mzuelch/CATs-Eurosynth/Modules/HAGIWO/Arduino VCO/ReadMe.md

<h1>Known Issues</h1>
<table>
	<tr>
		<th>#</th>
		<th>Solved?</th>
		<th>Hardware</th>
		<th>Firmware</th>
		<th>Issue</th>
	</tr>
	<tr>
		<td>001</td>
		<td>Yes</td>
		<td>X</td>
		<td></td>
		<td>Output level restricted to +/-2.5V by design. Amplification to eurorack standard (+/-5V) needed.</td>
	</tr>
	<tr>
		<td>002</td>
		<td>No</td>
		<td></td>
		<td>X</td>
		<td>Chord firmware produces low level output.</td>
	</tr>
</table>
