mzuelch/CATs-Eurosynth/Modules/Slim Line/Sample&Hold SMD/README.md

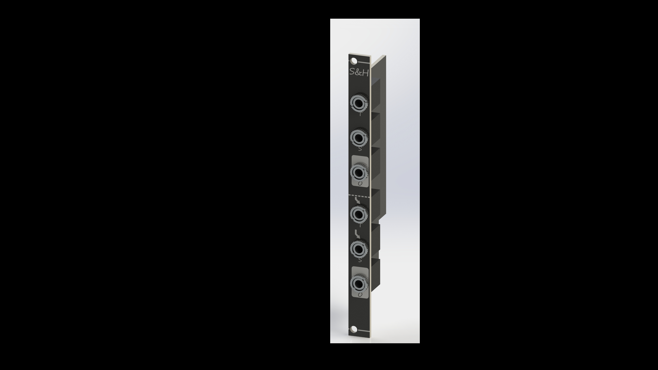
[picture p4: Modules/Slim Line/Sample&Hold/Documentation/Rendering.jpg]
Rendering
