mzuelch/CATs-Eurosynth/Modules/Slim Line/Single Attenuator/README.md

Simple 1CH Attentuator, but with a 60mm travel
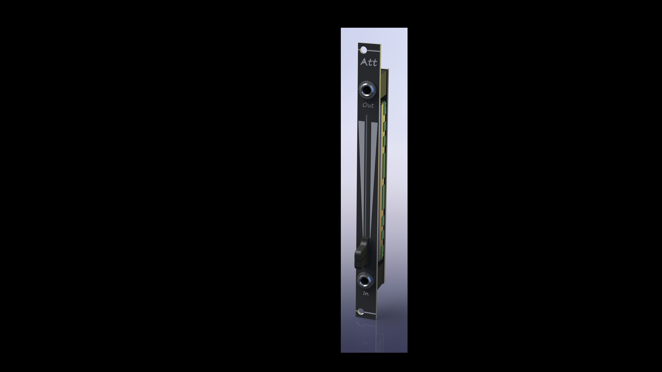
[picture p5: Modules/Slim Line/Single Attenuator/Documentation/Rendering.JPG]
Rendering
