mzuelch/CATs-Eurosynth/Modules/HAGIWO/Multiout/Firmware/Reworked/HAGIWO_Quantizer_Interrupt/ReadMe.md

<h2>Dependecies</h2>
<table>
	<tr>
		<th>Library</th>
		<th>Version</th>		
	</tr>
	<tr>
		<td>Adafruit GFX Library</td>
		<td>1.10.13</td>
	</tr>
	<tr>
		<td>Adafruit SSD1306</td>
		<td>2.5.1</td>
	</tr>
	<tr>
		<td>EncoderButton</td>
		<td>1.0.4</td>
	</tr>
	<tr>
		<td>FlashStorage_SAMD</td>
		<td>1.3.2</td>
	</tr>
</table>
