mzuelch/CATs-Eurosynth/Modules/Slim Line/Buffered Multiple SMD/Documentation/Handbuch.pdf

# Buffered Multiple

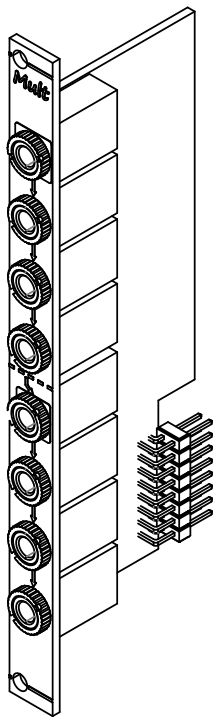
[picture p8: figure]

2 HP Width

39mm w/o Connector

+12V: 15mA

-12V: 15mA

Maximum Depth

Current Draw

## cations fi Technical Speci

## Function

This is a dual buffered 1-in-3 multiple. The signal applied to the input socket appears as a buffered signal at the three output sockets. Each output has it's own buffer, i.e. the three output sockets are not simply connected to each other. The lower output of the upper unit is normalled in the factory to the input of the lower unit. That way the module works as a single 1-in-6 buffered multiple provided that no signal is applied to the input of the lower unit.

## Installation

When installing or removing a module from your case always turn the power to the case and ffo disconnect the power cable. Failure to do so may result in serious injury

or equipment damage.

Ensure the 10-pin connector on the power cable is connected correctly to the module before proceeding.

The red stripe on the cable must line up with the -12V pins on the module’s power connector. The pins are indicated with the label

-12V, a white stripe next to the connector, the words “red”, or

some combination of those

indicators.

# CATs EuroSynth

Dr. Michael Zülch
cats.synth@gmx.de
