mzuelch/CATs-Eurosynth/Modules/Slim Line/Rectifier SMD/Documentation/Handbuch.pdf

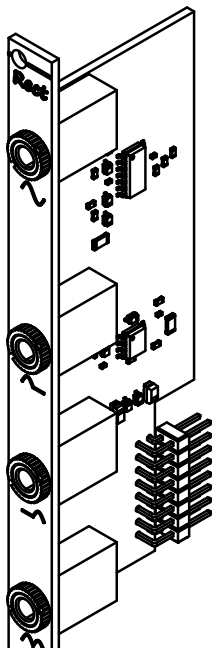
[picture p9: figure]

# CATs EuroSynth

Dr. Michael Zülch
cats.synth@gmx.de

# Precision Rectifier


2 HP Width

39mm w/o Connector

+12V: 15mA

-12V: 15mA

Maximum Depth

Current Draw

# cations fi Technical Speci

# Function

This is a combined halfwave and fullwave er. It can be used as an AC to DC fi precision recti converter, a distortion, a complex waveform generator, a frequency doubler, a clock doubler or even as part of an envelope follower.

Any bipolar signal provided signal (+/-10V) inluding audio signals provided at the input will erent ff be available on the three outputs in di

form.

will provide the signals positive values Output 1 as they are and cut negative values to 0V.

will do the same but with an inverted Output 2 signal, so originally positive values will be cut to

0V and negative values will be made positive.

ed version of the fi provides a fully reci Output 3 input. Positive inputs will be sent as it is, negative portions of the signal will be made positive and also sent to the output.

# Installation

When installing or removing a module from your case always turn the power to the case and ffo disconnect the power cable. Failure to do so may result in serious injury

or equipment damage.

Ensure the 10-pin connector on the power cable is connected correctly to the module before proceeding.

The red stripe on the cable must line up with the -12V pins on the module’s power connector. The pins are indicated with the label

-12V, a white stripe next to the connector, the words “red”, or

some combination of those

indicators.
