mzuelch/CATs-Eurosynth/Modules/Slim Line/Voltage Controlled Switch/Documentation/Handbuch.pdf

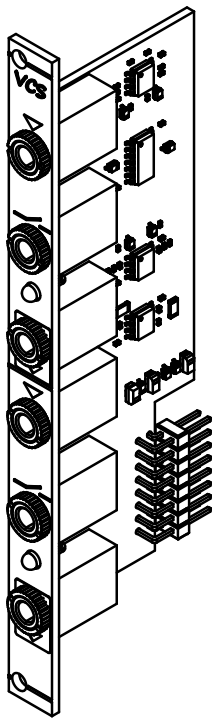
[picture p10: figure]

# CATs EuroSynth

Dr. Michael Zülch
cats.synth@gmx.de

# Voltage Controlled Switch


2 HP Width

39mm w/o Connector

+12V: 40mA

-12V: 10mA

Maximum Depth

Current Draw

# cations fi Technical Speci

# Function

The module provides two completely independent voltage controlled switches.

The switching is activated with a control voltage at a switching threshold of about 120mV and its status is indicated by LED.

The switches are unidirectional and are routing

only from In to Out.

The switches accept signals in a wide range

+/-10V are able to switch audio grade signals but are also suitable for gates, triggers, and

control voltages.

In

## In In

## Gate

## Gate Gate

## Out

## Out Out

⇨

⇨

⇨

⇨

⇦

⇦

# Installation

When installing or removing a module from your case always turn the power to the case and ffo disconnect the power cable. Failure to do so may result in serious injury

or equipment damage.

Ensure the 10-pin connector on the power cable is connected correctly to the module before proceeding.

The red stripe on the cable must line up with the -12V pins on the module’s power connector. The pins are indicated with the label

-12V, a white stripe next to the connector, the words “red”, or

some combination of those

indicators.
