mzuelch/CATs-Eurosynth/Modules/Standard Line/LFO/README.md

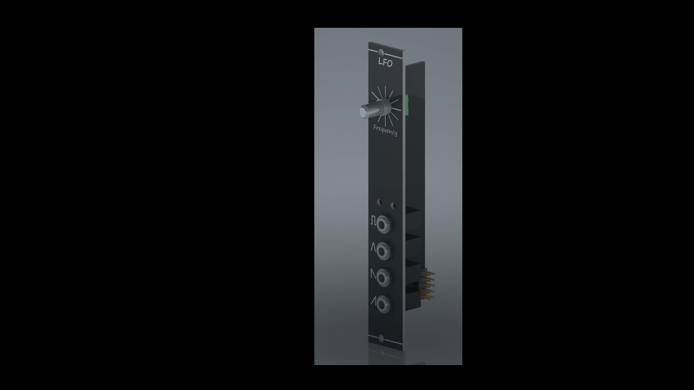
[picture p12: Modules/Haraldswerk/NGF-E LFO/Documentation/Rendering.jpg]
Rendering
