mzuelch/CATs-Eurosynth/Modules/YuSynth/Improved Steiner VCF/README.md

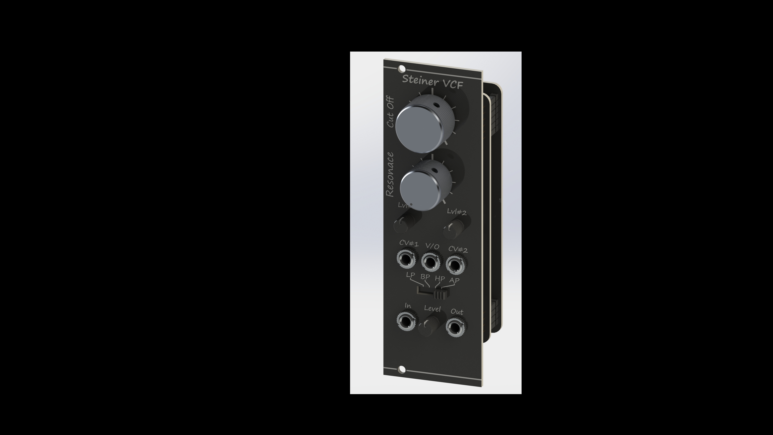
[picture p13: Modules/YuSynth/Improved Steiner VCF/Documentation/Rendering.jpg]
Rendering
