mzuelch/CATs-Eurosynth/Modules/Standard Line/Baby8 Sequencer/README.md

Baby8 Sequencer
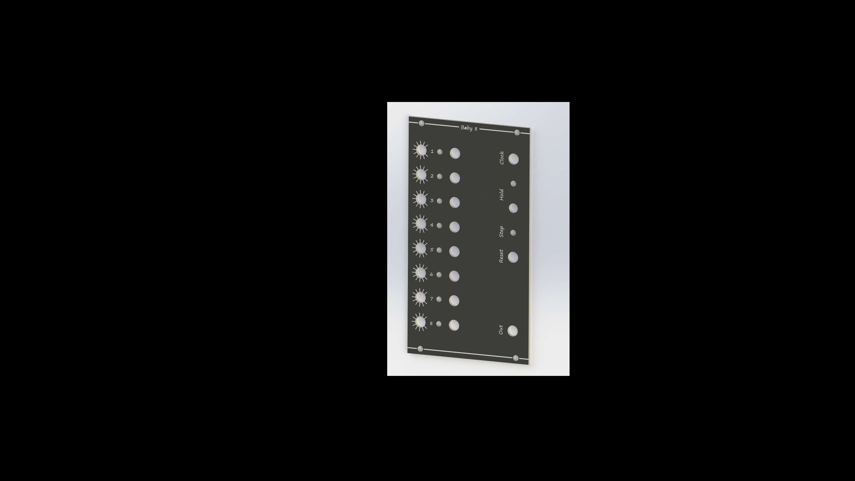
[picture p14: Modules/Standard Line/Baby8 Sequencer/Documentation/Rendering.jpg]
Rendering
