mzuelch/CATs-Eurosynth/Modules/MFOS/Dual VCA #2/README.md

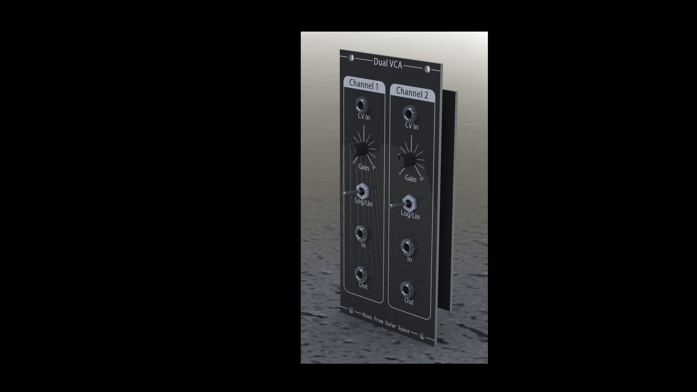
[picture p15: Modules/MFOS/Dual VCA #2/Documentation/Rendering.JPG]
Rendering
