mzuelch/CATs-Eurosynth/Modules/Slim Line/Clock Divider/Documentation/Handbuch.pdf

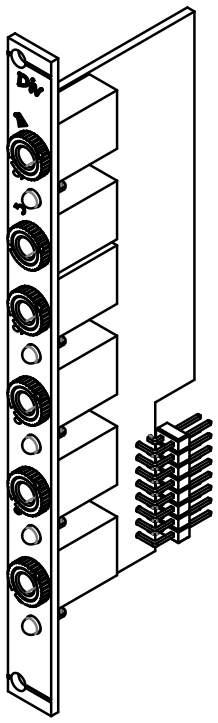
[picture p17: figure]

# CATs EuroSynth

Dr. Michael Zülch
cats.synth@gmx.de

# Clock Divider

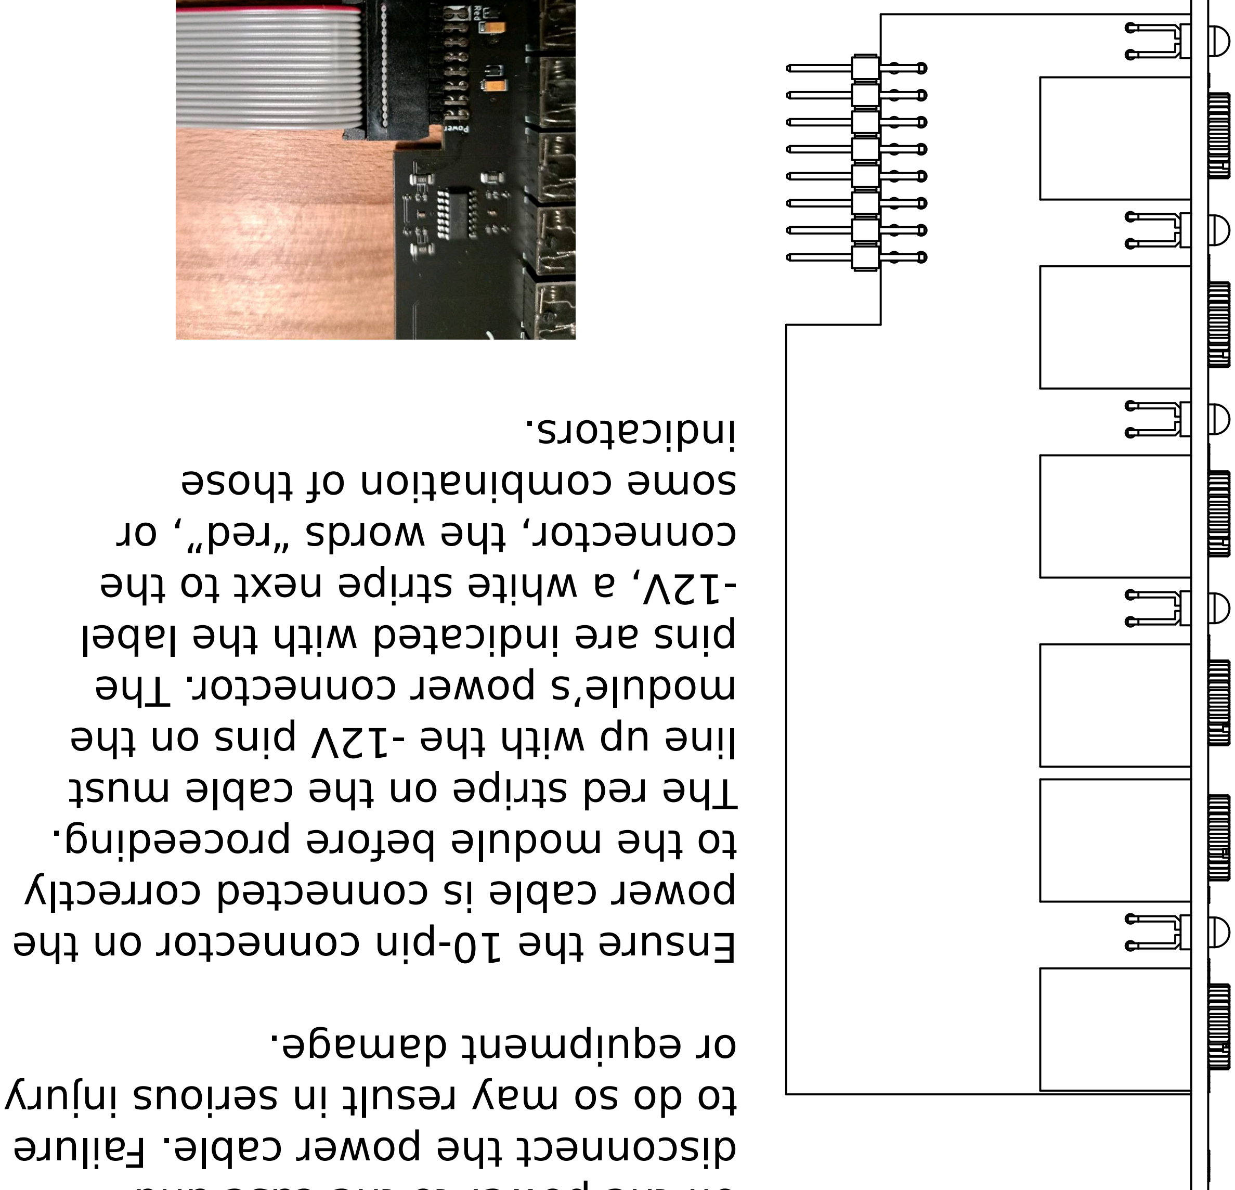
[picture p18: figure]
disconnect the power cable. Failure; to do so may result in serious injury; or equipment damage.; Ensure the 10-pin connector on the; power cable is connected correctly; to the module before proceeding.; The red stripe on the cable must; line up with the -12V pins on the; module’s power connector. The; pins are indicated with the label; -12V, a white stripe next to the; connector, the words “red”, or; some combination of those; indicators.

# Installation

When installing or removing a module from your case always turn the power to the case and ffo

2 HP Width

39mm w/o Connector

+12V: 80mA

-12V: 5mA

Maximum Depth

Current Draw

# cations fi Technical Speci

# Function

The module is a frequency divider for clock, trigger or gate signals, designed to be a source of lower frequencies, particularly for rhythm uses.

The clock input (CLK) will take any signal +/-10V.

erent ff At the outputs, you have access to four di sub-divided clock signals, from half the clock frequency down to 1/16 (Q1-Q4). The low/high levels of the output signals are 0V and about +5V.

The module also has a reset (RST) input.

Whenever a reset signal is sensed, all outputs are

set to 0V.

## CLK

## RST

Q1

Q2

Q3

Q4

CLK RST Q1 Q2Q3 Q4

⇨

⇨

⇦

⇦

⇦

⇦
