mzuelch/CATs-Eurosynth/Modules/CGS/Analog Switch Matrix/Documentation/Rendering.jpg

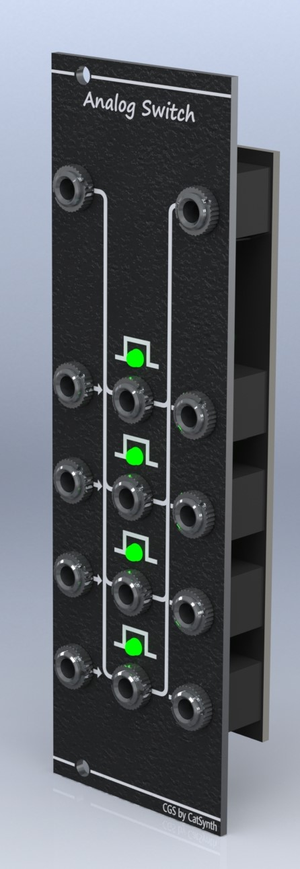
Modules/CGS/Analog Switch Matrix/Documentation/Rendering.jpg
