mzuelch/CATs-Eurosynth/Modules/HAGIWO/4Ch Sample Player/Electronics/Front/HAGIWO Sampler Front.png

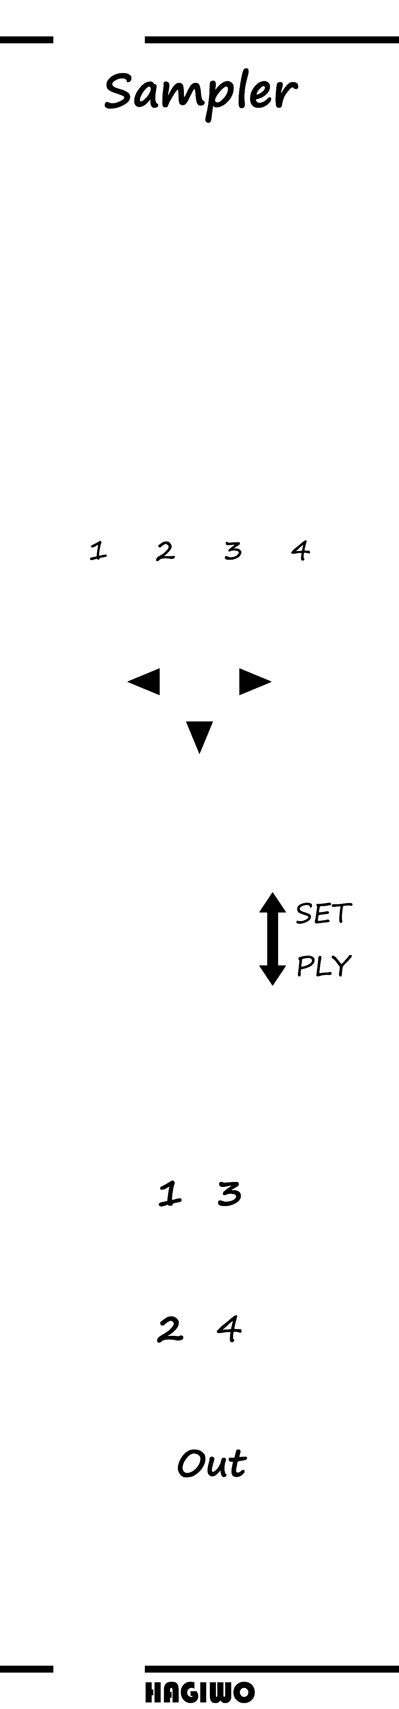
Modules/HAGIWO/4Ch Sample Player/Electronics/Front/HAGIWO Sampler Front.png
