mzuelch/CATs-Eurosynth/Modules/HAGIWO/Arduino VCO/Mechanics/HAGIWO Arduino VCO 2Op FM Front.png

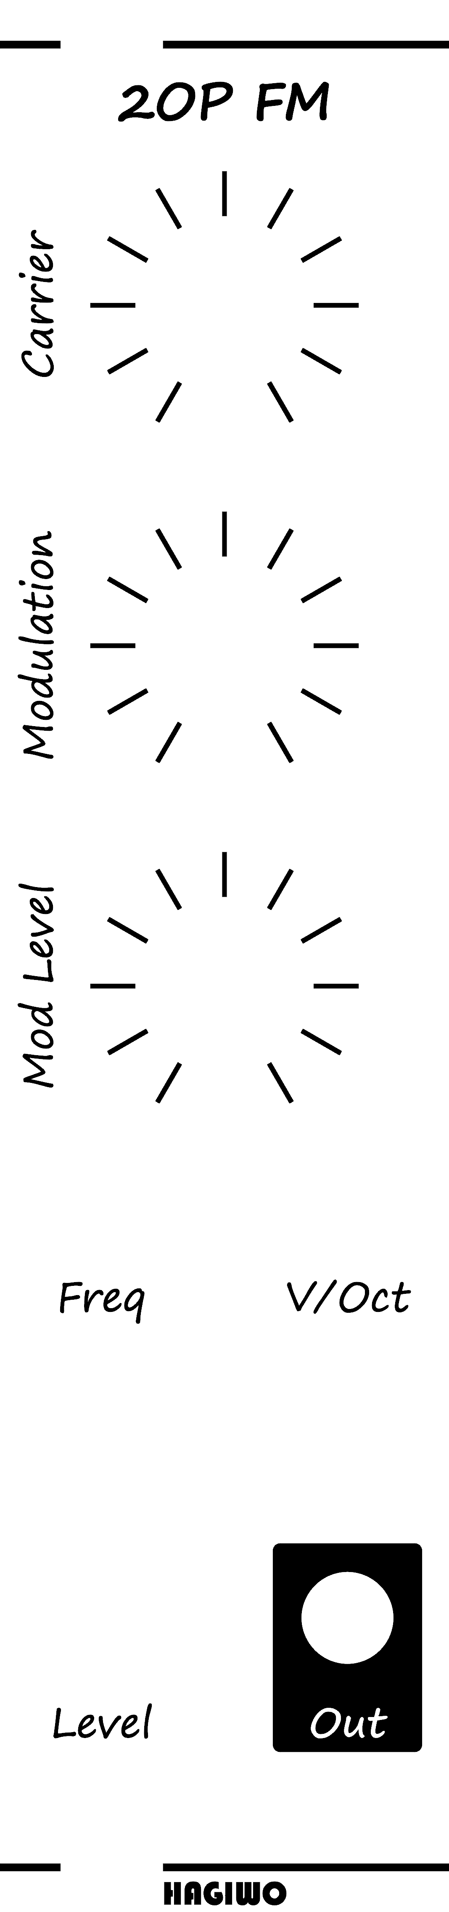
Modules/HAGIWO/Arduino VCO/Mechanics/HAGIWO Arduino VCO 2Op FM Front.png
