mzuelch/CATs-Eurosynth/Modules/HAGIWO/Multiout/Mechanics/HAGIWO Quantizer Frontpanel.png

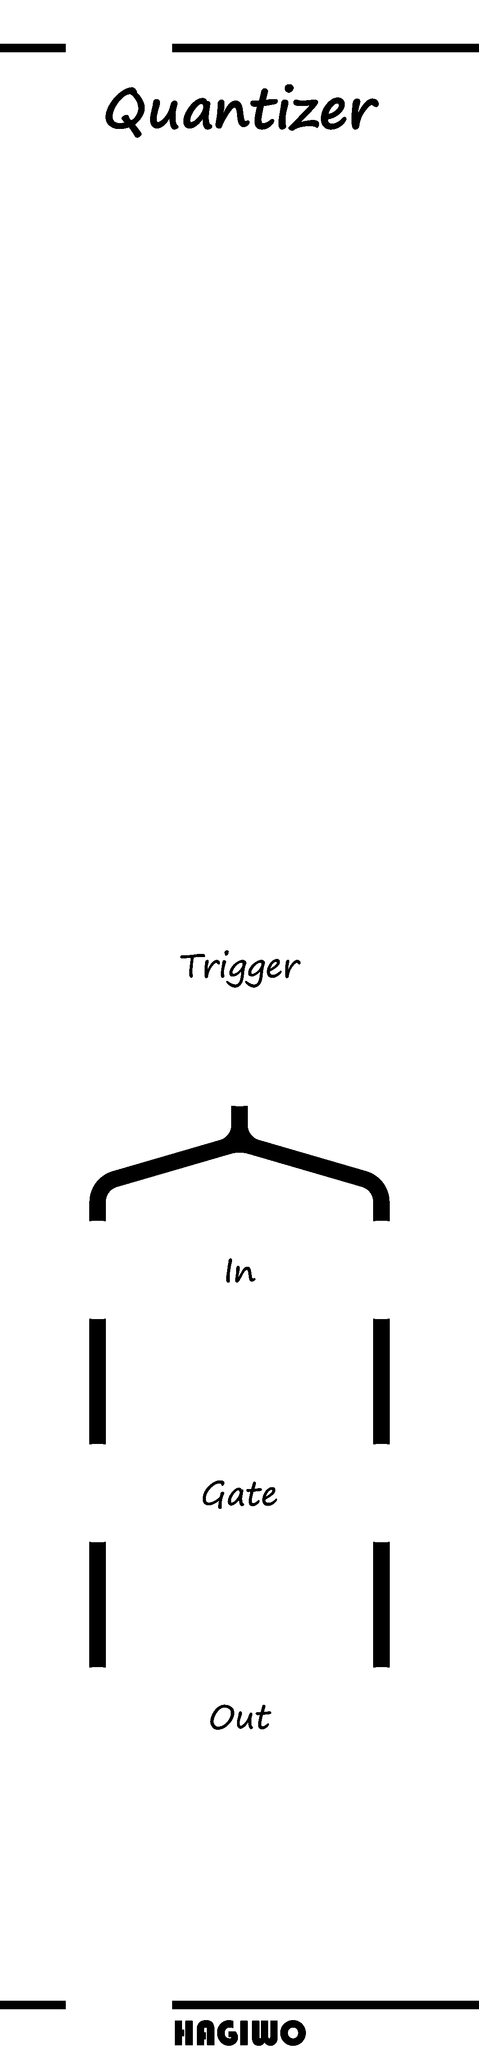
Modules/HAGIWO/Multiout/Mechanics/HAGIWO Quantizer Frontpanel.png
