mzuelch/CATs-Eurosynth/Modules/HAGIWO/Sync LFO/Mechanics/HAGIWO Sync LFO Front.png

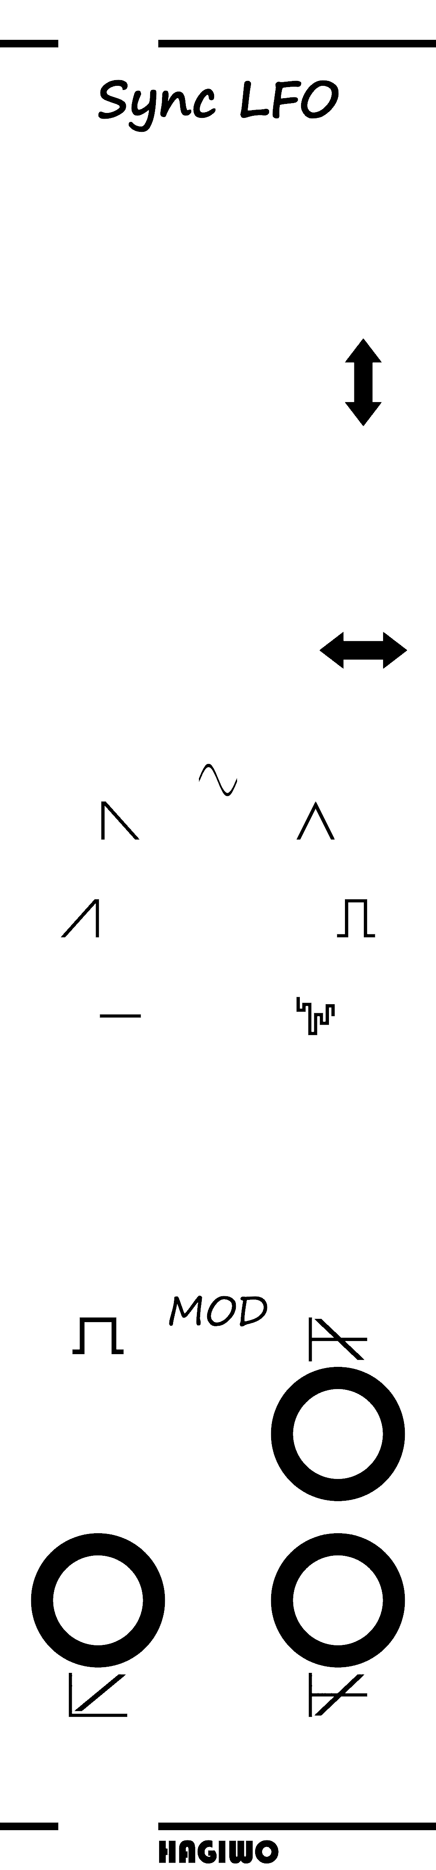
Modules/HAGIWO/Sync LFO/Mechanics/HAGIWO Sync LFO Front.png
