mzuelch/CATs-Eurosynth/Modules/Mechanicals/Cases/Case 1x3HE 84HP.JPG

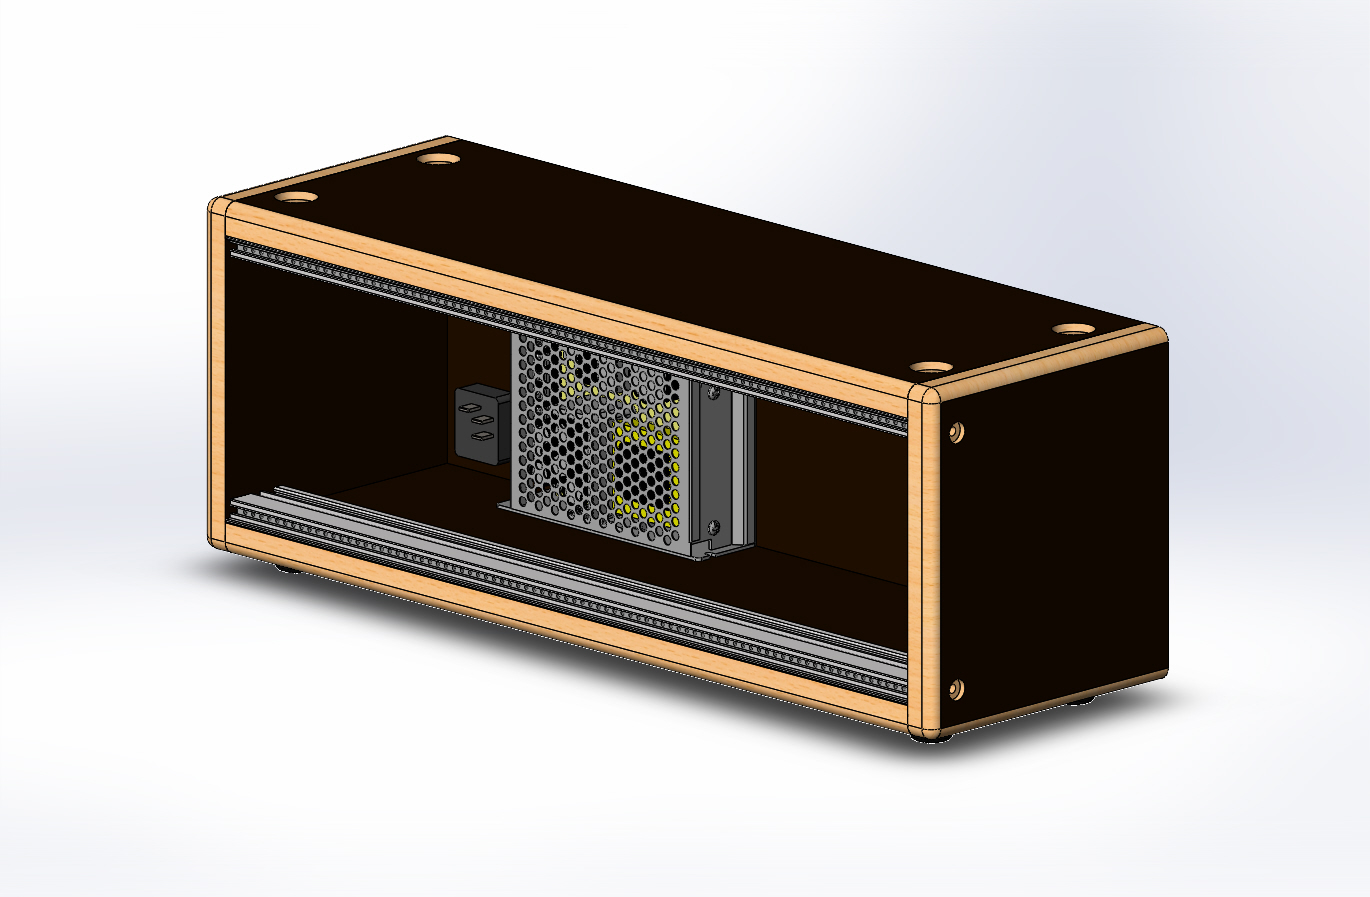
Modules/Mechanicals/Cases/Case 1x3HE 84HP.JPG
