mzuelch/CATs-Eurosynth/Modules/Mechanicals/Cases/Case 2x3HE 84HP.JPG

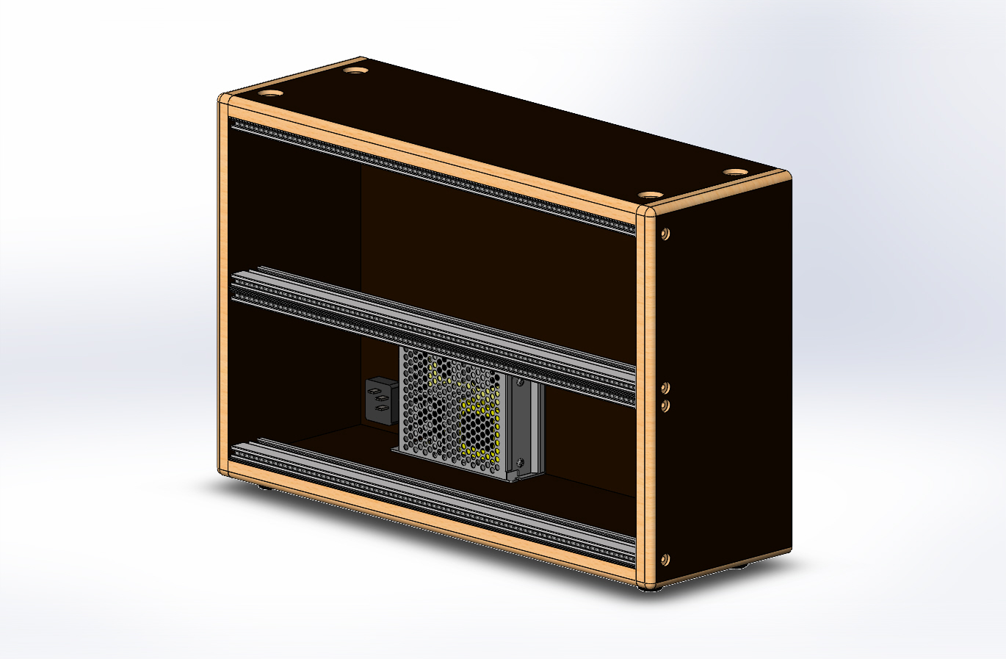
Modules/Mechanicals/Cases/Case 2x3HE 84HP.JPG
