mzuelch/CATs-Eurosynth/Modules/Mechanicals/Cases/Case 3x3HE 84HP.JPG

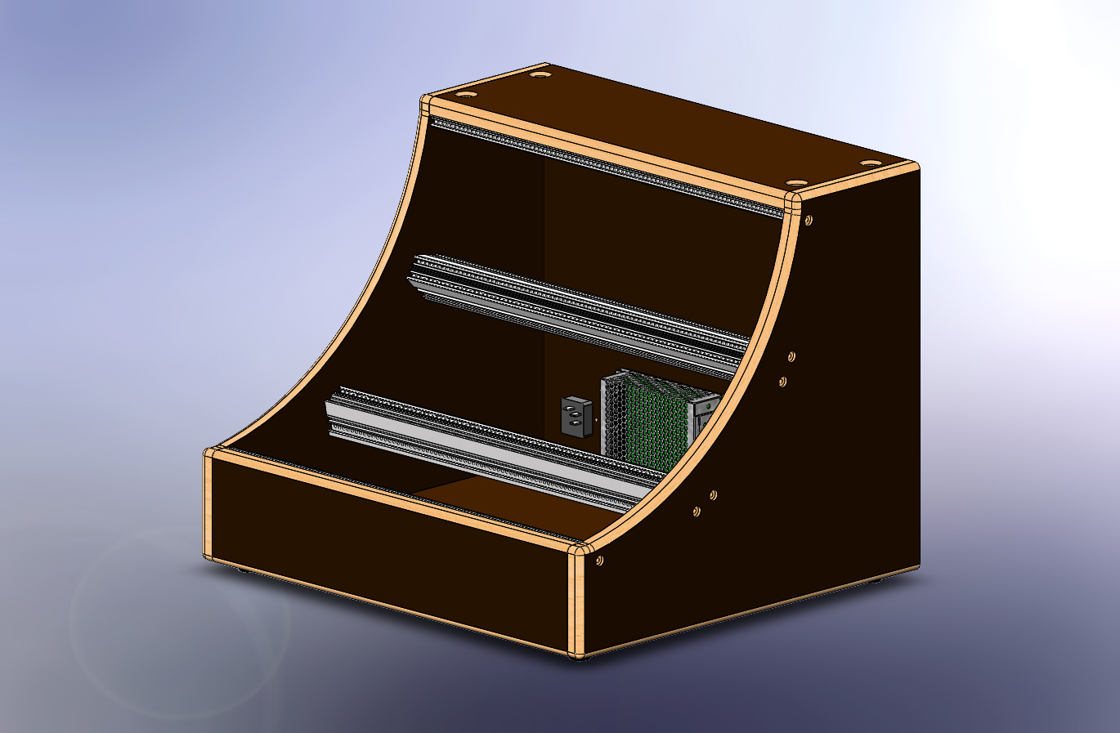
Modules/Mechanicals/Cases/Case 3x3HE 84HP.JPG
