mzuelch/CATs-Eurosynth/Modules/Slim Line/Buffered Multiple SMD/Documentation/20230219_085442.jpg

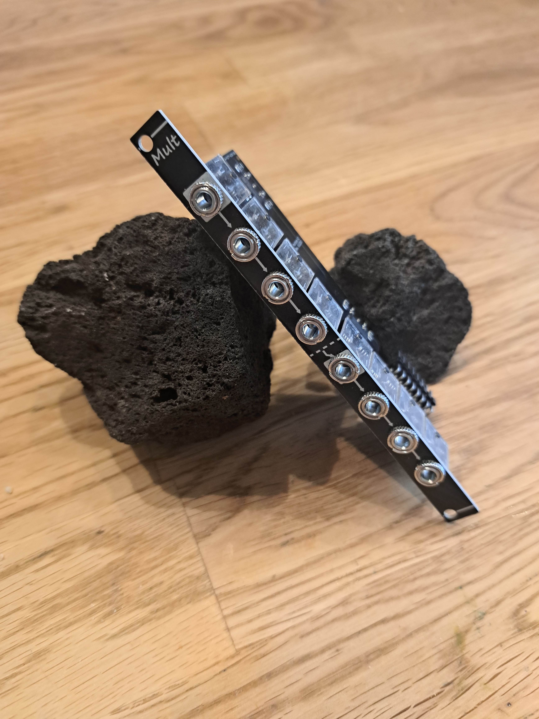
Modules/Slim Line/Buffered Multiple SMD/Documentation/20230219_085442.jpg
