mzuelch/CATs-Eurosynth/Modules/Slim Line/Buffered Multiple SMD/Documentation/Handbuch Seite 2.png

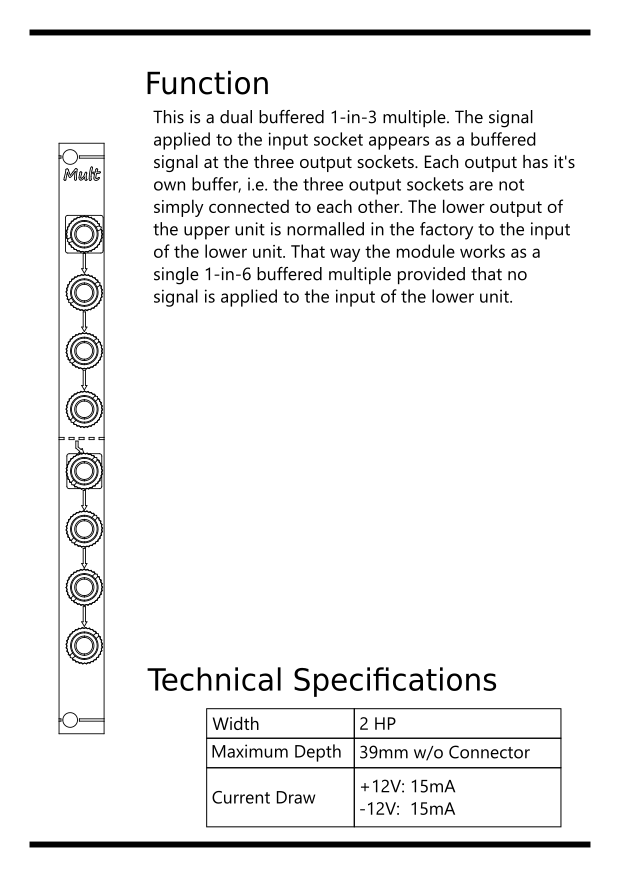
Modules/Slim Line/Buffered Multiple SMD/Documentation/Handbuch Seite 2.png
