mzuelch/CATs-Eurosynth/Modules/Slim Line/Clock Divider/Mechanics/Slimline Clock Divider Module Front.JPG

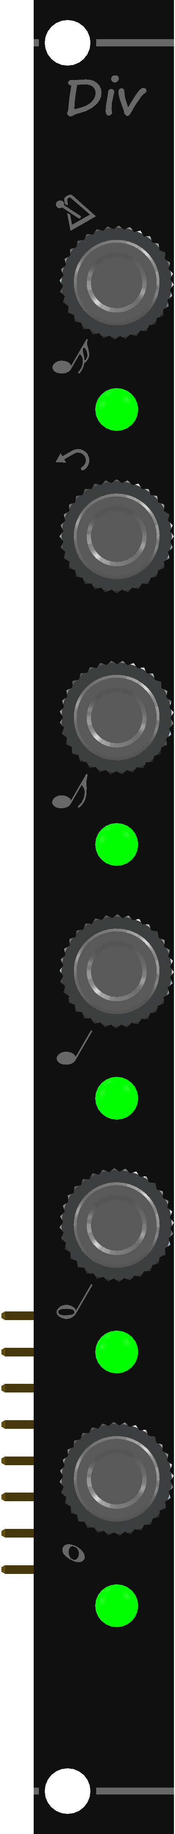
Modules/Slim Line/Clock Divider/Mechanics/Slimline Clock Divider Module Front.JPG
