mzuelch/CATs-Eurosynth/Modules/Slim Line/Clock Divider/Mechanics/Slimline Clock Divider V2 Front.png

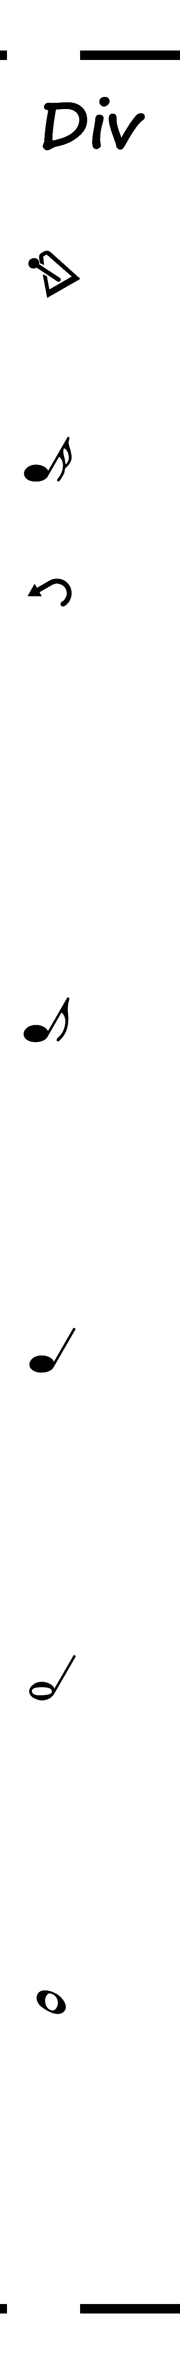
Modules/Slim Line/Clock Divider/Mechanics/Slimline Clock Divider V2 Front.png
