mzuelch/CATs-Eurosynth/Modules/Slim Line/Precision Adder/Mechanics/Slimline Precision Adder Front.png

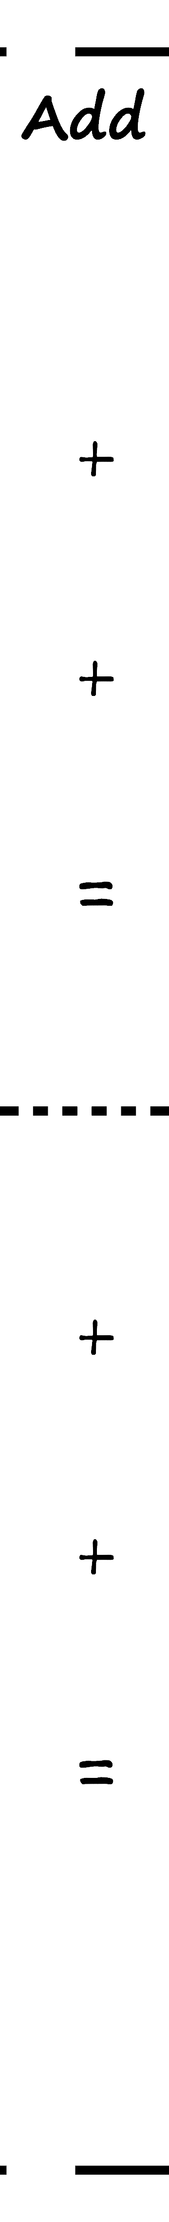
Modules/Slim Line/Precision Adder/Mechanics/Slimline Precision Adder Front.png
