mzuelch/CATs-Eurosynth/Modules/Slim Line/Rectifier SMD/Documentation/ec778fda-3ce0-42d2-8429-7ae5b2f354bd.jpeg

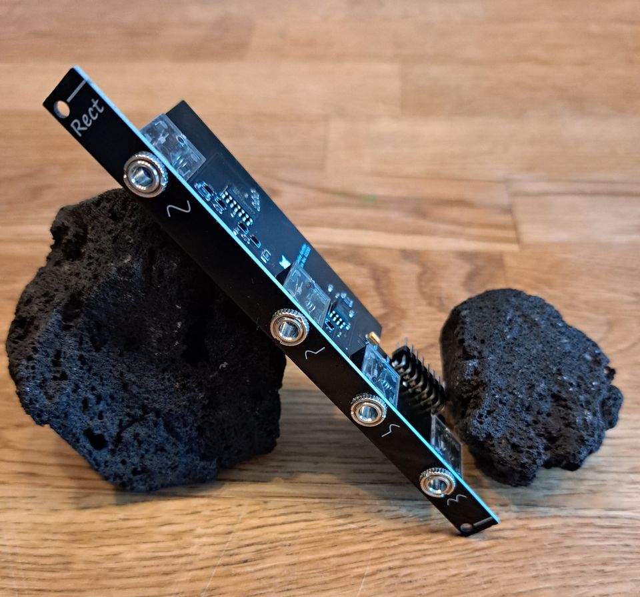
Modules/Slim Line/Rectifier SMD/Documentation/ec778fda-3ce0-42d2-8429-7ae5b2f354bd.jpeg
