mzuelch/CATs-Eurosynth/Modules/Slim Line/Rectifier SMD/Documentation/Handbuch Seite 1.png

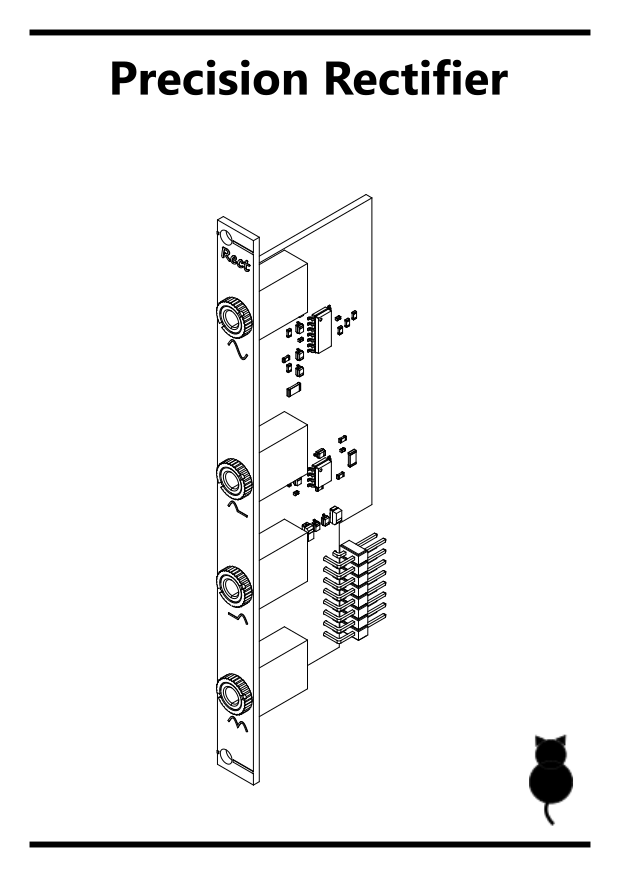
Modules/Slim Line/Rectifier SMD/Documentation/Handbuch Seite 1.png
