mzuelch/CATs-Eurosynth/Modules/Slim Line/Rectifier SMD/Documentation/Handbuch Seite 2.png

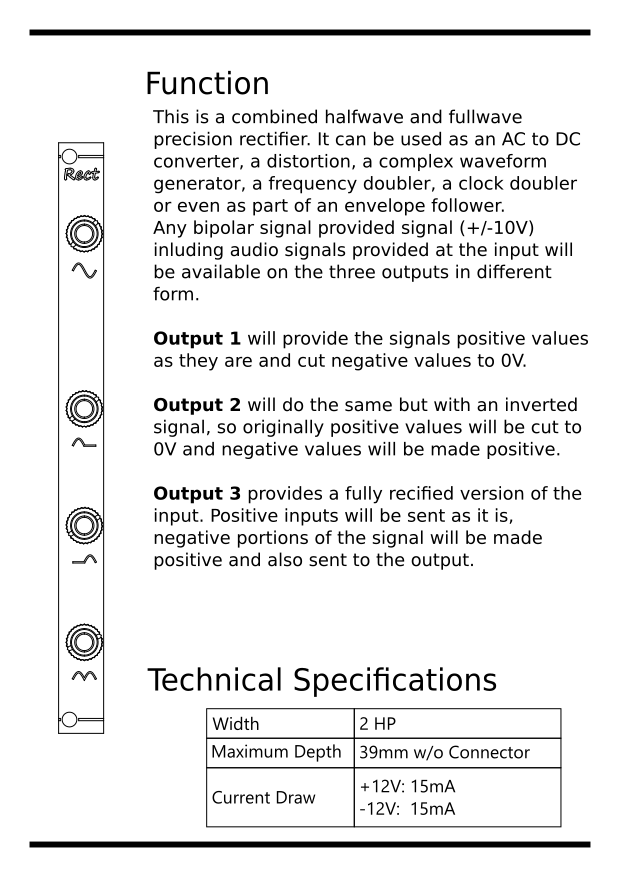
Modules/Slim Line/Rectifier SMD/Documentation/Handbuch Seite 2.png
