mzuelch/CATs-Eurosynth/Modules/Slim Line/Rectifier SMD/Documentation/Handbuch Seite 3.png

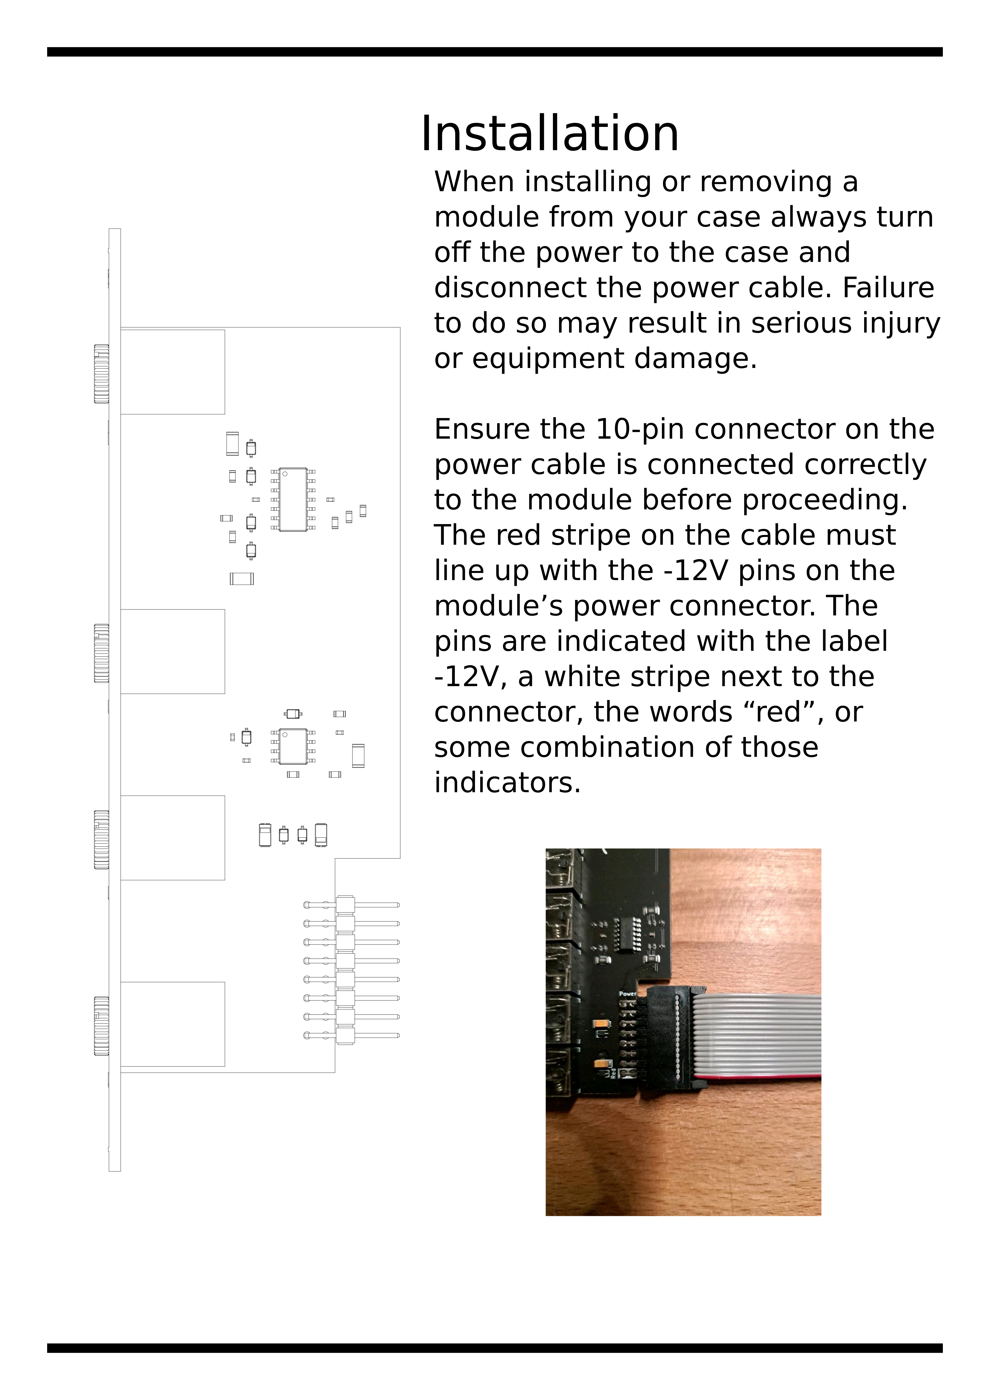
Modules/Slim Line/Rectifier SMD/Documentation/Handbuch Seite 3.png
