mzuelch/CATs-Eurosynth/Modules/Slim Line/Rectifier SMD/Documentation/Rendering.png

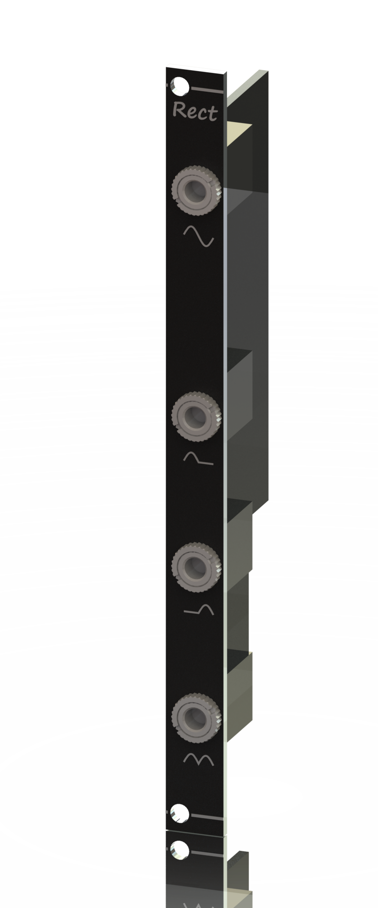
Modules/Slim Line/Rectifier SMD/Documentation/Rendering.png
