mzuelch/CATs-Eurosynth/Modules/Slim Line/Rectifier SMD/Mechanics/Slimline Rectifier Front.png

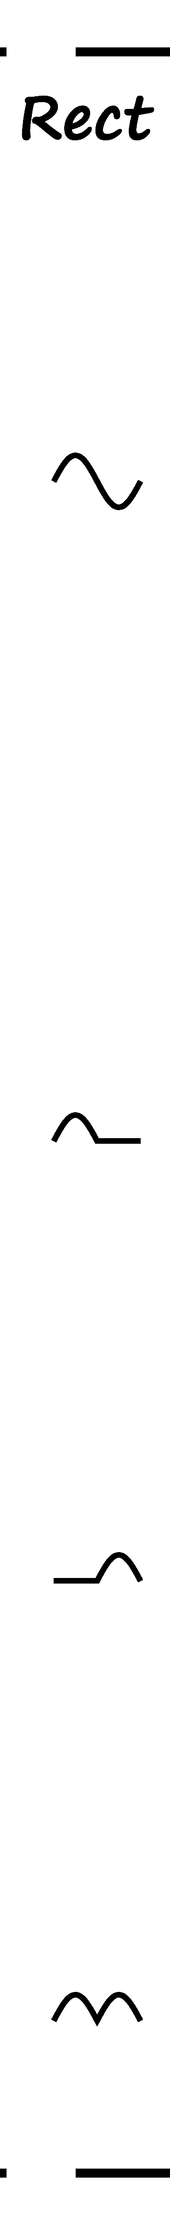
Modules/Slim Line/Rectifier SMD/Mechanics/Slimline Rectifier Front.png
