mzuelch/CATs-Eurosynth/Modules/Slim Line/Sample&Hold SMD/Documentation/Handbuch Seite 2.png

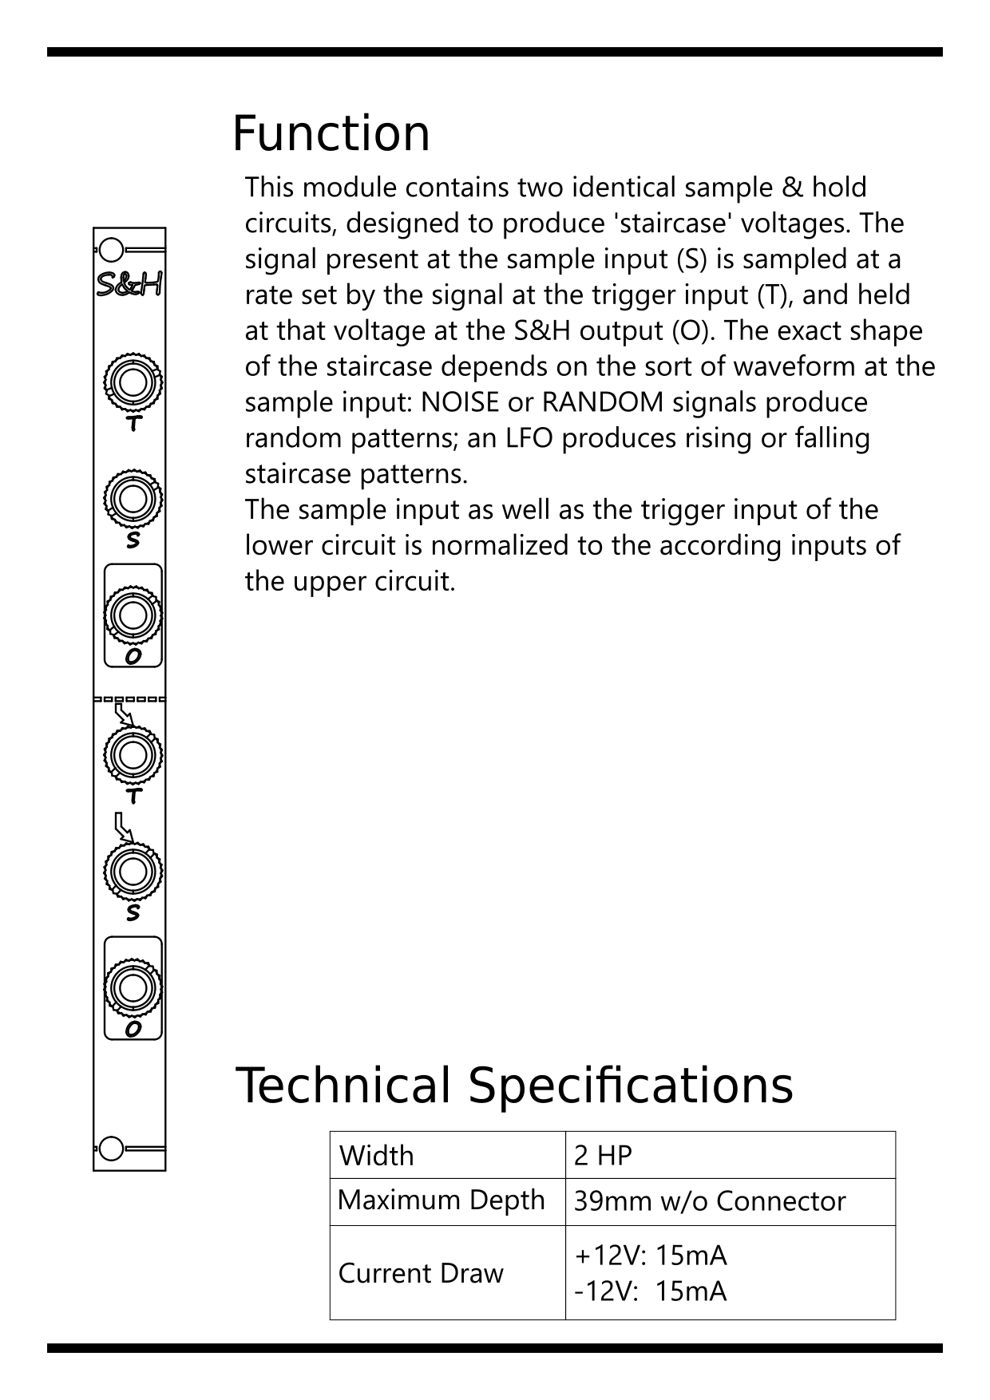
Modules/Slim Line/Sample&Hold SMD/Documentation/Handbuch Seite 2.png
