mzuelch/CATs-Eurosynth/Modules/Slim Line/Sample&Hold SMD/Documentation/Handbuch Seite 3.png

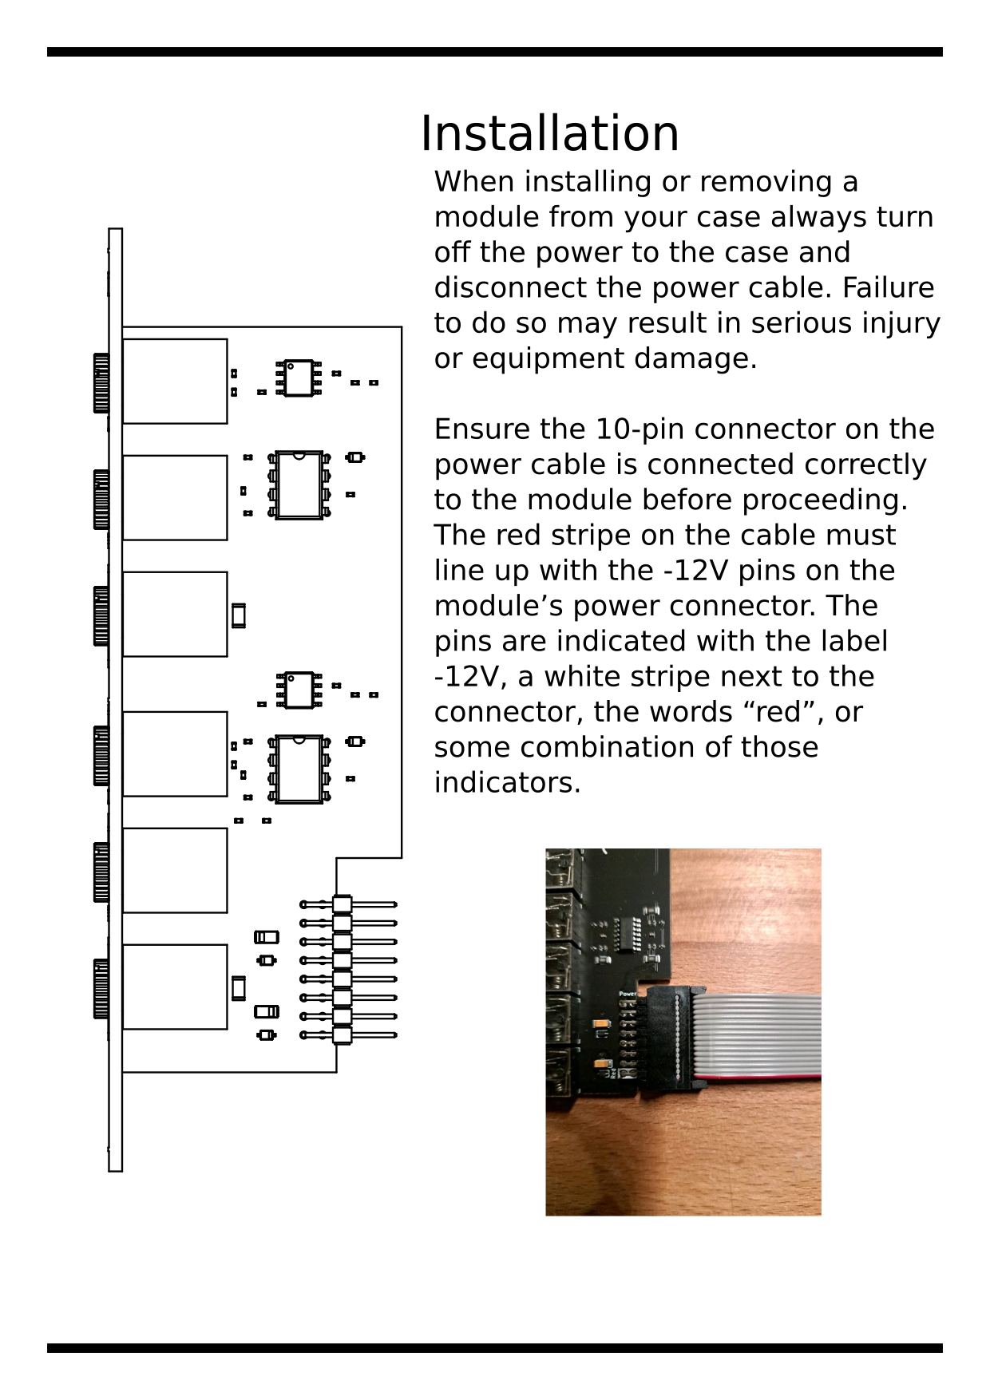
Modules/Slim Line/Sample&Hold SMD/Documentation/Handbuch Seite 3.png
