mzuelch/CATs-Eurosynth/Modules/Slim Line/Voltage Controlled Switch/Documentation/ea97082e-4144-41ba-bf36-c3e3d4d441ec.jpeg

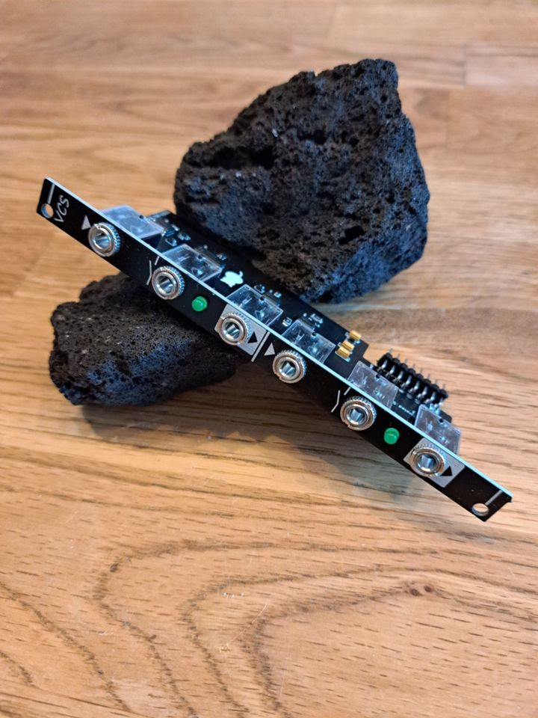
Modules/Slim Line/Voltage Controlled Switch/Documentation/ea97082e-4144-41ba-bf36-c3e3d4d441ec.jpeg
