mzuelch/CATs-Eurosynth/Modules/Slim Line/Voltage Controlled Switch/Documentation/Handbuch Seite 1.png

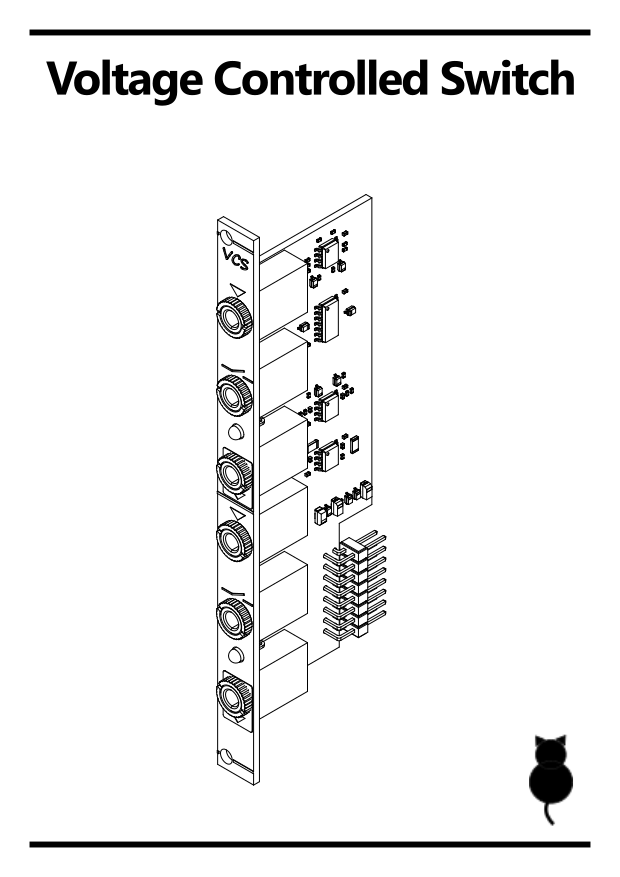
Modules/Slim Line/Voltage Controlled Switch/Documentation/Handbuch Seite 1.png
