mzuelch/CATs-Eurosynth/Modules/Slim Line/Voltage Controlled Switch/Mechanics/Slimline Voltage Controlled Switch Front.png

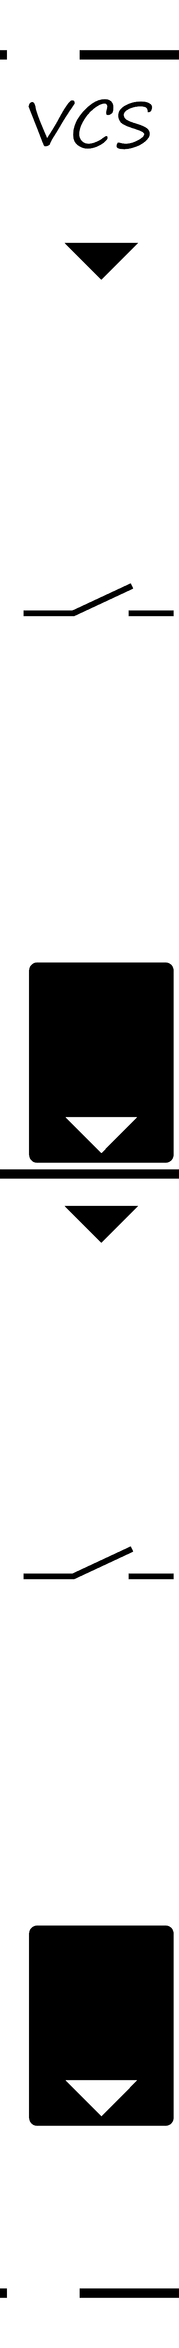
Modules/Slim Line/Voltage Controlled Switch/Mechanics/Slimline Voltage Controlled Switch Front.png
