mzuelch/CATs-Eurosynth/Modules/Slim Line/Voltage Controlled Switch/Mechanics/Slimline Voltage Controlled Switch Module Front.JPG

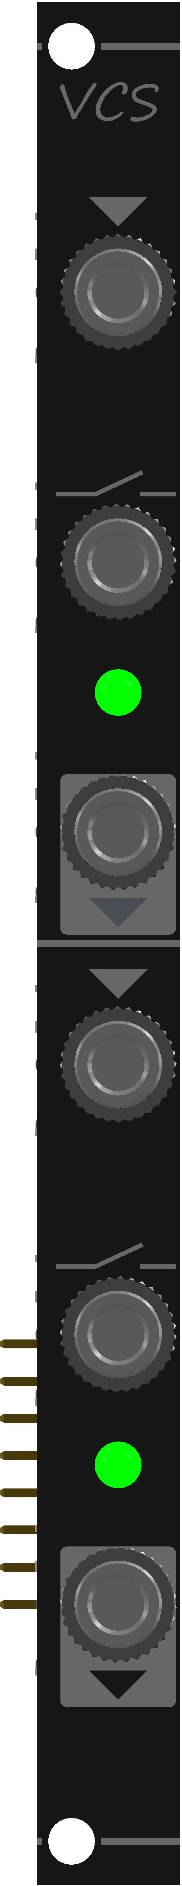
Modules/Slim Line/Voltage Controlled Switch/Mechanics/Slimline Voltage Controlled Switch Module Front.JPG
