mzuelch/CATs-Eurosynth/Modules/Standard Line/4Ch Mixer/Electronics/Front/4CH Mixer Frontpanel Druck.png

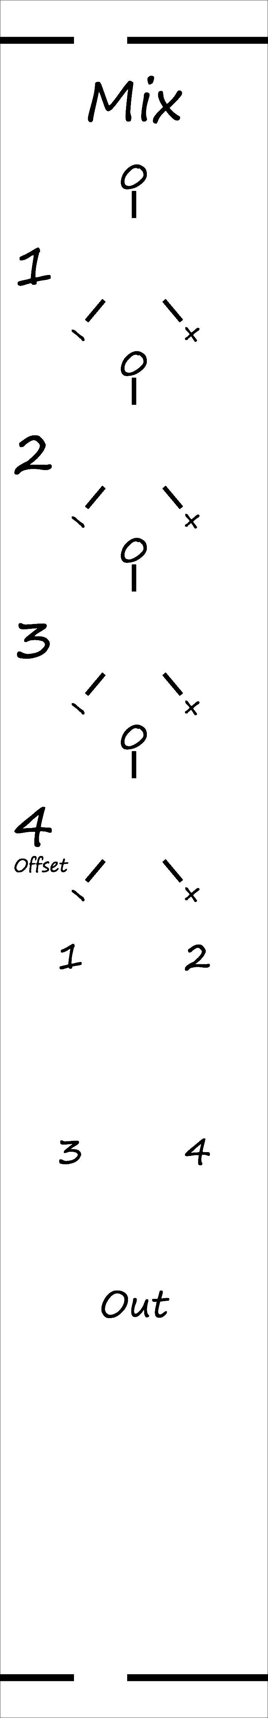
Modules/Standard Line/4Ch Mixer/Electronics/Front/4CH Mixer Frontpanel Druck.png
