mzuelch/CATs-Eurosynth/Modules/Standard Line/Atari Punk Console/Documentation/Rendering.jpg

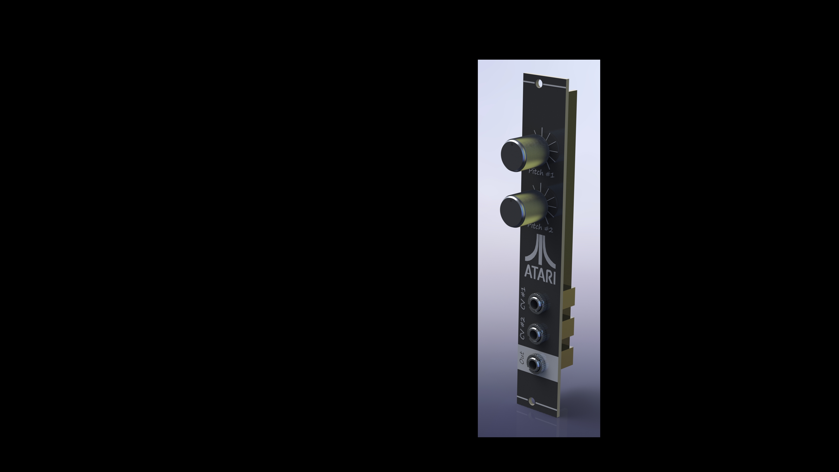
Modules/Standard Line/Atari Punk Console/Documentation/Rendering.jpg
