mzuelch/CATs-Eurosynth/Modules/YuSynth/Improved Steiner VCF/Electronics/Front/Improved Steiner VCF Frontplatte.png

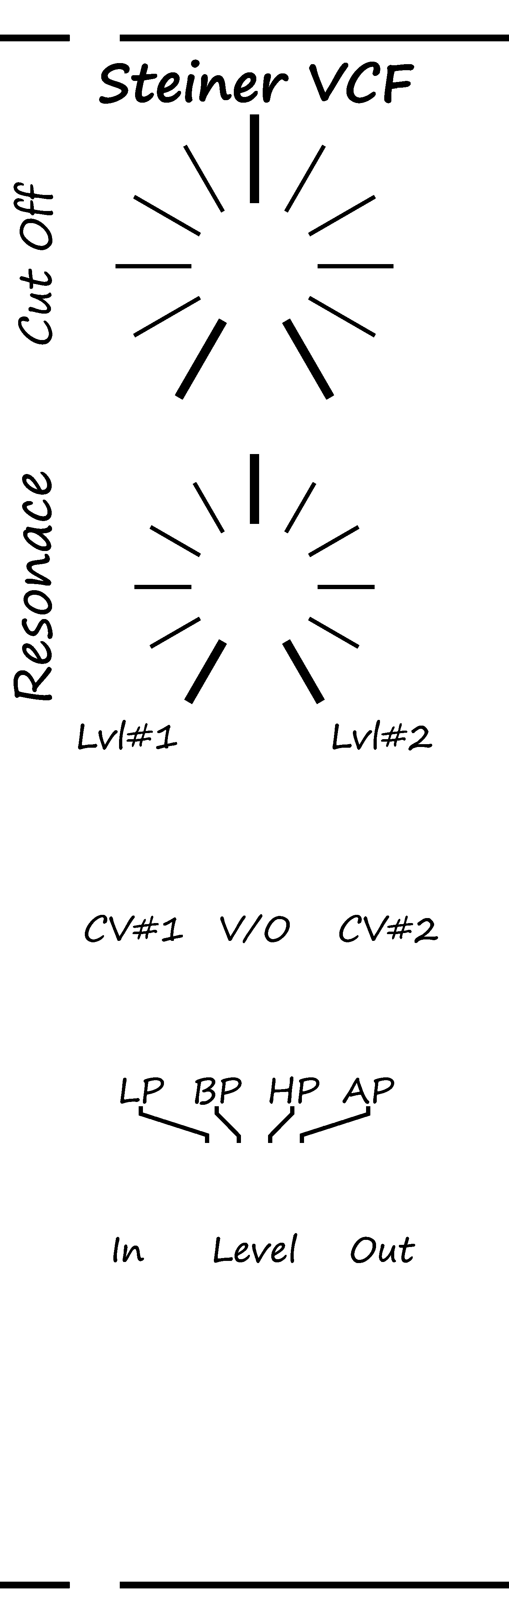
Modules/YuSynth/Improved Steiner VCF/Electronics/Front/Improved Steiner VCF Frontplatte.png
