mzuelch/CATs-Eurosynth/Modules/Slim Line/Precision Adder/Gerber/Rev. 012202/Slim Precision Adder Main - BOM.xls

Comment | Designator | Footprint | LCSC
10u | C1 C6 | Capacitor_Tantalum_SMD:CP_EIA-3216-18_Kemet-A | C7171
100n | C2 C3 C4 C5 C7 C8 C9 C10 | Capacitor_SMD:C_0603_1608Metric | C14663
B5819W SL | D1 D2 | Diode_SMD:D_SOD-123 | C8598
In 1-1 | J1 | Connector_Audio_QingPu:Jack_3.5mm_QingPu_WQP-PJ324M
Out 1 | J2 | Connector_Audio_QingPu:Jack_3.5mm_QingPu_WQP-PJ324M
In 1-2 | J3 | Connector_Audio_QingPu:Jack_3.5mm_QingPu_WQP-PJ324M
In 1-3 | J4 | Connector_Audio_QingPu:Jack_3.5mm_QingPu_WQP-PJ324M
In 2-1 | J5 | Connector_Audio_QingPu:Jack_3.5mm_QingPu_WQP-PJ324M
Out 2 | J6 | Connector_Audio_QingPu:Jack_3.5mm_QingPu_WQP-PJ324M
In 2-2 | J7 | Connector_Audio_QingPu:Jack_3.5mm_QingPu_WQP-PJ324M
In 2-3 | J8 | Connector_Audio_QingPu:Jack_3.5mm_QingPu_WQP-PJ324M
Power | J9 | CATs_Eurosynth_Specials:Power_2x8_Horizontal
100k Â±0.05% | R1 R2 R3 R5 R6 R7 R8 R9 R10 R12 R13 R14 | Resistor_SMD:R_0805_2012Metric | C706399
240 | R4 R11 | Resistor_SMD:R_0805_2012Metric | C17572
20k | RV1 RV2 RV3 RV4 | Potentiometer_THT:Potentiometer_Bourns_3299P_Horizontal
Inv1 | TP1 | TestPoint:TestPoint_THTPad_2.0x2.0mm_Drill1.0mm
Sum1 | TP2 | TestPoint:TestPoint_THTPad_2.0x2.0mm_Drill1.0mm
GND | TP3 | TestPoint:TestPoint_THTPad_2.0x2.0mm_Drill1.0mm
Inv2 | TP4 | TestPoint:TestPoint_THTPad_2.0x2.0mm_Drill1.0mm
Sum2 | TP5 | TestPoint:TestPoint_THTPad_2.0x2.0mm_Drill1.0mm
OP07CDR | U1 U2 U3 U4 | Package_SO:SO-8_3.9x4.9mm_P1.27mm | C7433
