mzuelch/CATs-Eurosynth/Modules/HAGIWO/Sync LFO/Gerber/Rev. 012202/HAGIWO Sync LFO Main - BOM.xls

Comment | Designator | Footprint | LCSC
Arduino_Nano_v3.x | A1 | Module:Arduino_Nano
220p | C1 C2 C3 C4 | Capacitor_SMD:C_0402_1005Metric | C1530
6.8n | C5 | Capacitor_SMD:C_0402_1005Metric | C1542
10n | C6 | Capacitor_SMD:C_0402_1005Metric | C15195
100n | C7 C9 C10 C12 C13 | Capacitor_SMD:C_0402_1005Metric | C1525
10u | C8 C11 | Capacitor_Tantalum_SMD:CP_EIA-3216-18_Kemet-A | C7171
BAV99;215 | D1 | Package_TO_SOT_SMD:SOT-23 | C2500
LED | D2 | LED_THT:LED_D3.0mm
1N5819 | D3 D4 | Diode_SMD:D_SOD-323 | C191023
UP_Out | J1 | Connector_Audio_QingPu:Jack_3.5mm_QingPu_WQP-PJ301M-12
CLK In | J2 | Connector_Audio_QingPu:Jack_3.5mm_QingPu_WQP-PJ301M-12
BP_Inv_Out | J3 | Connector_Audio_QingPu:Jack_3.5mm_QingPu_WQP-PJ301M-12
BP_Out | J4 | Connector_Audio_QingPu:Jack_3.5mm_QingPu_WQP-PJ301M-12
Power | J5 | CATs_Eurosynth_Specials:Power_2x5_Vertical
B100K | P1 P3 P4 | Potentiometer_THT_Additional:Potentiometer_AlpsAlpine_RK09L1140_wo_Fix
B100K | P2 | Potentiometer_THT_Additional:Potentiometer_AlpsAlpine_RK09L1140
470R | R1 R2 R3 R4 | Resistor_SMD:R_0402_1005Metric | C25117
1k | R7 R10 R16 R21 | Resistor_SMD:R_0402_1005Metric | C11702
100k | R12 | Resistor_SMD:R_0402_1005Metric | C25741
20k | R14 | Resistor_SMD:R_0402_1005Metric | C25765
13k | R5 | Resistor_SMD:R_0603_1608Metric | C22797
27k | R6 | Resistor_SMD:R_0402_1005Metric | C25771
300R | R8 | Resistor_SMD:R_0402_1005Metric | C25102
10k | R9 R11 R13 R15 R17 R18 R19 R20 | Resistor_SMD:R_0402_1005Metric | C25744
TL072 | U1 U2 | Package_SO:SOIC-8_3.9x4.9mm_P1.27mm | C6961
