mzuelch/CATs-Eurosynth/Modules/HAGIWO/4Ch Sample Player/Gerber/Rev. 012201/HAGIWO 4Ch Sampler Main - BOM.xls

Comment | Designator | Footprint | LCSC
100uF/6.3V | C1 | Capacitor_Tantalum_SMD:CP_EIA-3528-21_Kemet-B | C16133
1u | C2 | Capacitor_SMD:C_0603_1608Metric | C15849
100n | C6 C8 | Capacitor_SMD:C_0603_1608Metric | C14663
10uF/16V | C3 C4 C5 C7 | Capacitor_Tantalum_SMD:CP_EIA-3216-18_Kemet-A | C7171
BAV99 | D1 D2 D5 D6 | Package_TO_SOT_SMD:SOT-23 | C2500
Ch 1 | D3 | LED_THT:LED_D3.0mm
Ch 3 | D4 | LED_THT:LED_D3.0mm
Ch 2 | D7 | LED_THT:LED_D3.0mm
Ch 4 | D8 | LED_THT:LED_D3.0mm
B5819W SL | D9 D10 | Diode_SMD:D_SOD-123 | C8598
MC096xx | DISP1 | OLED:0.96inch_OLED_MC096GX
Ch. 1 In | J1 | Connector_Audio_QingPu:Jack_3.5mm_QingPu_WQP-PJ301M-12
Ch. 3 In | J2 | Connector_Audio_QingPu:Jack_3.5mm_QingPu_WQP-PJ301M-12
Ch. 2 In | J3 | Connector_Audio_QingPu:Jack_3.5mm_QingPu_WQP-PJ301M-12
Ch. 4 In | J4 | Connector_Audio_QingPu:Jack_3.5mm_QingPu_WQP-PJ301M-12
Out | J5 | Connector_Audio_QingPu:Jack_3.5mm_QingPu_WQP-PJ301M-12
Power | J6 | Eurorack_Synth:Power_2x5_Vertical
3k3 | R1 R2 | Resistor_SMD:R_0603_1608Metric | C22978
27k | R11 | Resistor_SMD:R_0603_1608Metric | C22967
1k5 | R12 | Resistor_SMD:R_0603_1608Metric | C22843
1k | R14 | Resistor_SMD:R_0603_1608Metric | C21190
33k | R3 R4 R7 R8 | Resistor_SMD:R_0603_1608Metric | C4216
7k5 | R5 | Resistor_SMD:R_0603_1608Metric | C23234
10k | R6 R9 R10 R13 | Resistor_SMD:R_0603_1608Metric | C25804
Left | SW1 | Button_Switch_THT:SW_PUSH_6mm
Right | SW2 | Button_Switch_THT:SW_PUSH_6mm
Down | SW3 | Button_Switch_THT:SW_PUSH_6mm
Mode | SW4 | Switches_SMTS:SMTS-1xx-Solder
5k | T1 | Potentiometer_THT:Potentiometer_Bourns_3296W_Vertical
TL072CDT | U1 | Package_SO:SOIC-8_3.9x4.9mm_P1.27mm | C6961
SeeeduinoXIAOPin | U2 | Seeduino_Xiao:Seeeduino XIAO Pin
AMS1117-5.0 | U3 | Package_TO_SOT_SMD:SOT-223-3_TabPin2
