mzuelch/CATs-Eurosynth/Modules/HAGIWO/Multiout/Gerber/Rev. 012112/HAGIWO MultiOut Main - BOM.xls

Comment | Designator | Footprint | LCSC
10µ | C1 C2 C3 C4 | Capacitor_Tantalum_SMD:CP_EIA-3216-18_Kemet-A | C7171
100n | C11 C12 C13 | Capacitor_SMD:C_0402_1005Metric | C307331
10n | C5 C6 C7 C8 | Capacitor_SMD:C_0402_1005Metric | C15195
1µ | C9 C10 | Capacitor_SMD:C_0402_1005Metric | C52923
1N5819WS | D1 D2 | Diode_SMD:D_SOD-323 | C191023
BAT43W | D4 D5 D6 D7 D8 D9 D10 D11 D12 D13 | Diode_SMD:D_SOD-123 | C19167
Power | J1 | Eurorack_Synth:Power_2x5_Vertical
Ch. 1 | J10 | Connector_PinHeader_2.54mm:PinHeader_1x05_P2.54mm_Vertical
I2C | J11 | Connector_PinHeader_2.54mm:PinHeader_1x05_P2.54mm_Vertical
Ch. 2 | J12 | Connector_PinHeader_2.54mm:PinHeader_1x05_P2.54mm_Vertical
EncTrig | J9 | Connector_PinHeader_2.54mm:PinHeader_1x05_P2.54mm_Vertical
MMBT3904 | Q1 Q2 | Package_TO_SOT_SMD:SOT-23 | C20526
3k3 | R1 R2 | Resistor_SMD:R_0402_1005Metric | C25890
1k | R10 R11 | Resistor_SMD:R_0402_1005Metric | C11702
330R | R12 R13 R14 R15 | Resistor_SMD:R_0402_1005Metric | C25104
470R | R18 R19 | Resistor_SMD:R_0402_1005Metric | C25117
10k | R3 R16 R20 | Resistor_SMD:R_0402_1005Metric | C25744
6k8 | R4 R17 | Resistor_SMD:R_0402_1005Metric | C25917
220k | R5 R6 | Resistor_SMD:R_0402_1005Metric | C25767
33k | R9 | Resistor_SMD:R_0402_1005Metric | C25779
330k | R7 R8 | Resistor_SMD:R_0402_1005Metric | C25778
5k | RV1 RV2 | Potentiometer_THT:Potentiometer_Bourns_3266Y_Vertical
AMS1117-5.0 | U1 | Package_TO_SOT_SMD:SOT-223-3_TabPin2 | C6187
SeeeduinoXIAOPin | U2 | Seeduino_Xiao:Seeeduino XIAO Pin
MCP4725xxx-xCH | U3 U5 | Package_TO_SOT_SMD:SOT-23-6 | C144198
MCP6002-xSN | U4 | Package_SO:SOIC-8_3.9x4.9mm_P1.27mm | C7377
