mzuelch/CATs-Eurosynth/Modules/HAGIWO/Arduino VCO/Gerber/Rev. 012201/Arduino VCO Main BOM Rev. 012201.xls

Comment | Designator | Footprint | LCSC
Arduino_Nano_v3.x | A1 | Module:Arduino_Nano
10µ | C1 | Capacitor_Tantalum_SMD:CP_EIA-3216-18_Kemet-A | C7171
4.7µ | C10 | Capacitor_SMD:C_0603_1608Metric | C19666
10n | C2 C3 C4 C6 C8 | Capacitor_SMD:C_0402_1005Metric | C15195
68n | C5 C7 C9 | Capacitor_SMD:C_0603_1608Metric | C31658
B5819W SL | D1 | Diode_SMD:D_SOD-123 | C8598
BAT43 | D2 D3 D4 D5 D6 D7 D8 D9 | Diode_SMD:D_SOD-123 | C19167
Power | J1 | Eurorack_Synth:Power_2x5_Vertical
V/Oct | J2 | Connector_Audio_QingPu:Jack_3.5mm_QingPu_WQP-PJ301M-12
Inv | J3 | Connector_Audio_QingPu:Jack_3.5mm_QingPu_WQP-PJ301M-12
Out | J4 | Connector_Audio_QingPu:Jack_3.5mm_QingPu_WQP-PJ301M-12
Chord | J5 | Connector_Audio_QingPu:Jack_3.5mm_QingPu_WQP-PJ301M-12
B100K | P1 | Potentiometer_THT_Additional:Potentiometer_AlpsAlpine_RK09L1140
B100K | P2 P3 | Potentiometer_THT_Additional:Potentiometer_AlpsAlpine_RK09L1140_oS
1k | R1 R2 R3 R9 R12 | Resistor_SMD:R_0402_1005Metric | C11702
220 | R10 | Resistor_SMD:R_0402_1005Metric | C25091
100k | R4 R8 R11 | Resistor_SMD:R_0402_1005Metric | C25741
499k | R5 | Resistor_SMD:R_0603_1608Metric | C103678
3k9 | R6 R7 | Resistor_SMD:R_0402_1005Metric | C51721
MCP6001-OT | U1 | Package_TO_SOT_SMD:SOT-23-5 | C29429
