mzuelch/CATs-Eurosynth/Modules/HAGIWO/6Ch Trigger Sequencer/Gerber/Rev. 012110/HAGIWO 6Ch Gate Sequencer Main BOM Rev. 012110.xlsx

Comment | Designator | Footprint | LCSC
10µF/16V | C1 | Capacitor_Tantalum_SMD:CP_EIA-3216-18_Kemet-A | C7171
10n | C7 C8 | Capacitor_SMD:C_0603_1608Metric | C21122
B5817W | D1 | Diode_SMD:D_SOD-123 | C8598
BAV99W | D2 D3 D4 D5 D6 D7 D8 | Package_TO_SOT_SMD:SOT-323_SC-70 | C212725
470R | R1 R4 R5 R6 R8 R9 R10 | Resistor_SMD:R_0603_1608Metric | C23179
100k | R2 | Resistor_SMD:R_0603_1608Metric | C25803
3k3 | R3 R7 | Resistor_SMD:R_0603_1608Metric | C22978
