mzuelch/CATs-Eurosynth/Modules/YuSynth/Improved Steiner VCF/Electronics/Main/YuSynth Improved Steiner VCF Main BOM.xls

Comment | Designator | Footprint | LCSC
10uF | C1, C11, C12, C13, | Capacitor_SMD:C_0805_2012Metric | C15850
2.2uF | C2, C3, | Capacitor_SMD:C_0805_2012Metric | C49217
1.5n | C4, C6, C8, | Capacitor_SMD:C_0603_1608Metric | C1595
47µF | C5, C7, C10, | Capacitor_THT:CP_Radial_D5.0mm_P2.50mm
680n | C9, | Capacitor_THT:C_Disc_D4.7mm_W2.5mm_P5.00mm
100n | C14, C15, C16, C17, | Capacitor_SMD:C_0805_2012Metric | C49678
1N4148WS | D1, D2, D3, D4, D5, D6, D7, D8, D9, D10, | Diode_SMD:D_SOD-323 | C2128
B5819W | D11, D12, | Diode_SMD:D_SOD-123 | C8598
MountingHole_Pad | H1, | MountingHole:MountingHole_2.7mm_M2.5_DIN965_Pad
Power | J1, | Connector_PinHeader_2.54mm:PinHeader_2x05_P2.54mm_Vertical
Audio | J8, | Connector_PinHeader_2.54mm:PinHeader_1x04_P2.54mm_Vertical
SW | J9, | Connector_PinHeader_2.54mm:PinHeader_1x04_P2.54mm_Vertical
CO_CV | J10, | Connector_PinHeader_2.54mm:PinHeader_1x06_P2.54mm_Vertical
Res | J11, | Connector_PinHeader_2.54mm:PinHeader_1x06_P2.54mm_Vertical
BC847BDW1 | Q1, | Package_TO_SOT_SMD:SOT-363_SC-70-6 | C82368
10k | R1, R2, R24, | Resistor_SMD:R_0805_2012Metric | C17414
47k | R3, R6, R21, | Resistor_SMD:R_0805_2012Metric | C17713
220k | R4, R5, R8, R25, R27, | Resistor_SMD:R_0805_2012Metric | C17556
150k | R7, | Resistor_SMD:R_0805_2012Metric | C17470
180k | R9, R10, | Resistor_SMD:R_0805_2012Metric | C17501
1.8k | R11, R18, | Resistor_SMD:R_0805_2012Metric | C17398
220R | R12, | Resistor_SMD:R_0805_2012Metric | C17557
390 | R13, | Resistor_SMD:R_0805_2012Metric | C17655
1k | R14, R15, R23, R28, | Resistor_SMD:R_0805_2012Metric | C17513
3.9k | R16, R22, | Resistor_SMD:R_0805_2012Metric | C17614
82R | R17, | Resistor_SMD:R_0805_2012Metric | C17841
2.2M | R19, | Resistor_SMD:R_0805_2012Metric | C26113
22k | R20, | Resistor_SMD:R_0805_2012Metric | C17560
1M | R26, | Resistor_SMD:R_0805_2012Metric | C17514
2k | RV1, | Potentiometer_THT:Potentiometer_Bourns_3006P_Horizontal
1k | RV2, | Potentiometer_THT:Potentiometer_Bourns_3006P_Horizontal
TL072 | U1, U2, | Package_SO:SO-8_3.9x4.9mm_P1.27mm | C6961
