mzuelch/CATs-Eurosynth/Modules/MFOS/Eight Stage Phase Shifter/Gerber/Rev. 022212/MFOS Eight Stage Phase Shifter - Main/MFOS Eight Stage Phase Shifter - Main - BOM.xls

Comment | Designator | Footprint | LCSC
100n | C1,C2,C3,C4,C5,C6,C8,C9,C10,C11,C12,C13,C14,C15 | Capacitor_SMD:C_0402_1005Metric | C1525
220n | C17 | Capacitor_SMD:C_0402_1005Metric | C16772
1ÂµF/25V | C18 | Capacitor_SMD:CP_Elec_4x5.4 | C90265
100p | C19 | Capacitor_SMD:C_0402_1005Metric | C1546
10ÂµF/25V | C20 | Capacitor_SMD:CP_Elec_5x5.4 | C116402
4.7nF | C21,C22,C23,C24,C25,C26,C27,C28 | Capacitor_SMD:C_0402_1005Metric | C1538
1ÂµF/25V | C29 | Capacitor_SMD:C_0402_1005Metric | C52923
22pF | C30,C31 | Capacitor_SMD:C_0402_1005Metric | C1555
10ÂµF/16V | C7,C16 | Capacitor_Tantalum_SMD:CP_EIA-3216-18_Kemet-A | C7171
1N4148WS | D1 | Diode_SMD:D_SOD-323 | C2128
1N5817 | D2,D3 | Diode_SMD:D_SOD-323 | C122854
LFO | J1 | Connector_PinHeader_2.54mm:PinHeader_1x06_P2.54mm_Vertical
CV_OUT | J2 | Connector_PinHeader_2.54mm:PinHeader_1x06_P2.54mm_Vertical
In | J3 | Connector_PinHeader_2.54mm:PinHeader_1x06_P2.54mm_Vertical
Power | J6 | CATs_Eurosynth_Specials:Power_2x5_Vertical
MMBT3904 | Q1,Q3 | Package_TO_SOT_SMD:SOT-23 | C20526
MMBT3906 | Q2 | Package_TO_SOT_SMD:SOT-23 | C111114
430k | R11 | Resistor_SMD:R_0402_1005Metric | C25786
1M | R13 | Resistor_SMD:R_0402_1005Metric | C26083
100k | R12,R17,R20 | Resistor_SMD:R_0402_1005Metric | C25741
2k | R22 | Resistor_SMD:R_0402_1005Metric | C4109
30k | R23,R25,R27,R29,R32,R35,R38,R42,R43,R45,R47,R49,R56,R57,R59,R62 | Resistor_SMD:R_0402_1005Metric | C25776
20k | R24,R26,R28,R30,R44,R46,R48,R50,R64 | Resistor_SMD:R_0402_1005Metric | C25765
43k | R3 | Resistor_SMD:R_0402_1005Metric | C25561
1k | R8,R31,R34,R37,R40,R51,R52,R53,R54 | Resistor_SMD:R_0402_1005Metric | C11702
10k | R2,R5,R9,R14,R19,R33,R36,R39,R41,R55,R58,R60,R61 | Resistor_SMD:R_0402_1005Metric | C25744
33k | R65 | Resistor_SMD:R_0402_1005Metric | C25779
270k | R7 | Resistor_SMD:R_0402_1005Metric | C25770
TL072 | U1,U2,U3 | Package_SO:SOIC-8_3.9x4.9mm_P1.27mm | C6961
LM13700 | U4,U5,U6,U7 | Package_SO:SOIC-16_3.9x9.9mm_P1.27mm | C174050
