mzuelch/CATs-Eurosynth/Modules/Slim Line/Sample&Hold SMD/Mechanics/Sample&Hold Module Front.DXF

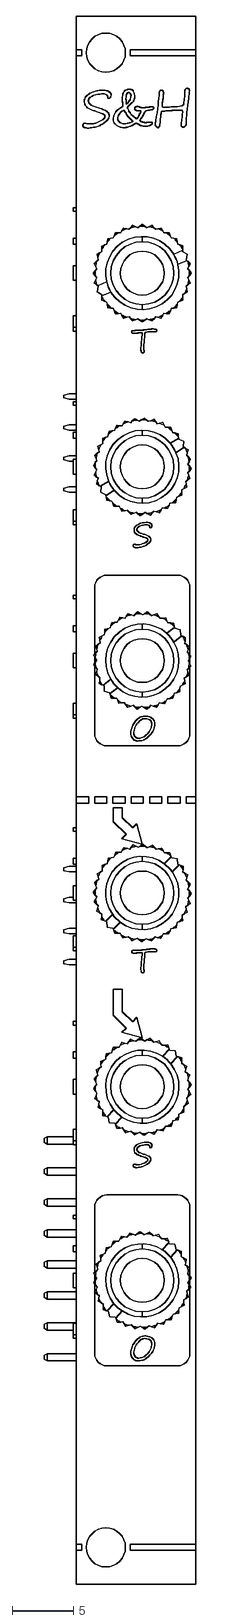
[picture p72: CAD file, 2024-11-01]
Modules/Slim Line/Sample&Hold SMD/Mechanics/Sample&Hold Module Front.DXF
12.5 x 128.5
