mzuelch/CATs-Eurosynth/Modules/Slim Line/Single Attenuator/Mechanics/Single Attenuator Isometric.DXF

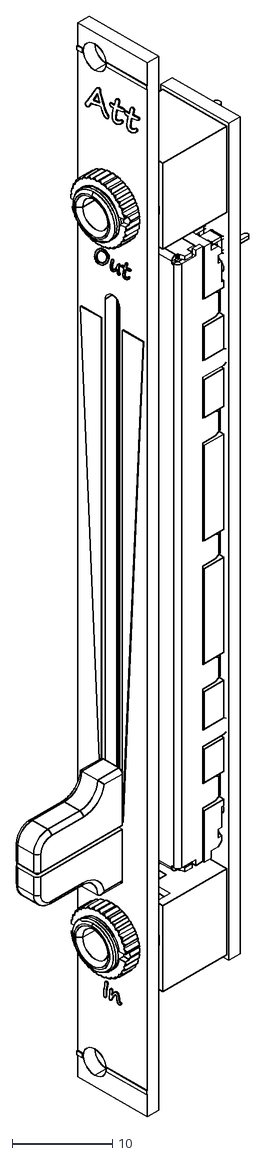
[picture p73: CAD file, 2024-11-01]
Modules/Slim Line/Single Attenuator/Mechanics/Single Attenuator Isometric.DXF
23.1 x 109.6
