mzuelch/CATs-Eurosynth/Modules/Slim Line/Voltage Controlled Switch/Mechanics/Slimline Voltage Controlled Switch Module Front.DXF

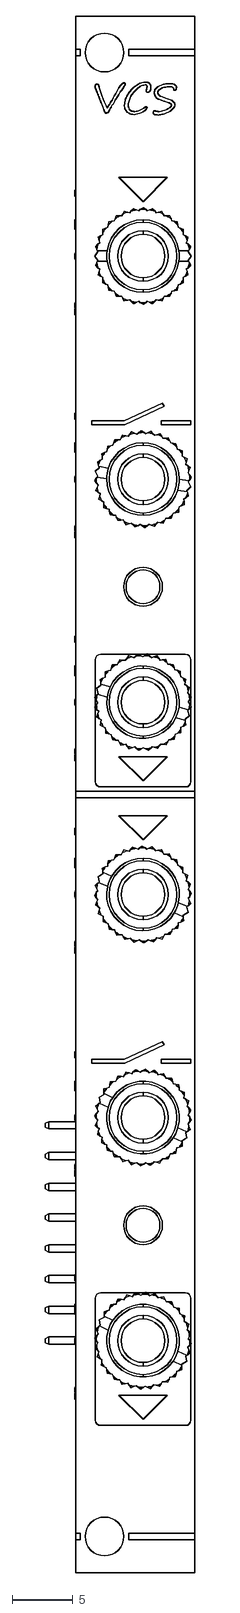
[picture p74: CAD file, 2024-11-01]
Modules/Slim Line/Voltage Controlled Switch/Mechanics/Slimline Voltage Controlled Switch Module Front.DXF
12.3 x 128.5
