mzuelch/CATs-Eurosynth/Modules/Standard Line/Classic ADSR/Mechanics/Classic ADSR Front.DXF

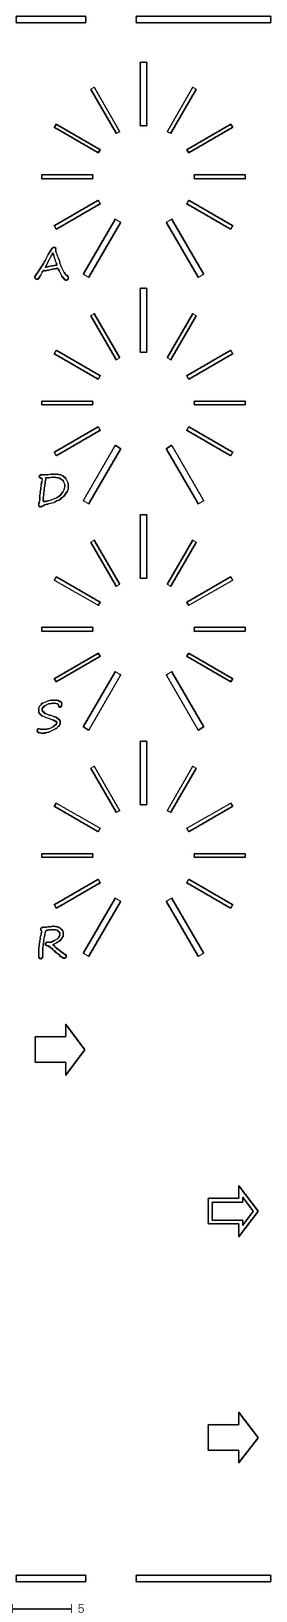
[picture p75: CAD file, 2022-06-12]
Modules/Standard Line/Classic ADSR/Mechanics/Classic ADSR Front.DXF
21.3 x 131.2
