mzuelch/CATs-Eurosynth/Modules/Standard Line/Envelope Follower/Mechanics/Envelope Follower Front.STEP

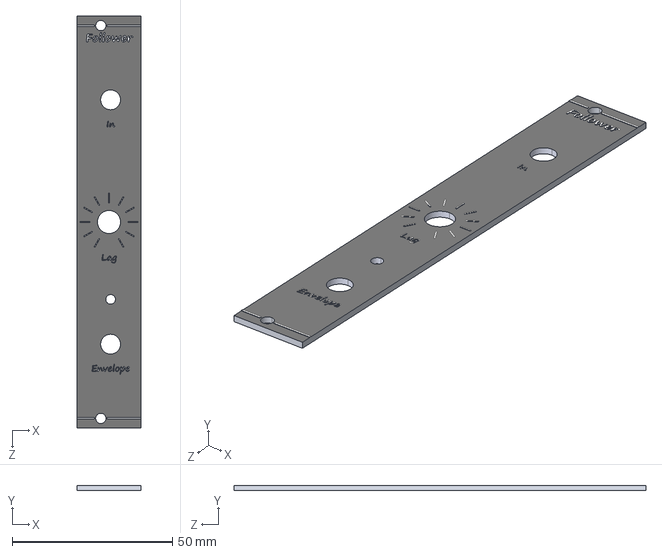
[picture p76: CAD file, 2022-02-18]
Modules/Standard Line/Envelope Follower/Mechanics/Envelope Follower Front.STEP
20.0 x 1.70 x 128.5 mm
