mzuelch/CATs-Eurosynth/Modules/Standard Line/Manual Gate/Mechanics/Manual Gate Front.STEP

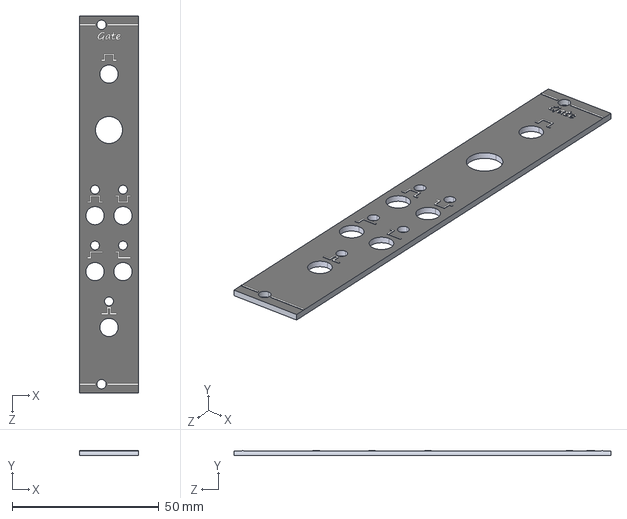
[picture p77: CAD file, 2022-02-02]
Modules/Standard Line/Manual Gate/Mechanics/Manual Gate Front.STEP
20.0 x 1.70 x 128.5 mm
