mzuelch/CATs-Eurosynth/Modules/Standard Line/Power Module/Mechanics/Power Module Front.step

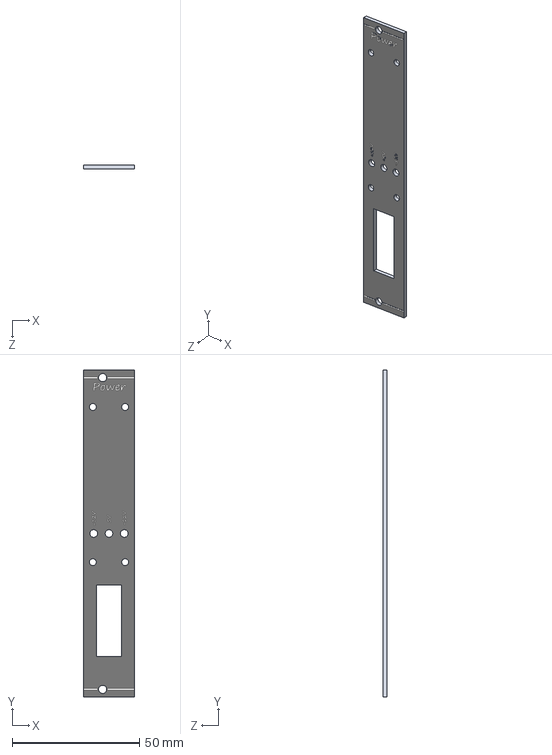
[picture p78: CAD file, 2022-06-16]
Modules/Standard Line/Power Module/Mechanics/Power Module Front.step
20.0 x 128.5 x 1.70 mm
