mzuelch/CATs-Eurosynth/Modules/Standard Line/Vactrol VCF/Mechanics/Vactrol VCF Front.DXF

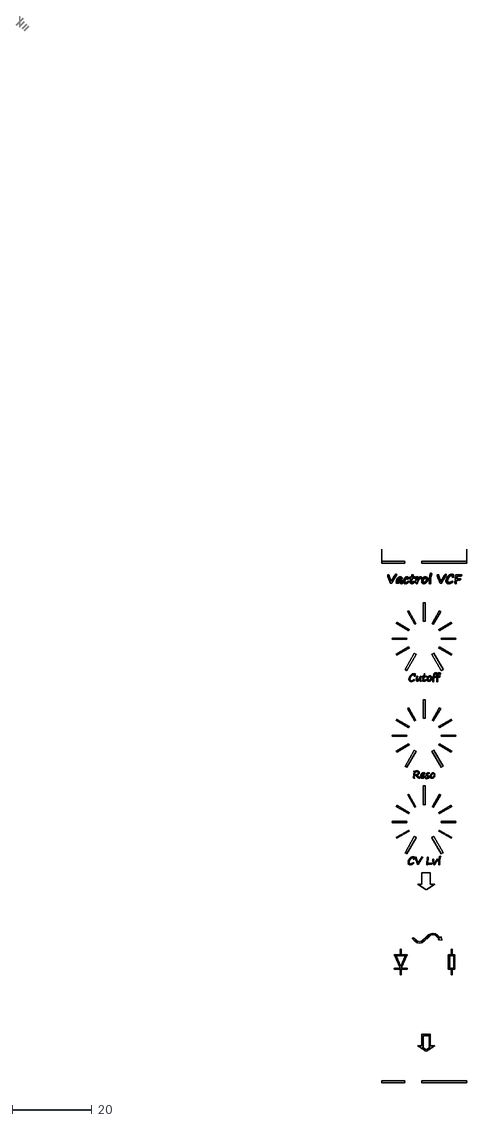
[picture p79: CAD file, 2022-05-24]
Modules/Standard Line/Vactrol VCF/Mechanics/Vactrol VCF Front.DXF
113.2 x 268.2
