mzuelch/CATs-Eurosynth/Modules/HAGIWO/Arduino VCO/Mechanics/HAGIWO Arduino VCO Additive Front.DXF

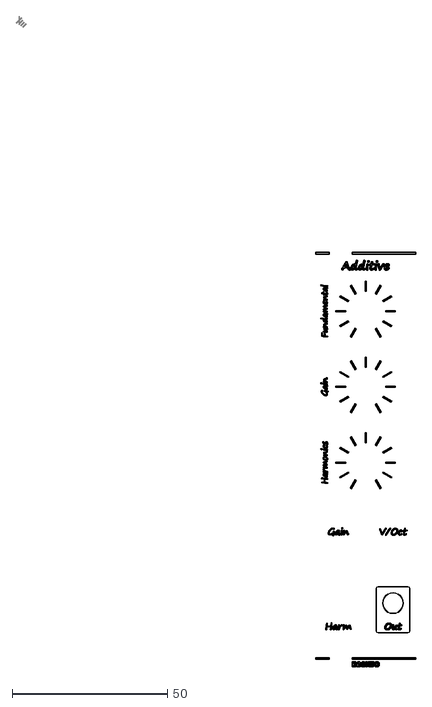
[picture p80: CAD file, 2022-02-19]
Modules/HAGIWO/Arduino VCO/Mechanics/HAGIWO Arduino VCO Additive Front.DXF
128.6 x 209.7
