mzuelch/CATs-Eurosynth/Modules/MFOS/Eight Stage Phase Shifter/Mechanics/Davies 1900H (violet).stp

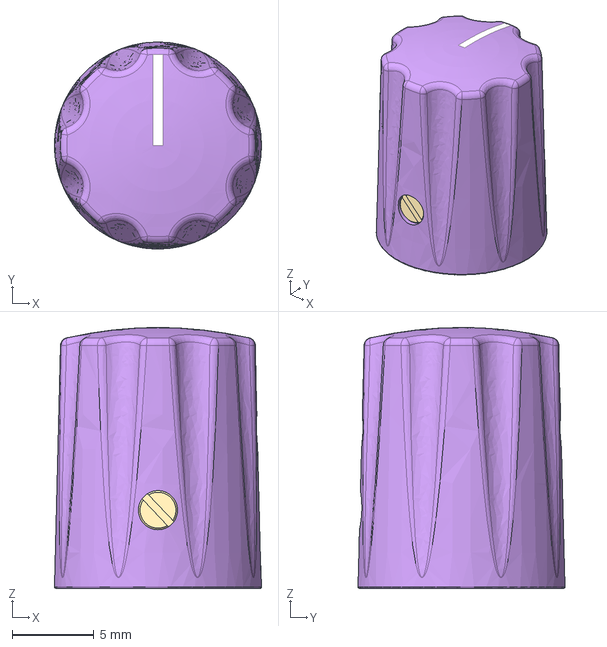
[picture p81: CAD file, 2022-09-18]
Modules/MFOS/Eight Stage Phase Shifter/Mechanics/Davies 1900H (violet).stp
12.7 x 12.7 x 16.0 mm
