mzuelch/CATs-Eurosynth/Modules/Slim Line/Buffered Multiple SMD/Mechanics/Buffered Multiple Front.DXF

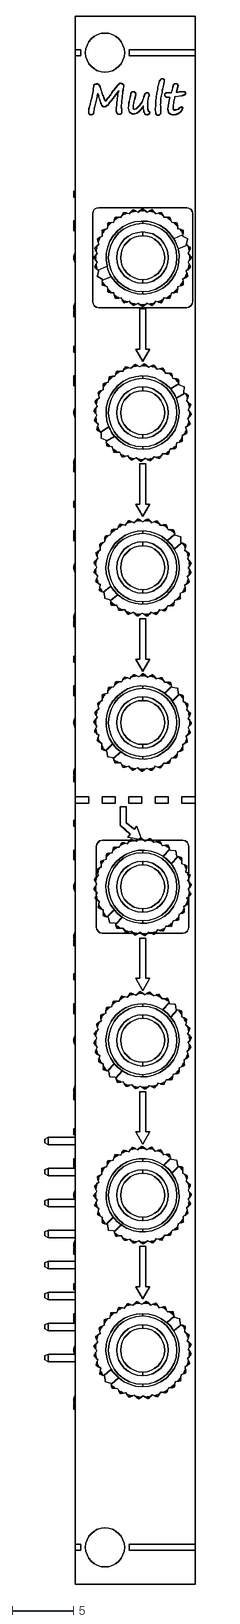
[picture p82: CAD file, 2022-11-05]
Modules/Slim Line/Buffered Multiple SMD/Mechanics/Buffered Multiple Front.DXF
12.3 x 128.5
