mzuelch/CATs-Eurosynth/Modules/Slim Line/Precision Adder/Mechanics/Slimline Precision Adder Module.STEP

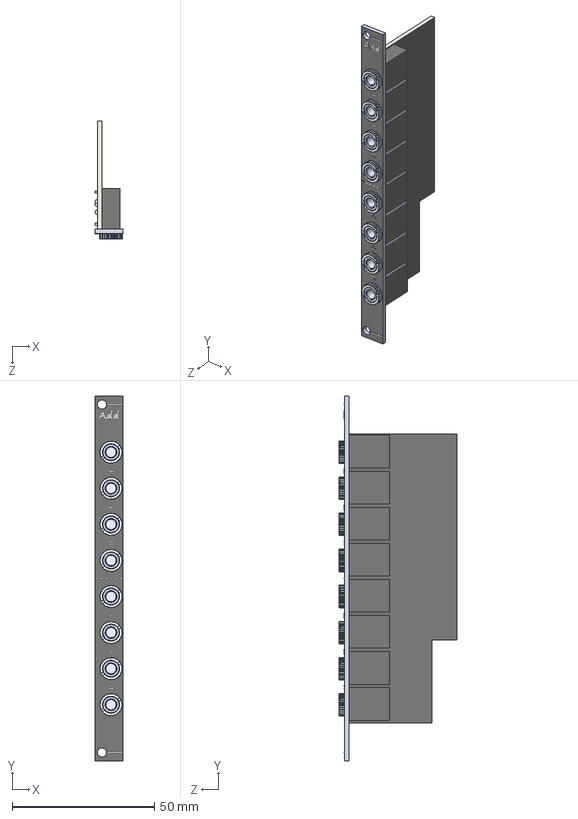
[picture p83: CAD file, 2022-02-10]
Modules/Slim Line/Precision Adder/Mechanics/Slimline Precision Adder Module.STEP
9.85 x 128.5 x 41.7 mm
Slimline Precision Adder Front
Platine^Slimline Precision Adder Module
PJ-324M.step x 8
Nut.step x 8
