mzuelch/CATs-Eurosynth/Modules/Slim Line/Rectifier SMD/Mechanics/Slimline Rectifier Module.STEP

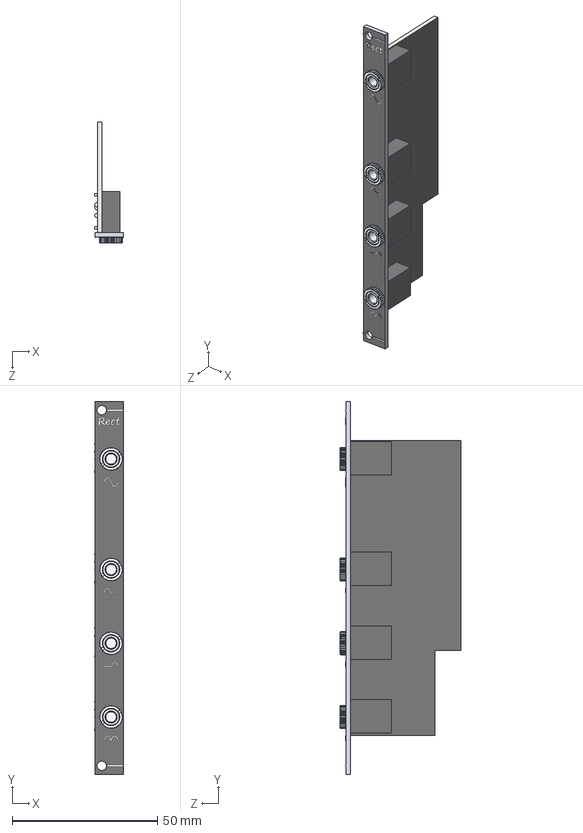
[picture p84: CAD file, 2022-02-19]
Modules/Slim Line/Rectifier SMD/Mechanics/Slimline Rectifier Module.STEP
9.85 x 128.5 x 41.7 mm
Slimline Rectifier Front
Platine^Slimline Rectifier Module
PJ-324M.step x 4
Nut.step x 4
