mzuelch/CATs-Eurosynth/Modules/Slim Line/Sample&Hold SMD/Mechanics/Sample&Hold Module.DXF

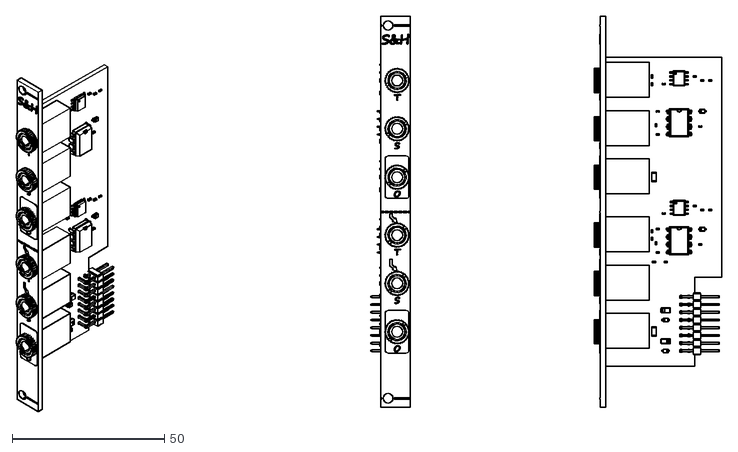
[picture p85: CAD file, 2023-07-17]
Modules/Slim Line/Sample&Hold SMD/Mechanics/Sample&Hold Module.DXF
231.7 x 129.9
