mzuelch/CATs-Eurosynth/Modules/Slim Line/Single Attenuator/Mechanics/Single Attenuator.DXF

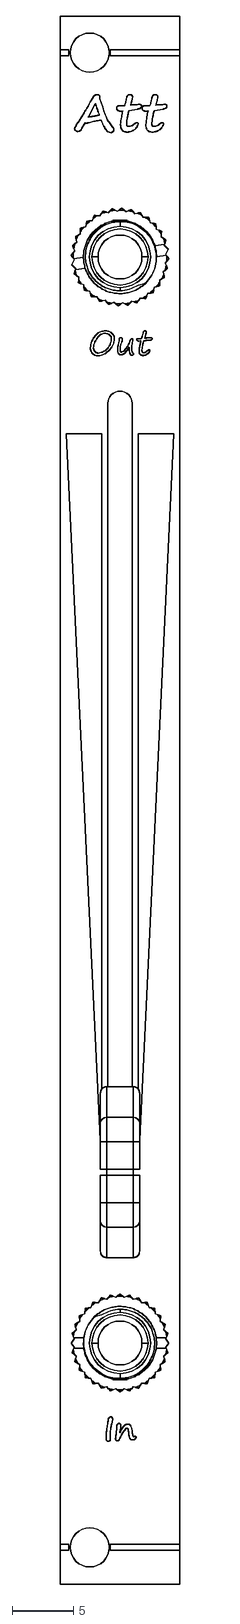
[picture p86: CAD file, 2024-11-01]
Modules/Slim Line/Single Attenuator/Mechanics/Single Attenuator.DXF
9.80 x 128.5
