mzuelch/CATs-Eurosynth/Modules/Slim Line/VCA/Mechanics/Slimline VCA Modul.STEP

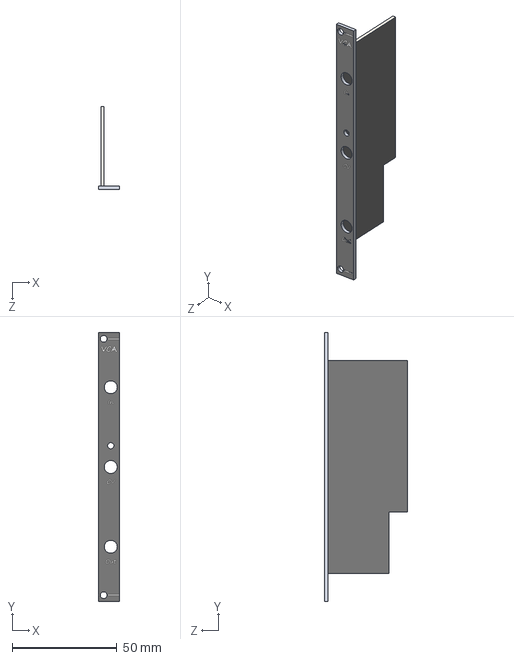
[picture p87: CAD file, 2022-05-15]
Modules/Slim Line/VCA/Mechanics/Slimline VCA Modul.STEP
9.80 x 128.5 x 39.8 mm
Slimline VCA Front
Teil2^Slimline VCA Modul
