mzuelch/CATs-Eurosynth/Modules/Slim Line/Voltage Controlled Switch/Mechanics/Timing Diagram.DXF

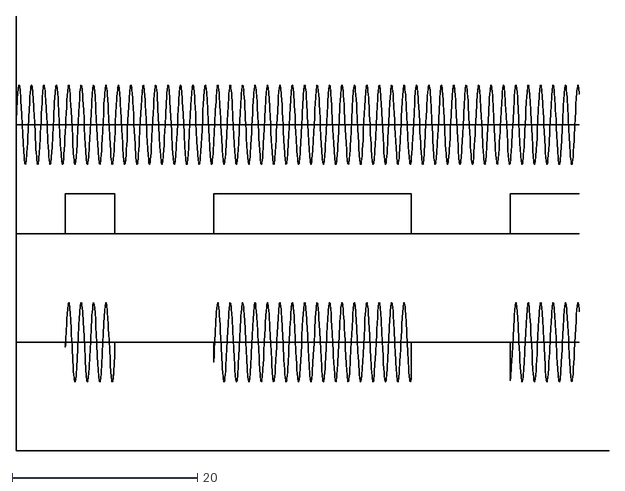
[picture p88: CAD file, 2023-03-15]
Modules/Slim Line/Voltage Controlled Switch/Mechanics/Timing Diagram.DXF
64.0 x 46.9
