mzuelch/CATs-Eurosynth/Modules/Standard Line/Power Module/Mechanics/Power Modul Module.STEP

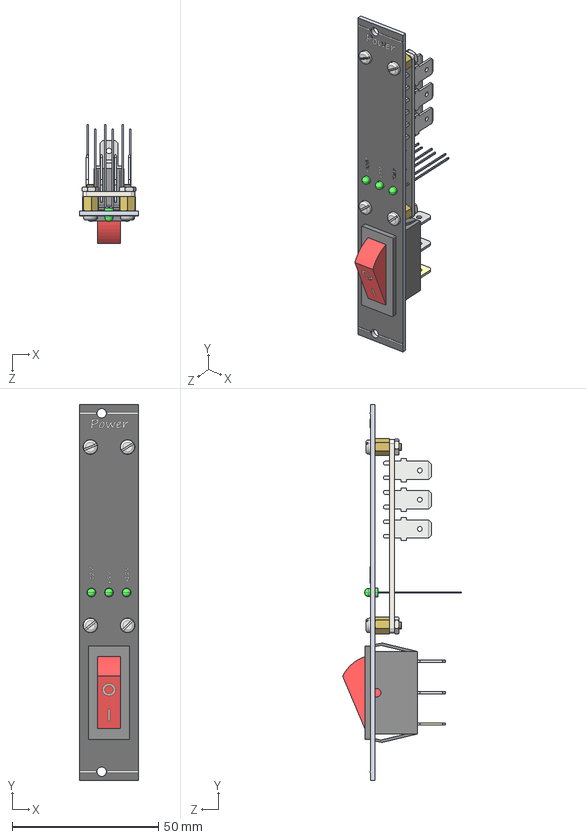
[picture p89: CAD file, 2022-06-16]
Modules/Standard Line/Power Module/Mechanics/Power Modul Module.STEP
20.0 x 128.5 x 40.6 mm
Power Module Front
slotted pan head screw_din_DIN EN ISO 1580 - M2.5 x 6 - 6C x 4
M2.5_5_male_female x 4
Power Module Main
hex thin nut chamfered gradeab_din_Hexagon Thin Nut ISO 4035 - M2.5 - C x 4
LED 3mm_Gr］ x 3
c-725964-2-d-3d x 12
Single Pole Rocker Switch
