mzuelch/CATs-Eurosynth/Modules/HAGIWO/Arduino VCO/Mechanics/HAGIWO Arduino VCO 2Op FM Front.DXF

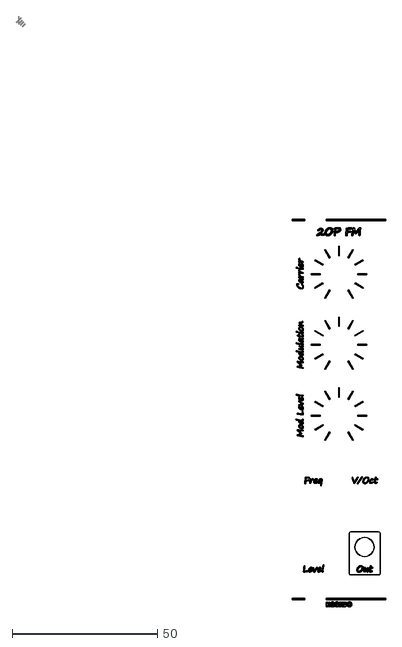
[picture p90: CAD file, 2022-02-19]
Modules/HAGIWO/Arduino VCO/Mechanics/HAGIWO Arduino VCO 2Op FM Front.DXF
127.2 x 203.4
