mzuelch/CATs-Eurosynth/Modules/MFOS/Eight Stage Phase Shifter/Mechanics/MFOS Phaser Front.DXF

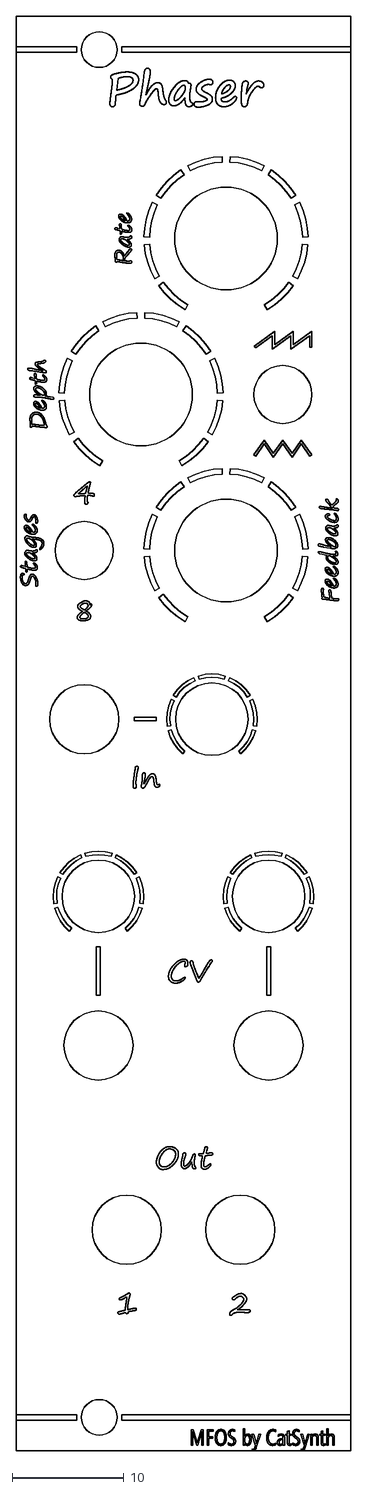
[picture p91: CAD file, 2022-09-18]
Modules/MFOS/Eight Stage Phase Shifter/Mechanics/MFOS Phaser Front.DXF
30.0 x 128.5
