mzuelch/CATs-Eurosynth/Modules/Slim Line/Buffered Multiple SMD/Mechanics/Buffered Multiple.STEP

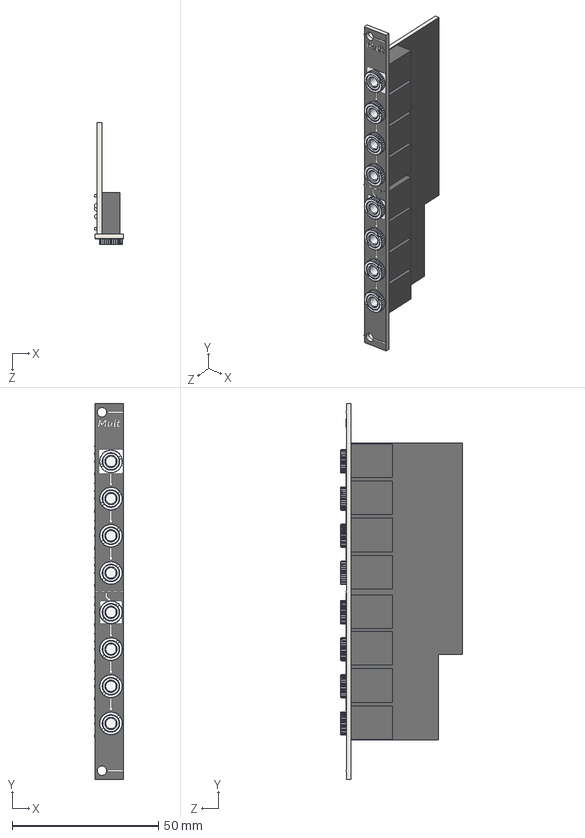
[picture p92: CAD file, 2021-09-05]
Modules/Slim Line/Buffered Multiple SMD/Mechanics/Buffered Multiple.STEP
9.95 x 128.5 x 41.8 mm
Buffered Multiple Frontplatte
Buffered Multiple Platine
PJ-324M x 8
Nut x 8
