mzuelch/CATs-Eurosynth/Modules/Slim Line/Clock Divider/Mechanics/Slimline Clock Divider V2 Module.STEP

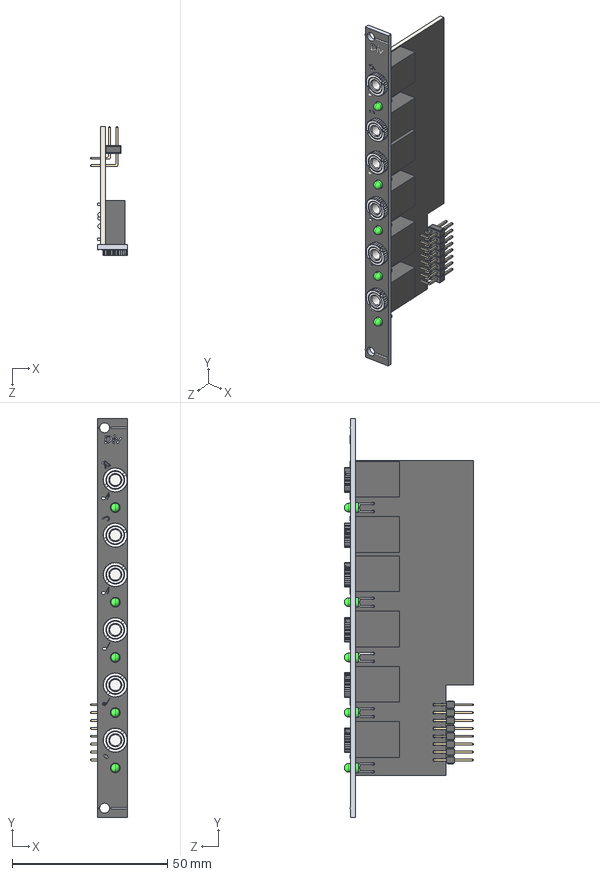
[picture p93: CAD file, 2023-03-05]
Modules/Slim Line/Clock Divider/Mechanics/Slimline Clock Divider V2 Module.STEP
12.1 x 128.5 x 41.7 mm
Slimline Clock Divider V2 Front
Nut x 6
LED 3mm gebogen 2HP Standard x 5
SOLID^PJ-324M_Slimline Clock Divider SMD Main_Slimline Clock Divider V2 Module x 6
Slimline Clock Divider SMD Main PCB^Slimline Clock Divider SMD Main_Slimline Clock Divider V2 Module
Header 2P - Right Angle - Jameco x 8
