mzuelch/CATs-Eurosynth/Modules/Slim Line/Sample&Hold SMD/Mechanics/Sample&Hold.STEP

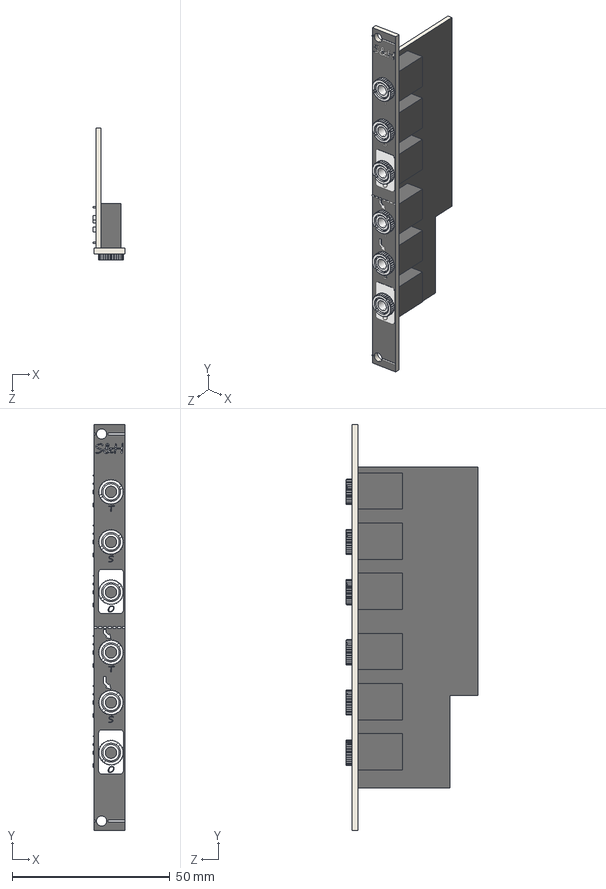
[picture p94: CAD file, 2021-06-18]
Modules/Slim Line/Sample&Hold SMD/Mechanics/Sample&Hold.STEP
10.1 x 128.5 x 41.9 mm
Sample&Hold Frontplatte
Teil2^Sample&Hold
PJ324M x 6
ID_1_2 x 6
