mzuelch/CATs-Eurosynth/Modules/Slim Line/Single Attenuator/Mechanics/Knob Fader.STL

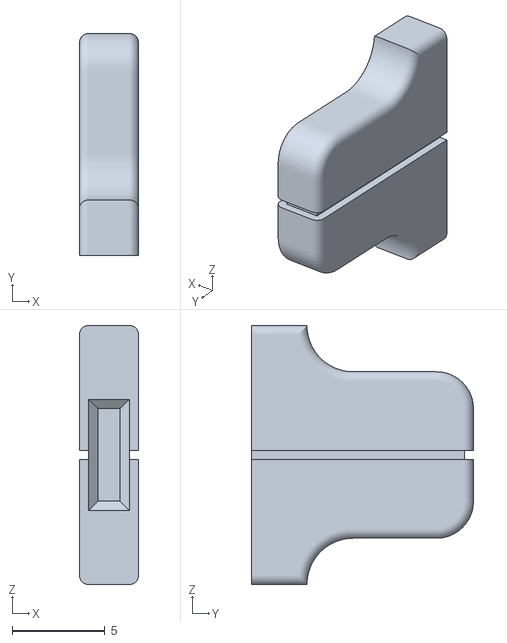
[picture p95: CAD file, 2021-03-16]
Modules/Slim Line/Single Attenuator/Mechanics/Knob Fader.STL
3.20 x 12.0 x 14.0
