mzuelch/CATs-Eurosynth/Modules/Slim Line/Voltage Controlled Switch/Mechanics/Slimline Voltage Controlled Switch Module.DXF

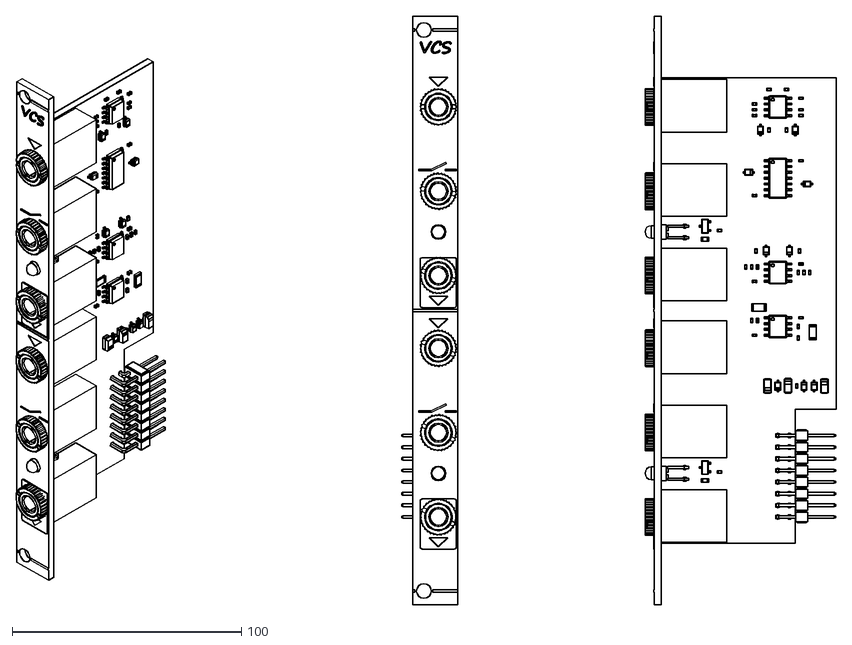
[picture p96: CAD file, 2023-03-15]
Modules/Slim Line/Voltage Controlled Switch/Mechanics/Slimline Voltage Controlled Switch Module.DXF
358.1 x 257.0
