mzuelch/CATs-Eurosynth/Modules/Slim Line/Voltage Controlled Switch/Mechanics/Slimline Voltage Controlled Switch Front.DXF

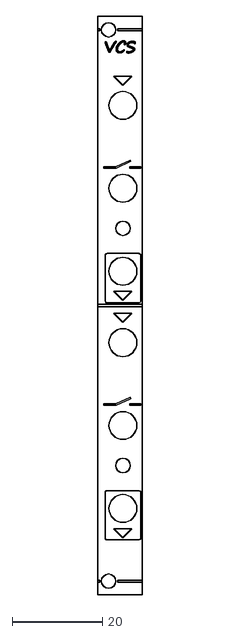
[picture p97: CAD file, 2023-03-15]
Modules/Slim Line/Voltage Controlled Switch/Mechanics/Slimline Voltage Controlled Switch Front.DXF
9.80 x 128.5
