mzuelch/CATs-Eurosynth/Modules/Slim Line/Voltage Controlled Switch/Documentation/Etketten Bogen.pdf

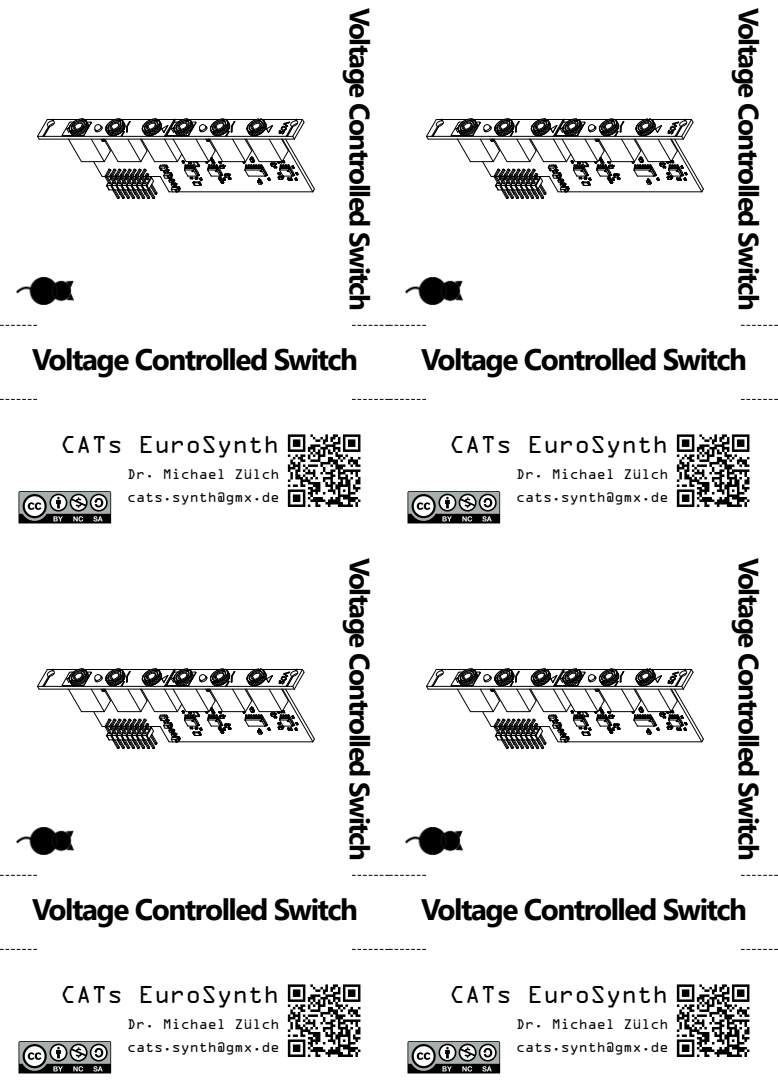
[picture p100: page 1]
CATs EuroSynth

Voltage Controlled Switch

Dr. Michael Zülch
cats.synth@gmx.de
