mzuelch/CATs-Eurosynth/Modules/Slim Line/Clock Divider/Documentation/Etketten Bogen.pdf

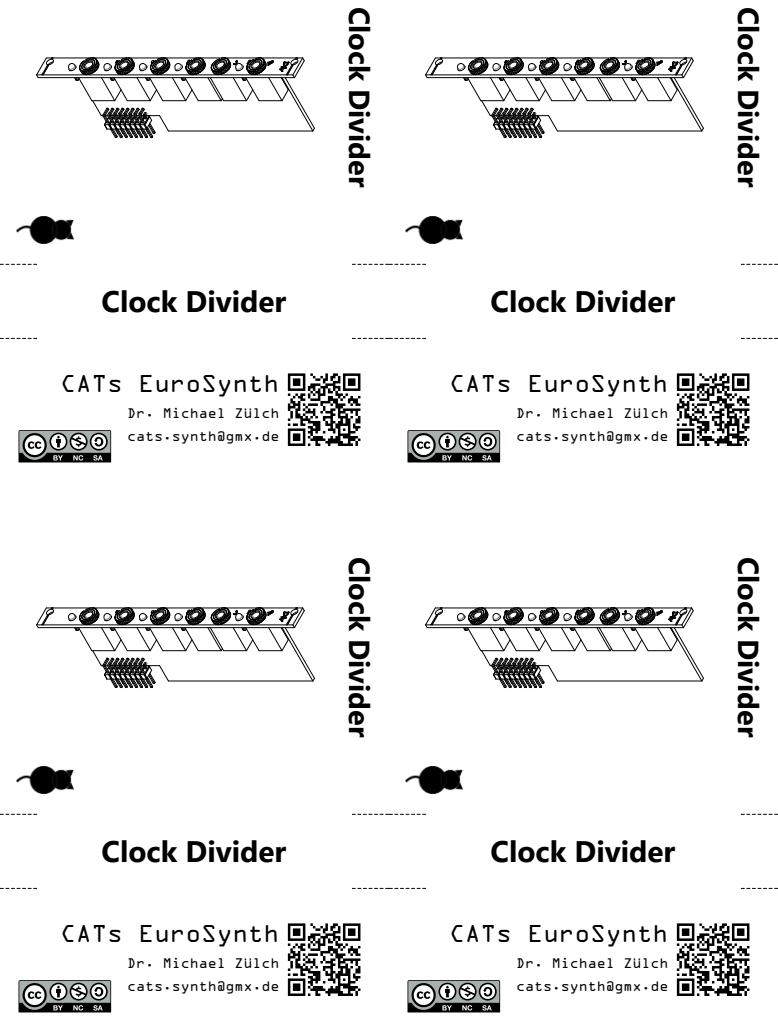
[picture p109: page 1]
Clock Divider; CATs EuroSynth

Dr. Michael Zülch
cats.synth@gmx.de
