mzuelch/CATs-Eurosynth/Modules/Standard Line/Envelope Follower/Simulation/Envelope Follower.asc

C1: cap; 100n
C2: cap; 100n
D1: diode; 1N4148
D2: diode; 1N4148
D3: diode; 1N4148
D4: diode; 1N4148
D5: LED; NSCW100
P1: res; 1Meg
R1: res; 100k
R2: res; 100k
R3: res; 100k
R4: res; 100k
R5: res; 100k
R6: res; 560
R7: res; 100k
R13: res; 2k
R14: res; 39k
R15: res; 10k
R16: res; 18k
R17: res; 10k
R18: res; 1k
U1: OP07
U2: OP07
U3: OP07
U4: OP07
V1: voltage; 12
V2: voltage; 12
V3: voltage; SINE(0 5 1000 100m 5)
Named nets: Vee, Vcc, 0, Audio, Out
.tran 2
