mzuelch/CATs-Eurosynth/Modules/HAGIWO/VCF Diode Ladder Filter/Simulation/VCF Diode Ladder Filter.asc

C1: cap; 10µ
C2: cap; 47n
C3: cap; 47n
C4: cap; 47n
C5: cap; 47n
C6: cap; 4.7µ
C7: cap; 4.7µ
C8: cap; 10µ
C9: cap; 10µ
D1: diode; 1N4148
D2: diode; 1N4148
D3: diode; 1N4148
D4: diode; 1N4148
D5: diode; 1N4148
D6: diode; 1N4148
D7: diode; 1N4148
D8: diode; 1N4148
D9: diode; 1N4148
D10: diode; 1N4148
D11: diode; 1N4148
D12: diode; 1N4148
Q1: npn; BC847C
Q2: npn; BC847C
Q3: npn; BC847C
Q4: npn; BC847C
R1: res; 10k
R2: res; 33k
R3: res; 1k
R4: res; 6.8k
R5: res; 6.8k
R6: res; 100k
R7: res; 100k
R8: res; 1k
R9: res; 33k
R10: res; 2.2k
R11: res; 2.2k
R12: res; 10k
R13: res; 10k
R14: res; 4.7k
R15: res; 4.7k
R16: res; 2.2k
R17: res; 33k
R18: res; 10k
R19: res; 10k
R20: res; 33k
R21: res; 33k
R22: res; 2.2k
R23: res; 10k
U1: 
U2: 
V1: voltage; 12
V2: voltage; 12
V3: voltage; PULSE(-5 5 1p 9m 1p 1p 9m)
V4: voltage; PULSE(0 5 1p 2 2 1p 4)
X1: pot; R=100K Val=100
X2: pot; R=50K Val=50
X3: pot; R=100K Val=0
Named nets: 0, +V, -V, Signal, CV, Out
.tran 5
.wave "Filter.wav" 16 44.1k V(Out)
