mzuelch/CATs-Eurosynth/Modules/HAGIWO/Arduino VCO/Simulation/Arduino VCO Output Stage.asc

A1: diffschmtbuf; ref=0 vlow=0 vhigh={vout} td=10p trise=1p tfall=1p
C1: cap; 22n
C2: cap; 3.3n
R1: res; 3.9k
R2: res; 2.7k
R3: res; 7.5k
R4: res; 1k
R5: res; 100k
R6: res; 100k
R7: res; 100k
U1: 
U2: 
V1: voltage; 12
V2: voltage; 12
V3: voltage; SINE(0.5 0.5 1k)
V4: voltage; PULSE(0 1 0 {0.5/freq} {0.5/freq} 1p {1/freq})
V5: voltage; 5
Named nets: -V, +V, 0, Filter_In, Out, Filter_Out
.param freq=32k vout=5
.tran 100m
