mzuelch/CATs-Eurosynth/Modules/Slim Line/Rectifier SMD/Simulation/Rectifier.asc

D1: diode; 1N4148
D2: diode; 1N4148
D3: diode; 1N4148
D4: diode; 1N4148
R1: res; 100k
R2: res; 100k
R3: res; 100k
R4: res; 100k
R5: res; 1k
R6: res; 100k
R7: res; 1k
R8: res; 100k
R9: res; 100k
R10: res; 100k
R11: res; 100k
R12: res; 100k
R13: res; 100k
R14: res; 1k
U1: OP07
U2: OP07
U3: OP07
U4: OP07
U5: OP07
V1: voltage; 12
V2: voltage; 12
V3: voltage; SINE(0 5 1000 10m)
Named nets: Vee, Vcc, 0, Audio, PHW, NHW, FW
.tran 100m
