mzuelch/CATs-Eurosynth/Modules/Standard Line/Abakus/Simulation/Min_Max.asc

D1: diode; 1N4148
D2: diode; 1N4148
D3: diode; 1N4148
D4: diode; 1N4148
D5: diode; 1N4148
D6: diode; 1N4148
R1: res; 10k
R2: res; 10k
R3: res; 300k
R4: res; 300k
R5: res; 300k
R6: res; 100k
R7: res; 100k
R8: res; 100k
R9: res; 100k
R10: res; 90k
R11: res; 10k
R12: res; 100k
R13: res; 100k
R14: res; 100k
R15: res; 1k
R16: res; 1k
U1: 
U2: 
U3: 
U4: 
U5: 
U6: 
U7: 
U8: 
U9: 
U10: 
V1: voltage; 12
V2: voltage; 12
V3: voltage; PULSE(-3 3 1n 100m 100m 1n 200m)
V4: voltage; PULSE(-4 4 1n 200m 200m 1n 400m)
V5: voltage; PULSE(-5 5 1n 400m 400m 1n 800m)
Named nets: +V, 0, -V, Sig1, Sig2, Sig3, Out_Max, Out_Min, Out_Inv, Out_Sum, Att1
.tran 2
