mzuelch/CATs-Eurosynth/Modules/MFOS/Dual VCA #2/Electronics/Main/Dual VCA #2 Main.kicad_pcb

## KiCad design Modules/MFOS/Dual VCA #2/Electronics/Main/Dual VCA #2 Main.kicad_pcb (2022-09-25)

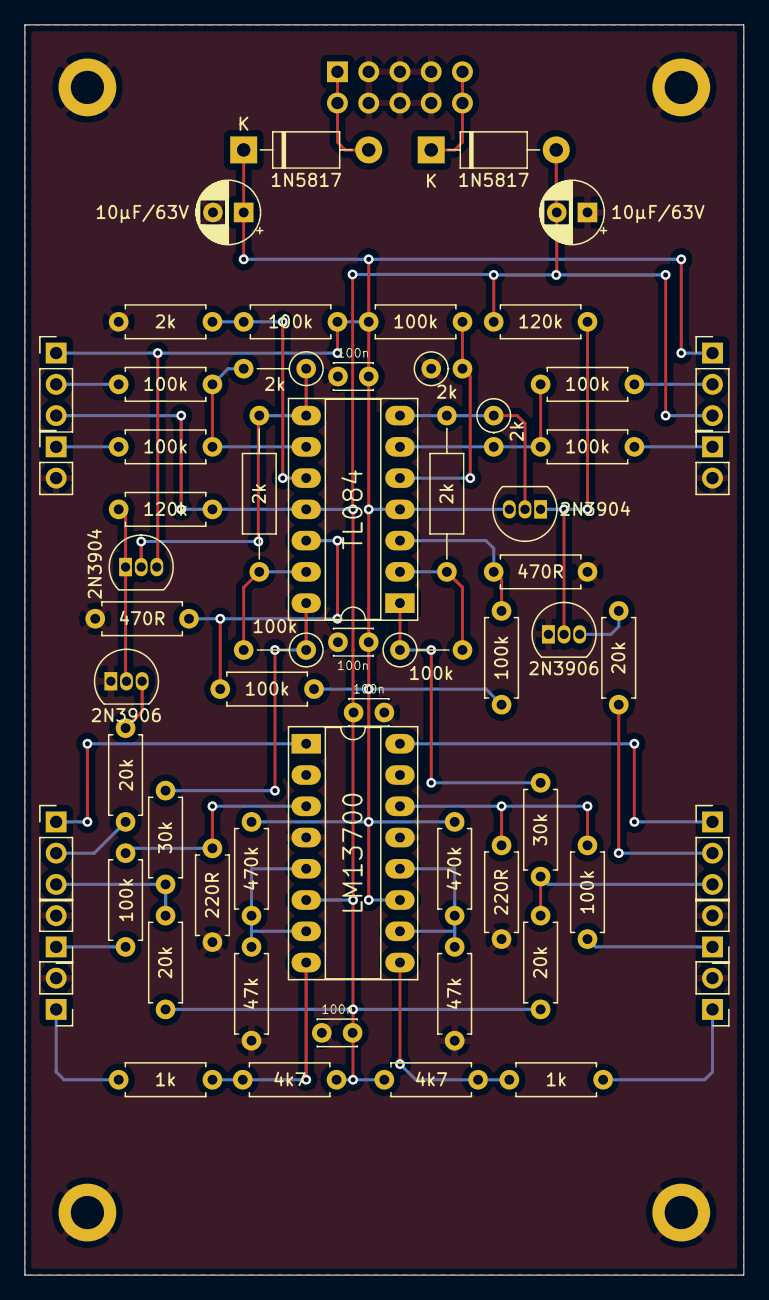
[picture p125: board Dual VCA #2 Main.kicad_pcb from above]

Board: 2 copper layers, 58.4 x 101.6 mm, 67 parts (1 on the bottom side), 41 nets.

Parts:
C1, C2: 10µF/63V; CP_Radial_D5.0mm_P2.50mm
C3, C4, C5, C6: 100n; C_Disc_D3.0mm_W2.0mm_P2.50mm
D1, D2: 1N5817; D_DO-41_SOD81_P10.16mm_Horizontal
H1, H2, H3, H4: MH; MountingHole_2.7mm_M2.5_DIN965_Pad
IC1: TL084; DIP-14_W7.62mm_Socket_LongPads
IC2: LM13700; DIP-16_W7.62mm_Socket_LongPads
J1: Pot #1; PinHeader_1x03_P2.54mm_Vertical
J2: CV In #1; PinHeader_1x02_P2.54mm_Vertical
J3: Sig In #1; PinHeader_1x02_P2.54mm_Vertical
J4: SW #1; PinHeader_1x03_P2.54mm_Vertical
J5: Sig Out #1; PinHeader_1x02_P2.54mm_Vertical
J6: Pot #2; PinHeader_1x03_P2.54mm_Vertical
J7: Power; Power_2x5_Vertical
J8: CV In #2; PinHeader_1x02_P2.54mm_Vertical
J9: Sig In #2; PinHeader_1x02_P2.54mm_Vertical
J10: SW #2; PinHeader_1x03_P2.54mm_Vertical
J11: Sig Out #2; PinHeader_1x02_P2.54mm_Vertical
Q1, Q3: 2N3904; TO-92_Inline
Q2, Q4: 2N3906; TO-92_Inline
R2, R6, R7, R10, R17, R22, R26, R27, R30, R37: 100k; R_Axial_DIN0207_L6.3mm_D2.5mm_P7.62mm_Horizontal
R3: 2k; R_Axial_DIN0207_L6.3mm_D2.5mm_P5.08mm_Vertical
R4, R24: 2k; R_Axial_DIN0207_L6.3mm_D2.5mm_P12.70mm_Horizontal
R5, R25: 100k; R_Axial_DIN0207_L6.3mm_D2.5mm_P5.08mm_Vertical
R8: 2k; R_Axial_DIN0207_L6.3mm_D2.5mm_P7.62mm_Horizontal
R9, R29: 120k; R_Axial_DIN0207_L6.3mm_D2.5mm_P7.62mm_Horizontal
R11, R31: 470R; R_Axial_DIN0207_L6.3mm_D2.5mm_P7.62mm_Horizontal
R12, R13, R32, R33: 20k; R_Axial_DIN0207_L6.3mm_D2.5mm_P7.62mm_Horizontal
R14, R34: 30k; R_Axial_DIN0207_L6.3mm_D2.5mm_P7.62mm_Horizontal
R15, R35: 470k; R_Axial_DIN0207_L6.3mm_D2.5mm_P7.62mm_Horizontal
R16, R36: 47k; R_Axial_DIN0207_L6.3mm_D2.5mm_P7.62mm_Horizontal
R18, R38: 220R; R_Axial_DIN0207_L6.3mm_D2.5mm_P7.62mm_Horizontal
R19, R39: 4k7; R_Axial_DIN0207_L6.3mm_D2.5mm_P7.62mm_Horizontal
R20, R40: 1k; R_Axial_DIN0207_L6.3mm_D2.5mm_P7.62mm_Horizontal
R23, R28: 2k; R_Axial_DIN0207_L6.3mm_D2.5mm_P2.54mm_Vertical

Connections:
+12V: C1.1, C3.1, C4.1, D1.1, IC1.4, IC2.11, J1.1, J6.1, Q1.3, Q3.3, R7.2, R10.2, R15.2, R27.2, R30.2, R35.2
+12VA: D1.2, J7.+12V
-12V: C2.2, C5.2, C6.2, D2.2, IC1.11, IC2.6, J1.3, J6.3, R9.1, R13.1, R19.1, R29.1, R33.1, R39.1
-12VA: D2.1, J7.-12V
GND: C1.2, C2.1, C3.2, C4.2, C5.1, C6.1, H1.1, H2.1, H3.1, H4.1, IC2.4, IC2.13, J2.2, J3.2, J5.2, J7.GND, J8.2, J9.2, J11.2, Q2.1, Q4.1, R8.1, R11.1, R16.2, R18.1, R28.1, R31.1, R36.2, R38.1
unnamed: IC1.1, R25.1, R34.2
unnamed: IC1.2, R24.1, R25.2
unnamed: IC1.3, R30.1, R31.2
unnamed: IC1.5, R27.1, R28.2
unnamed: IC1.6, R22.1, R23.2, R26.1
unnamed: IC1.7, Q3.2, R23.1, R24.2
unnamed: IC1.8, Q1.2, R3.1, R4.2
unnamed: IC1.9, R2.1, R3.2, R6.1
unnamed: IC1.10, R7.1, R8.2
unnamed: IC1.12, R10.1, R11.2
unnamed: IC1.13, R4.1, R5.2
unnamed: IC1.14, R5.1, R14.2
unnamed: IC2.1, J4.1
unnamed: IC2.3, R17.1, R18.2
unnamed: IC2.5, IC2.7, R15.1, R16.1
unnamed: IC2.8, R19.2, R20.2
unnamed: IC2.9, R39.2, R40.2
unnamed: IC2.10, IC2.12, R35.1, R36.1
unnamed: IC2.14, R37.1, R38.2
unnamed: IC2.16, J10.1
unnamed: J1.2, R2.2
unnamed: J2.1, R6.2
unnamed: J3.1, R17.2
unnamed: J4.2, R12.1
unnamed: J4.3, R13.2, R14.1
unnamed: J5.1, R20.1
unnamed: J6.2, R22.2
unnamed: J8.1, R26.2
unnamed: J9.1, R37.2
unnamed: J10.2, R32.1
unnamed: J10.3, R33.2, R34.1
unnamed: J11.1, R40.1
unnamed: Q1.1, Q2.2, R9.2
unnamed: Q2.3, R12.2
unnamed: Q3.1, Q4.2, R29.2
unnamed: Q4.3, R32.2
