mzuelch/CATs-Eurosynth/Modules/MFOS/Noise Cornucopia/Electronics/Main 1/MFOS Noise Cornucopia Main 1.kicad_pcb

## KiCad design Modules/MFOS/Noise Cornucopia/Electronics/Main 1/MFOS Noise Cornucopia Main 1.kicad_pcb (2022-09-25)

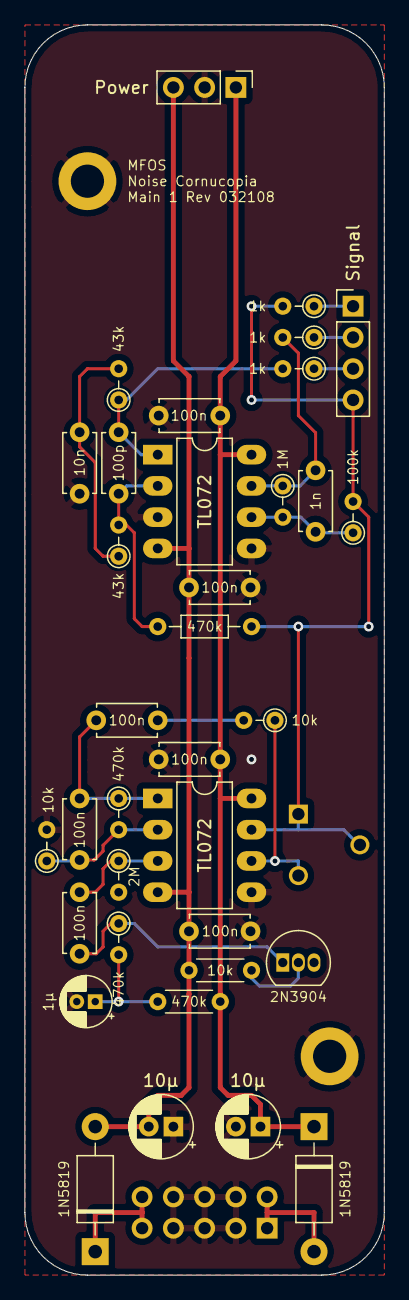
[picture p126: board MFOS Noise Cornucopia Main 1.kicad_pcb from above]

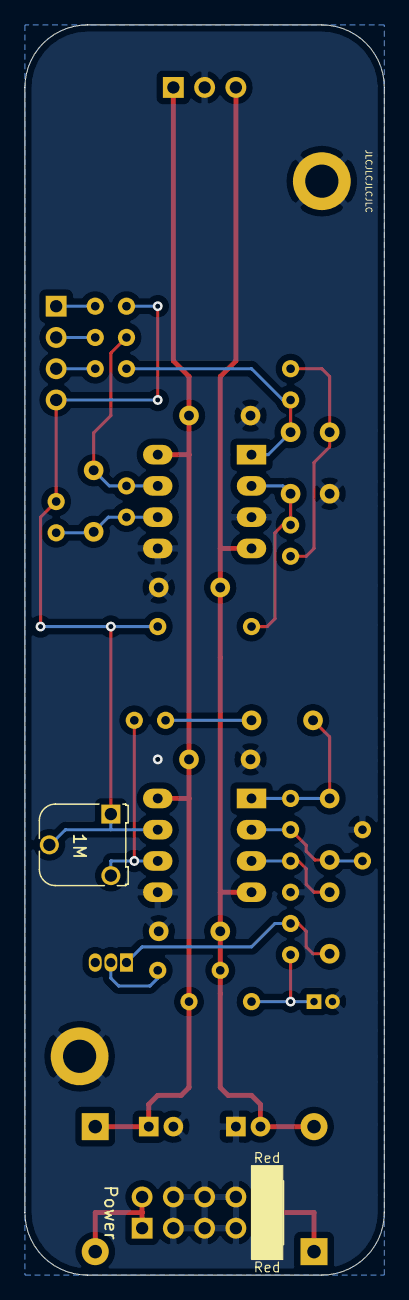
[picture p127: board MFOS Noise Cornucopia Main 1.kicad_pcb from below]

Board: 2 copper layers, 29.2 x 101.6 mm, 39 parts (2 on the bottom side), 22 nets.

Parts:
C1, C2, C4, C5, C7, C10, C12: 100n; C_Disc_D4.7mm_W2.5mm_P5.00mm
C3: 1n; C_Disc_D4.7mm_W2.5mm_P5.00mm
C6, C11: 10µ; CP_Radial_D5.0mm_P2.00mm
C9: 100p; C_Disc_D4.7mm_W2.5mm_P5.00mm
C14: 10n; C_Disc_D4.7mm_W2.5mm_P5.00mm
C18: 1µ; CP_Radial_D4.0mm_P1.50mm
D4, D5: 1N5819; D_DO-41_SOD81_P10.16mm_Horizontal
H1, H2: MountingHole_Pad; MountingHole_2.7mm_M2.5_DIN965_Pad
J1: Signal; PinHeader_1x04_P2.54mm_Vertical
J2: Power; PinHeader_1x03_P2.54mm_Vertical
J4: Power; Power_2x5_Vertical
Q1: 2N3904; TO-92_Inline
R1, R3, R11: 1k; R_Axial_DIN0204_L3.6mm_D1.6mm_P2.54mm_Vertical
R2, R10: 470k; R_Axial_DIN0204_L3.6mm_D1.6mm_P2.54mm_Vertical
R4: 2M; R_Axial_DIN0204_L3.6mm_D1.6mm_P2.54mm_Vertical
R5, R9: 10k; R_Axial_DIN0204_L3.6mm_D1.6mm_P2.54mm_Vertical
R6: 100k; R_Axial_DIN0204_L3.6mm_D1.6mm_P2.54mm_Vertical
R7: 1M; R_Axial_DIN0204_L3.6mm_D1.6mm_P2.54mm_Vertical
R8: 1M; Potentiometer_Runtron_RM-065_Vertical
R12: 470k; R_Axial_DIN0204_L3.6mm_D1.6mm_P7.62mm_Horizontal
R16, R17: 43k; R_Axial_DIN0204_L3.6mm_D1.6mm_P2.54mm_Vertical
R33: 470k; R_Axial_DIN0204_L3.6mm_D1.6mm_P5.08mm_Horizontal
R34: 10k; R_Axial_DIN0204_L3.6mm_D1.6mm_P5.08mm_Horizontal
U1, U2: TL072; DIP-8_W7.62mm_LongPads

Connections:
+12V: C5.2, C6.1, C7.2, D4.1, J2.1, R33.1, U1.8, U2.8
+12VA: D4.2, J4.+12V
-12V: C10.1, C11.2, C12.1, D5.2, J2.3, R34.2, U1.4, U2.4
-12VA: D5.1, J4.-12V
GND: C5.1, C6.2, C7.1, C10.2, C11.1, C12.2, C14.1, C18.2, H1.1, H2.1, J2.2, J4.GND, R4.2, R9.2, U1.5, U2.3, U2.5
HPNS: J1.3, R11.1
LPNS: J1.2, R3.1
NOISE_INT: J1.4, R1.2, R6.2, R8.1, R8.2, R12.2, U1.7
unnamed: C1.1, R4.1, U1.3
unnamed: C1.2, Q1.1, R2.1
unnamed: C2.1, R5.2
unnamed: C2.2, C4.1, R10.1, U1.1
unnamed: C3.1, R3.2, R7.1, U2.7
unnamed: C3.2, R6.1, R7.2, U2.6
unnamed: C4.2, R9.1, R10.2, U1.2
unnamed: C9.1, R12.1, R16.2, U2.2
unnamed: C9.2, R11.2, R17.1, U2.1
unnamed: C14.2, R16.1, R17.2
unnamed: C18.1, R2.2, R33.2
unnamed: Q1.2, R34.1
unnamed: R5.1, R8.3, U1.6
WNS: J1.1, R1.1
