mzuelch/CATs-Eurosynth/Modules/Slim Line/Single Attenuator/Electronics/Main/Single Attenuator.kicad_pcb

## KiCad design Modules/Slim Line/Single Attenuator/Electronics/Main/Single Attenuator.kicad_pcb (2022-09-25)

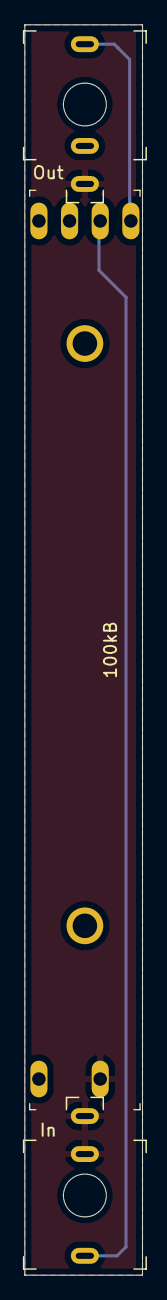
[picture p128: board Single Attenuator.kicad_pcb from above]

Board: 2 copper layers, 9.6 x 102.0 mm, 3 parts (0 on the bottom side), 3 nets.

Parts:
J1: In; PJ-301-M-12
J2: Out; PJ-301-M-12
RV1: 100kB; Potentiometer_Fader_Alps_RS__01_Dual

Connections:
GND: J1.S, J1.TN, J2.S, RV1.3
unnamed: J1.T, RV1.1
unnamed: J2.T, RV1.2
