mzuelch/CATs-Eurosynth/Modules/HAGIWO/Multiout/Electronics/Control/HAGIWO MultiOut Control.kicad_pcb

## KiCad design Modules/HAGIWO/Multiout/Electronics/Control/HAGIWO MultiOut Control.kicad_pcb (2022-09-25)

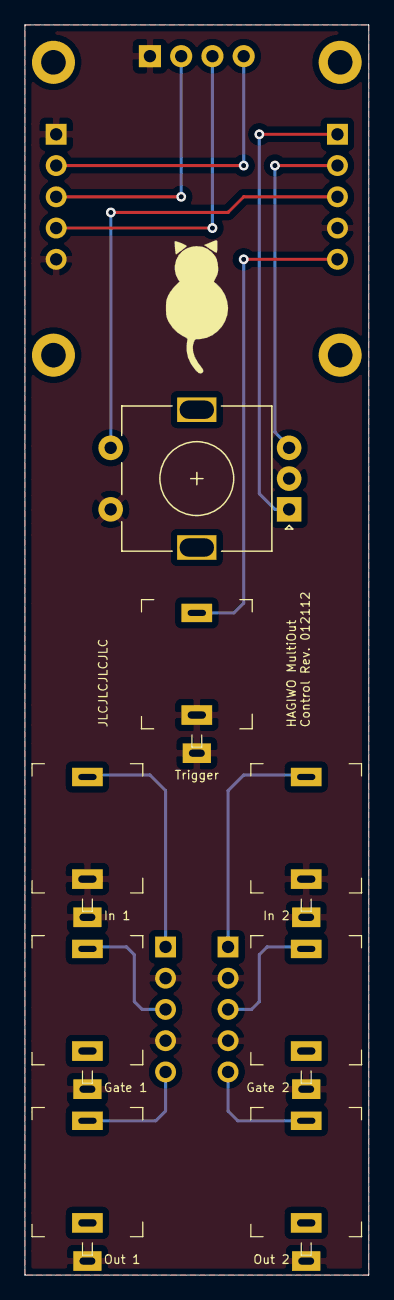
[picture p129: board HAGIWO MultiOut Control.kicad_pcb from above]

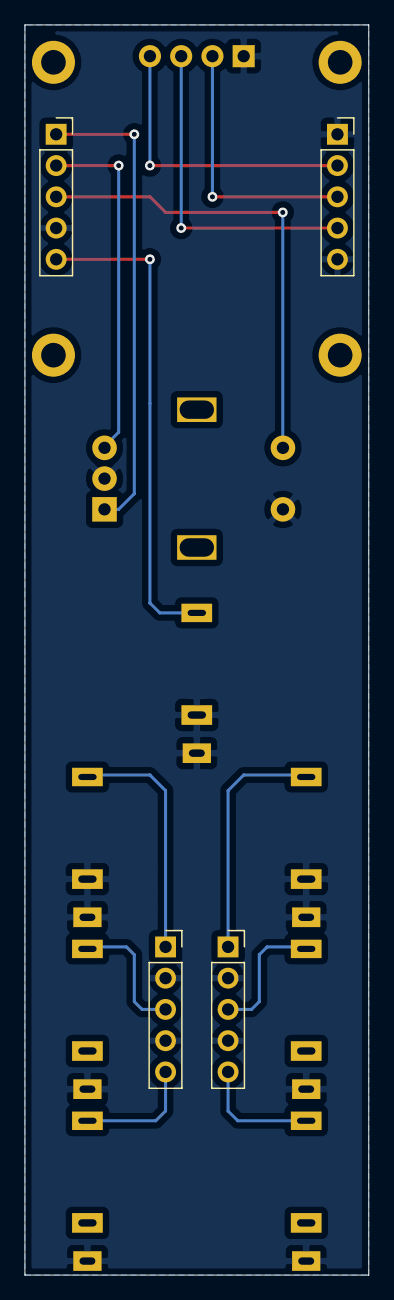
[picture p130: board HAGIWO MultiOut Control.kicad_pcb from below]

Board: 2 copper layers, 27.9 x 101.6 mm, 13 parts (4 on the bottom side), 14 nets.

Parts:
D1: SSD1306_4Pin; 0.96inch_OLED_MC096GX
J1: Trigger; Jack_3.5mm_QingPu_WQP-PJ301M-12
J2: In 1; Jack_3.5mm_QingPu_WQP-PJ301M-12
J3: Gate 1; Jack_3.5mm_QingPu_WQP-PJ301M-12
J4: Out 1; Jack_3.5mm_QingPu_WQP-PJ301M-12
J5: In 2; Jack_3.5mm_QingPu_WQP-PJ301M-12
J6: Gate 2; Jack_3.5mm_QingPu_WQP-PJ301M-12
J7: Out 2; Jack_3.5mm_QingPu_WQP-PJ301M-12
J8: EncTrig; PinSocket_1x05_P2.54mm_Vertical
J9: Ch. 1; PinSocket_1x05_P2.54mm_Vertical
J10: Ch. 2; PinSocket_1x05_P2.54mm_Vertical
J11: I2C; PinSocket_1x05_P2.54mm_Vertical
SW1: Enc; RotaryEncoder_Alps_EC11E-Switch_Vertical_H20mm

Connections:
+3V3: D1.VCC, J11.3
Enc_A: J8.1, SW1.A
Enc_B: J8.2, SW1.B
Enc_SW: J8.3, SW1.S1
GND: D1.GND, J1.S, J1.TN, J2.S, J2.TN, J3.S, J4.S, J5.S, J5.TN, J6.S, J7.S, J8.4, J9.2, J9.4, J10.2, J10.4, J11.1, J11.5, SW1.C, SW1.S2
Gate1: J3.T, J9.3
Gate2: J6.T, J10.3
In1: J2.T, J9.1
In2: J5.T, J10.1
Out1: J4.T, J9.5
Out2: J7.T, J10.5
SCL: D1.SCL, J11.4
SDA: D1.SDA, J11.2
Trigger: J1.T, J8.5
