mzuelch/CATs-Eurosynth/Modules/HAGIWO/Multiout/Electronics/Main/HAGIWO MultiOut Main.kicad_pcb

## KiCad design Modules/HAGIWO/Multiout/Electronics/Main/HAGIWO MultiOut Main.kicad_pcb (2022-09-25)

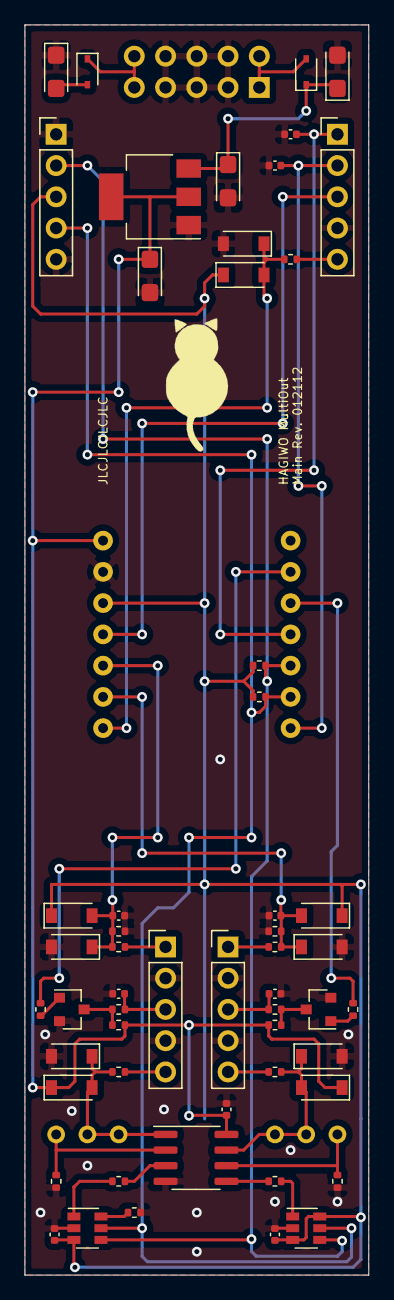
[picture p131: board HAGIWO MultiOut Main.kicad_pcb from above]

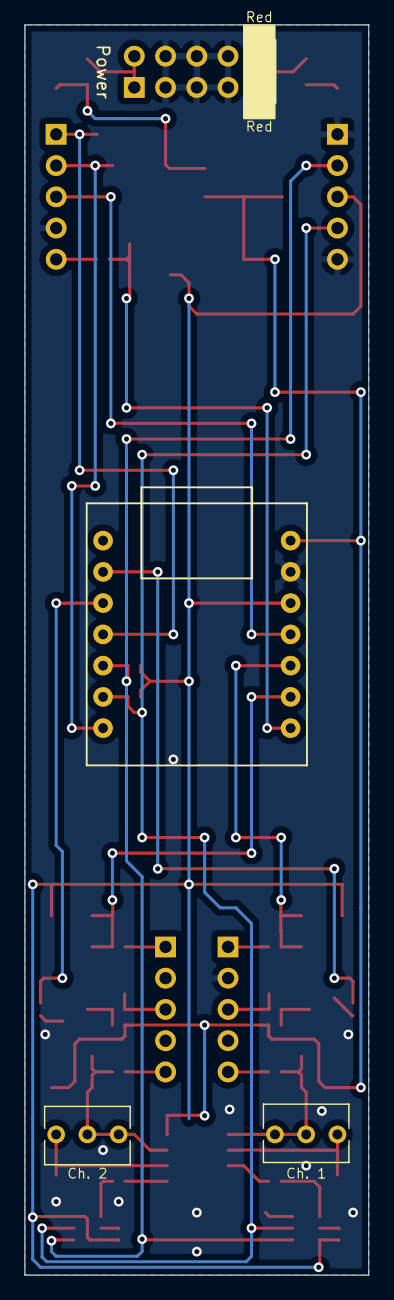
[picture p132: board HAGIWO MultiOut Main.kicad_pcb from below]

Board: 2 copper layers, 27.9 x 101.6 mm, 59 parts (4 on the bottom side), 37 nets.

Parts:
C1, C2, C3, C4: 10µ; CP_EIA-3216-18_Kemet-A
C5, C6, C7, C8: 10n; C_0402_1005Metric
C9, C10: 1µ; C_0402_1005Metric
C11, C12, C13: 100n; C_0402_1005Metric
D1, D2: 1N5819WS; D_SOD-323
D4, D5, D6, D7, D8, D9, D10, D11, D12, D13: BAT43W; D_SOD-123
J1: Power; Power_2x5_Vertical
J9: EncTrig; PinHeader_1x05_P2.54mm_Vertical
J10: Ch. 1; PinHeader_1x05_P2.54mm_Vertical
J11: I2C; PinHeader_1x05_P2.54mm_Vertical
J12: Ch. 2; PinHeader_1x05_P2.54mm_Vertical
Q1, Q2: MMBT3904; SOT-23
R1, R2: 3k3; R_0402_1005Metric
R3, R16, R20: 10k; R_0402_1005Metric
R4, R17: 6k8; R_0402_1005Metric
R5, R6: 220k; R_0402_1005Metric
R7, R8: 330k; R_0402_1005Metric
R9: 33k; R_0402_1005Metric
R10, R11: 1k; R_0402_1005Metric
R12, R13, R14, R15: 330R; R_0402_1005Metric
R18, R19: 470R; R_0402_1005Metric
RV1, RV2: 5k; Potentiometer_Bourns_3266Y_Vertical
U1: AMS1117-5.0; SOT-223-3_TabPin2
U2: SeeeduinoXIAOPin; Seeeduino XIAO Pin
U3, U5: MCP4725xxx-xCH; SOT-23-6
U4: MCP6002-xSN; SOIC-8_3.9x4.9mm_P1.27mm

Connections:
+3V3: C11.1, C12.1, D4.1, D6.1, D8.1, J11.3, R1.1, R2.1, U2.12, U3.3, U5.3, U5.6
+5V: C4.1, C13.1, D10.1, D12.1, R12.1, R13.1, U1.2, U2.14, U4.8
+12V: C1.1, C3.1, D1.1, U1.3
-12V: C2.2, D2.2
A7: D8.2, D9.1, R9.1, U2.8
A8: C6.1, D6.2, D7.1, R6.1, R8.2, U2.9
A9: C5.1, D4.2, D5.1, R5.1, R7.2, U2.10
D1: R10.2, U2.2
D2: R11.2, U2.3
D3: C7.1, J9.1, U2.4
D6: C8.1, J9.2, U2.7
D10: J9.3, U2.11
GND: C1.2, C2.1, C3.2, C4.2, C5.2, C6.2, C7.2, C8.2, C9.2, C10.2, C11.2, C12.2, C13.2, D5.2, D7.2, D9.2, D11.2, D13.2, J1.GND, J9.4, J10.2, J10.4, J11.1, J11.5, J12.2, J12.4, Q1.2, Q2.2, R4.1, R7.1, R8.1, R17.1, R20.1, U1.1, U2.13, U3.2, U4.4, U5.2
Gate1: C9.1, J10.3, R14.1
Gate2: C10.1, J12.3, R15.1
In1: J10.1, R5.2
In2: J12.1, R6.2
unnamed: D1.2, J1.+12V
unnamed: D2.1, J1.-12V
unnamed: D10.2, D11.1, R18.2, RV1.1, RV1.2, U4.1
unnamed: D12.2, D13.1, R19.2, RV2.1, RV2.2, U4.7
unnamed: Q1.1, R10.1
unnamed: Q1.3, R12.2, R14.2
unnamed: Q2.1, R11.1
unnamed: Q2.3, R13.2, R15.2
unnamed: R3.1, U4.3
unnamed: R3.2, U3.1
unnamed: R4.2, RV1.3, U4.2
unnamed: R16.1, U4.5
unnamed: R16.2, U5.1
unnamed: R17.2, RV2.3, U4.6
unnamed: R20.2, U3.6
Out1: J10.5, R18.1
Out2: J12.5, R19.1
SCL: J11.4, R2.2, U2.6, U3.5, U5.5
SDA: J11.2, R1.2, U2.5, U3.4, U5.4
Trigger: J9.5, R9.2
