mzuelch/CATs-Eurosynth/Modules/Standard Line/Abakus/Electronics/Main/Abakus Main.kicad_pcb

## KiCad design Modules/Standard Line/Abakus/Electronics/Main/Abakus Main.kicad_pcb (2022-09-25)

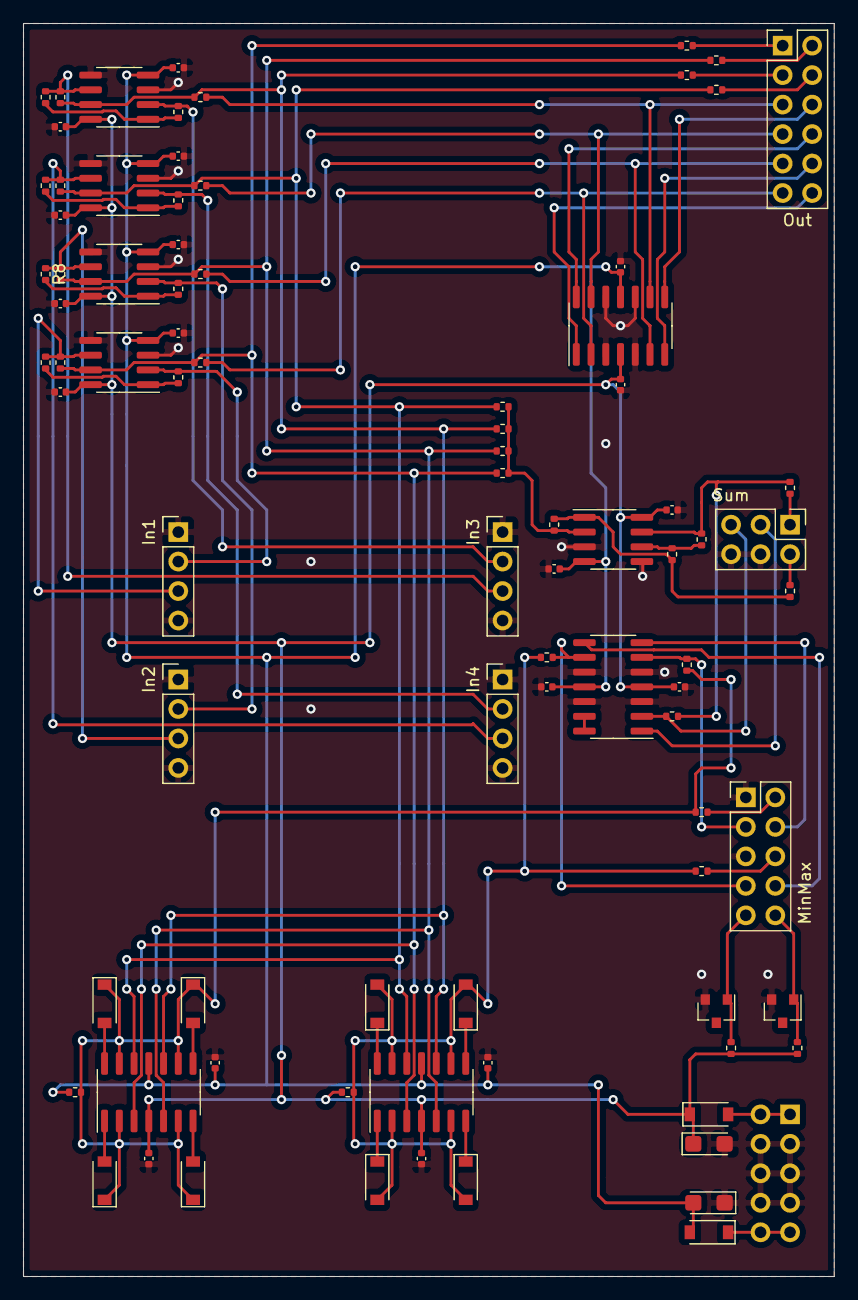
[picture p133: board Abakus Main.kicad_pcb from above]

Board: 2 copper layers, 69.8 x 108.0 mm, 87 parts (1 on the bottom side), 60 nets.

Parts:
C1, C2: 10µ; CP_EIA-3216-18_Kemet-A
C3, C4, C5, C6, C7, C8, C9, C10, C11, C12, C13, C14, C15, C16, C17, C18, C19, C20: 100n; C_0402_1005Metric
D1, D2: B5817W; D_SOD-123
D3, D4, D5, D6, D7, D8, D9, D10: 1N4148W; D_SOD-123
J1: Power; Power_2x5_Vertical
J2: Out; PinHeader_2x06_P2.54mm_Vertical
J3: In1; PinHeader_1x04_P2.54mm_Vertical
J4: In2; PinHeader_1x04_P2.54mm_Vertical
J5: In3; PinHeader_1x04_P2.54mm_Vertical
J6: In4; PinHeader_1x04_P2.54mm_Vertical
J7: Sum; PinHeader_2x03_P2.54mm_Vertical
J8: MinMax; PinHeader_2x05_P2.54mm_Vertical
R1, R2, R3, R4, R7, R8, R9, R10, R11, R12, R13, R14, R21, R22, R23, R24, R27, R29, R30: 100k; R_0402_1005Metric
R5, R6, R15, R16, R17, R18, R19, R20, R25, R26, R28, R31, R32, R34, R36, R37, R38: 1k; R_0402_1005Metric
R33, R35: 10k; R_0402_1005Metric
U1, U2, U3, U4, U5: TL072CDT; SOIC-8_3.9x4.9mm_P1.27mm
U6, U7, U8, U9: TL074CDR; SOIC-14_3.9x8.7mm_P1.27mm
U10: LM4040AIM3-5.0/NOPB; SOT-23
U11: LM4040C10IDBZR; SOT-23

Connections:
+5V: J8.9, R37.1, U10.1
+10V: J8.10, R38.1, U11.1
+12V: C1.1, C3.1, C5.1, C7.1, C9.1, C11.1, C13.1, C15.1, C17.1, C19.1, D1.1, R35.2, R37.2, R38.2, U1.8, U2.8, U3.8, U4.8, U5.8, U6.4, U7.4, U8.4, U9.4
+In1: J3.2, R1.2, U1.2
+In2: J4.2, R2.2, U2.2
+In3: J5.2, R3.2, U3.2
+In4: J6.2, R4.2, U4.2
-12V: C2.2, C4.2, C6.2, C8.2, C10.2, C12.2, C14.2, C16.2, C18.2, C20.2, D2.2, R33.1, U1.4, U2.4, U3.4, U4.4, U5.4, U6.11, U7.11, U8.11, U9.11
-In1: J3.3, R7.1, R11.2, U1.6
-In2: J4.3, R8.1, R12.2, U2.6
-In3: J5.3, R9.1, R13.2, U3.6
-In4: J6.3, R10.1, R14.2, U4.6
GND: C1.2, C2.1, C3.2, C4.1, C5.2, C6.1, C7.2, C8.1, C9.2, C10.1, C11.2, C12.1, C13.2, C14.1, C15.2, C16.1, C17.2, C18.1, C19.2, C20.1, J1.GND, J3.1, J3.4, J4.1, J4.4, J5.1, J5.4, J6.1, J6.4, J7.4, J7.6, J8.1, J8.5, U1.3, U1.5, U2.3, U2.5, U3.3, U3.5, U4.3, U4.5, U5.3, U5.5, U8.3, U8.5, U8.10, U8.12, U9.3, U9.5, U9.10, U9.12, U10.2, U11.2
Int_Inv_Sum: R27.1, R28.2, R29.2, U5.1
Int_Max: D3.1, D4.1, D5.1, D6.1, R31.2, R33.2, R34.2, U6.2, U6.6, U6.9, U6.13
Int_Min: D7.2, D8.2, D9.2, D10.2, R26.2, R35.1, R36.2, U7.2, U7.6, U7.9, U7.13
Int_Out1: R5.2, R11.1, R17.2, R21.2, U1.7, U6.3, U7.3
Int_Out2: R12.1, R15.2, R18.2, R22.2, U2.7, U6.5, U7.5
Int_Out3: R6.2, R13.1, R19.2, R23.2, U3.7, U6.10, U7.10
Int_Out4: R14.1, R16.2, R20.2, R24.2, U4.7, U6.12, U7.12
Int_Sum: R25.2, R30.1, R32.2, U5.7
Inv_Sum: J7.2, R28.1
LED_Max_1: J8.3, R31.1, U9.6
LED_Max_2: J8.4, U9.7
LED_Min_1: J8.7, R26.1, U9.9
LED_Min_2: J8.8, U9.8
LED_Out_1_1: J2.11, R5.1, U8.2
LED_Out_1_2: J2.12, U8.1
LED_Out_2_1: J2.9, R15.1, U8.6
LED_Out_2_2: J2.10, U8.7
LED_Out_3_1: J2.5, R6.1, U8.9
LED_Out_3_2: J2.6, U8.8
LED_Out_4_1: J2.7, R16.1, U8.13
LED_Out_4_2: J2.8, U8.14
LED_Sum_1: J7.5, R25.1, U9.2
LED_Sum_2: J7.3, U9.1
Max: J8.2, R34.1
Min: J8.6, R36.1
unnamed: D1.2, J1.+12V
unnamed: D2.1, J1.-12V
unnamed: D3.2, U6.1
unnamed: D4.2, U6.7
unnamed: D5.2, U6.8
unnamed: D6.2, U6.14
unnamed: D7.1, U7.1
unnamed: D8.1, U7.7
unnamed: D9.1, U7.8
unnamed: D10.1, U7.14
unnamed: R1.1, R7.2, U1.1
unnamed: R2.1, R8.2, U2.1
unnamed: R3.1, R9.2, U3.1
unnamed: R4.1, R10.2, U4.1
unnamed: R21.1, R22.1, R23.1, R24.1, R27.2, U5.2
unnamed: R29.1, R30.2, U5.6
unnamed: U9.13, U9.14
Out1: J2.1, R17.1
Out2: J2.2, R18.1
Out3: J2.3, R19.1
Out4: J2.4, R20.1
Sum: J7.1, R32.1
