mzuelch/CATs-Eurosynth/Modules/HAGIWO/6Ch Trigger Sequencer/Electronics/Main/HAGIWO 6Ch Gate Sequencer Main.kicad_pcb

## KiCad design Modules/HAGIWO/6Ch Trigger Sequencer/Electronics/Main/HAGIWO 6Ch Gate Sequencer Main.kicad_pcb (2022-09-25)

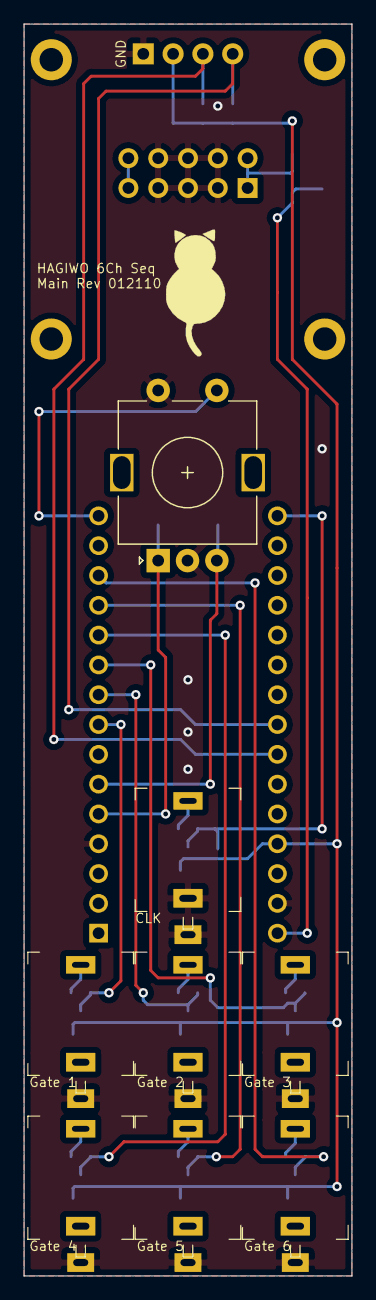
[picture p134: board HAGIWO 6Ch Gate Sequencer Main.kicad_pcb from above]

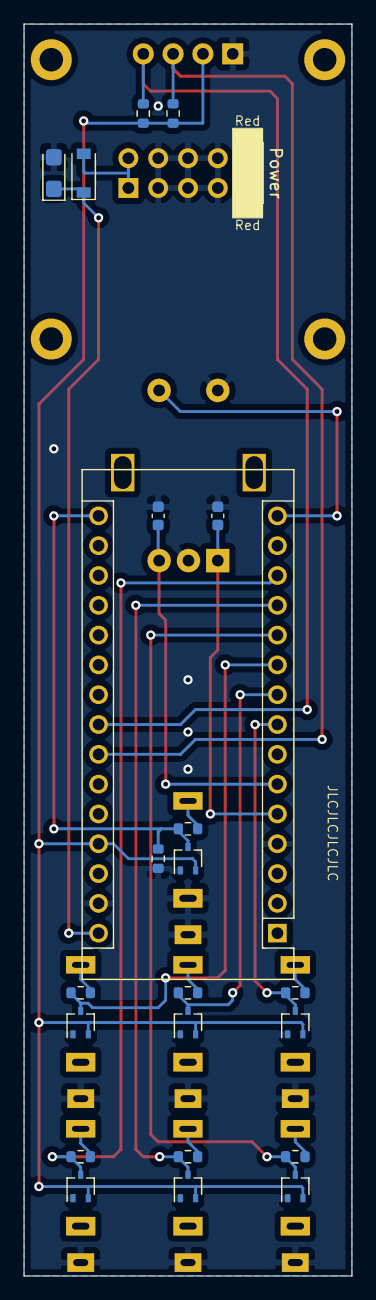
[picture p135: board HAGIWO 6Ch Gate Sequencer Main.kicad_pcb from below]

Board: 2 copper layers, 27.9 x 106.7 mm, 32 parts (23 on the bottom side), 23 nets.

Parts:
A1: Arduino_Nano_v3.x; Arduino_Nano
C1: 10µF/16V; CP_EIA-3216-18_Kemet-A
C7, C8: 10n; C_0603_1608Metric
D1: B5817W; D_SOD-123
D2, D3, D4, D5, D6, D7, D8: BAV99W; SOT-323_SC-70
DISP1: MC096xx; MC096Gx
J1: Power; Power_2x5_Vertical
J2: Gate 2; Jack_3.5mm_QingPu_WQP-PJ301M-12
J3: CLK; Jack_3.5mm_QingPu_WQP-PJ301M-12
J4: Gate 1; Jack_3.5mm_QingPu_WQP-PJ301M-12
J5: Gate 3; Jack_3.5mm_QingPu_WQP-PJ301M-12
J6: Gate 4; Jack_3.5mm_QingPu_WQP-PJ301M-12
J7: Gate 5; Jack_3.5mm_QingPu_WQP-PJ301M-12
J8: Gate 6; Jack_3.5mm_QingPu_WQP-PJ301M-12
R1, R4, R5, R6, R8, R9, R10: 470R; R_0603_1608Metric
R2: 100k; R_0603_1608Metric
R3, R7: 3k3; R_0603_1608Metric
SW2: Encoder; RotaryEncoder_Alps_EC11E-Switch_Vertical_H20mm

Connections:
+5V: A1.27, D2.2, D3.2, D4.2, D5.2, D6.2, D7.2, D8.2, DISP1.VCC, R3.2, R7.2
+12V: A1.30, C1.1, D1.1
+12VA: D1.2, J1.+12V
CLK: A1.16, D2.3, R1.1, R2.2
ENC_A: A1.5, C7.1, SW2.A
ENC_B: A1.6, C8.1, SW2.B
ENC_SW: A1.15, SW2.S1
G1: A1.8, D3.3, R4.2
G2: A1.9, D4.3, R5.2
G3: A1.10, D5.3, R6.2
G4: A1.11, D6.3, R8.2
G5: A1.12, D7.3, R9.2
G6: A1.13, D8.3, R10.2
GND: A1.4, A1.29, C1.2, C7.2, C8.2, D2.1, D3.1, D4.1, D5.1, D6.1, D7.1, D8.1, DISP1.GND, J1.GND, J2.S, J3.S, J3.TN, J4.S, J5.S, J6.S, J7.S, J8.S, R2.1, SW2.C, SW2.S2
unnamed: J2.T, R5.1
unnamed: J3.T, R1.2
unnamed: J4.T, R4.1
unnamed: J5.T, R6.1
unnamed: J6.T, R8.1
unnamed: J7.T, R9.1
unnamed: J8.T, R10.1
SCL: A1.24, DISP1.SCL, R7.1
SDA: A1.23, DISP1.SDA, R3.1
