mzuelch/CATs-Eurosynth/Modules/HAGIWO/Display/Electronics/Main/HAGIWO Display Main.kicad_pcb

## KiCad design Modules/HAGIWO/Display/Electronics/Main/HAGIWO Display Main.kicad_pcb (2022-09-25)

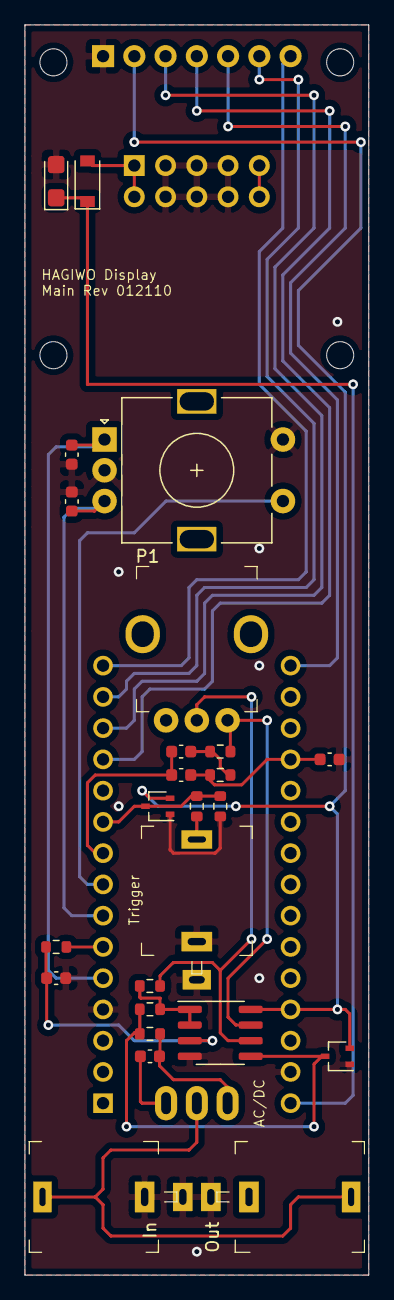
[picture p136: board HAGIWO Display Main.kicad_pcb from above]

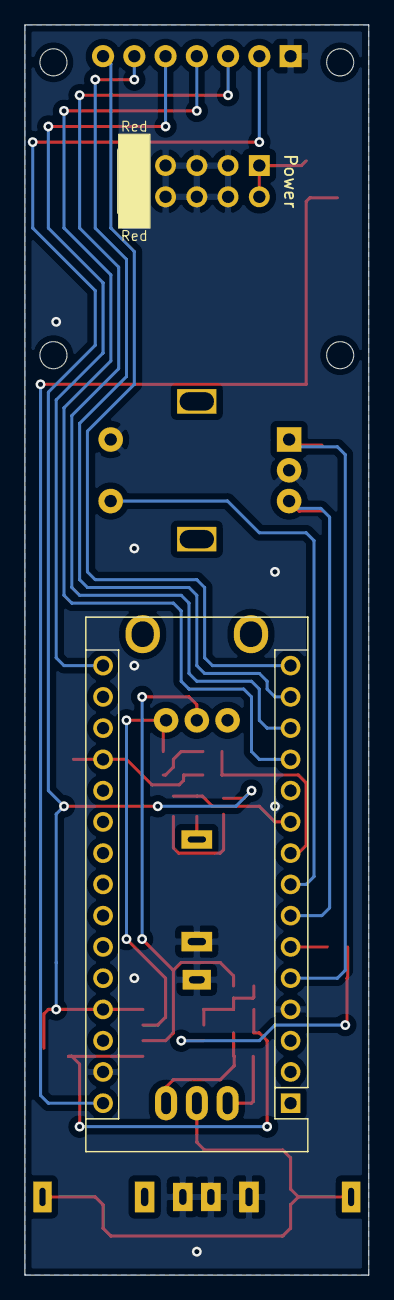
[picture p137: board HAGIWO Display Main.kicad_pcb from below]

Board: 2 copper layers, 27.9 x 101.6 mm, 33 parts (2 on the bottom side), 26 nets.

Parts:
A1: Arduino_Nano_v3.x; Arduino_Nano
C1: 10µF/16V; CP_EIA-3216-18_Kemet-A
C2: 1µF; C_0603_1608Metric
C3: 4.7µF; C_0603_1608Metric
C4, C5: 22n; C_0603_1608Metric
C6: 470p; C_0603_1608Metric
C7, C8: 10n; C_0603_1608Metric
D1: B5817W; D_SOD-123
D2, D3: BAV99W; SOT-323_SC-70
DISP1: MSP096x
H1, H2, H3, H4: MountingHole; MountingHole_2.2mm_M2
J1: Power; Power_2x5_Vertical
J2: Trigger; Jack_3.5mm_QingPu_WQP-PJ301M-12
J3: In; Jack_3.5mm_QingPu_WQP-PJ301M-12
J4: Out; Jack_3.5mm_QingPu_WQP-PJ301M-12
P1: B100k; Potentiometer_AlpsAlpine_RK09K1130
R1, R5: 47k; R_0603_1608Metric
R2, R7, R8: 1k; R_0603_1608Metric
R3: 100k; R_0603_1608Metric
R4, R6: 10k; R_0603_1608Metric
SW1: AC/DC; SMTS-102-2xxx
SW2: Encoder; RotaryEncoder_Alps_EC11E-Switch_Vertical_H20mm
U1: MCP6002-xSN; SOIC-8_3.9x4.9mm_P1.27mm

Connections:
+5V: A1.27, D2.2, D3.2, DISP1.VCC, U1.8
+12V: A1.30, C1.1, D1.1
+12VA: D1.2, J1.+12V
CS: A1.15, DISP1.CS
DC: A1.14, DISP1.DC
DI: A1.12, DISP1.DI
DO: A1.13, DISP1.DO
ENC_A: A1.5, C7.1, SW2.A
ENC_B: A1.7, C8.1, SW2.B
ENC_SW: A1.8, SW2.S1
Fast_PWM: A1.6, R1.2
GND: A1.4, A1.29, C1.2, C2.2, C6.2, C7.2, C8.2, D2.1, D3.1, DISP1.GND, J1.GND, J2.S, J2.TN, J3.S, J3.TN, J4.S, R3.1, SW2.C, SW2.S2, U1.4
In: A1.19, C5.1, C6.1, R8.1
LPF_Enable: A1.9, C4.2, C5.2
unnamed: C2.1, R1.1, U1.3
unnamed: C3.1, R5.2, SW1.1
unnamed: C3.2, SW1.3
unnamed: C4.1, R7.1, R8.2
unnamed: D3.3, R4.2, R5.1, U1.5
unnamed: J2.T, R2.2
unnamed: J3.T, J4.T, SW1.2
unnamed: P1.CW, R7.2, U1.7
unnamed: P1.W, R6.2, U1.6
Offset: R4.1, R6.1, U1.1, U1.2
RST: A1.16, DISP1.RESET
TriggerIn: A1.10, D2.3, R2.1, R3.2
