mzuelch/CATs-Eurosynth/Modules/Standard Line/4Ch Mixer/Electronics/Main/4CH Mixer.kicad_pcb

## KiCad design Modules/Standard Line/4Ch Mixer/Electronics/Main/4CH Mixer.kicad_pcb (2022-09-25)

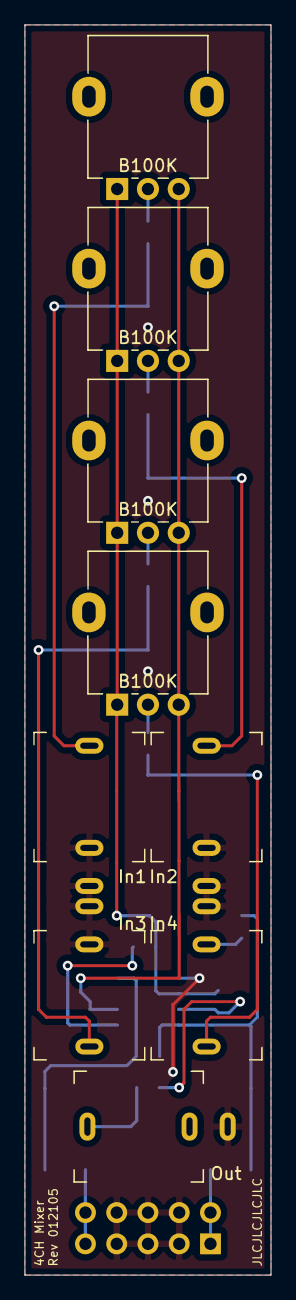
[picture p138: board 4CH Mixer.kicad_pcb from above]

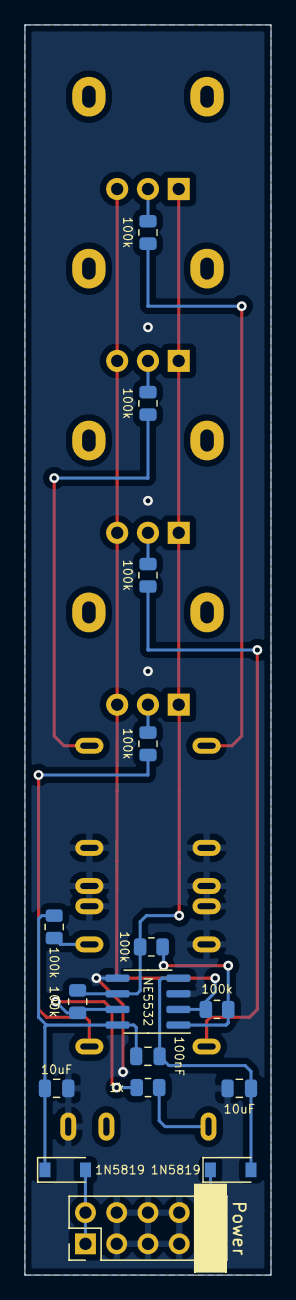
[picture p139: board 4CH Mixer.kicad_pcb from below]

Board: 2 copper layers, 20.0 x 101.6 mm, 25 parts (16 on the bottom side), 19 nets.

Parts:
C1: 100nF; C_0805_2012Metric
C2, C3: 10uF; C_0805_2012Metric
D1, D2: 1N5819; D_SOD-123
IC1: NE5532; SOIC-8_3.9x4.9mm_P1.27mm
J1: In1; PJ-301-M-12
J2: In2; PJ-301-M-12
J3: In3; PJ-301-M-12
J4: In4; PJ-301-M-12
J5: Power; PinHeader_2x05_P2.54mm_Vertical
J6: Out; PJ-301-M-12
P1, P2, P3, P4: B100K; Potentiometer_Alpha_RD901F-40-00D_Single_Vertical
R4, R5, R6, R7, R8, R9, R10, R11: 100k; R_0805_2012Metric
R12: 1k; R_0805_2012Metric

Connections:
+12V: C1.1, C2.1, D1.1, IC1.8, R4.1
+12VA: D1.2, J5.1, J5.2
-12V: C1.2, C3.2, D2.2, IC1.4
-12VA: D2.1, J5.9, J5.10
GND: C2.2, C3.1, IC1.3, IC1.5, J1.S, J1.TN, J2.S, J2.TN, J3.S, J3.TN, J4.S, J5.3, J5.4, J5.5, J5.6, J5.7, J5.8, J6.S
unnamed: IC1.1, R9.1, R10.2
unnamed: IC1.7, R11.1, R12.2
unnamed: J1.T, R5.2
unnamed: J2.T, R6.2
unnamed: J3.T, R7.2
unnamed: J4.T, R8.2
unnamed: J4.TN, R4.2
unnamed: J6.T, R12.1
unnamed: P1.2, R5.1
unnamed: P2.2, R6.1
unnamed: P3.2, R7.1
unnamed: P4.2, R8.1
Sum+: IC1.2, P1.3, P2.3, P3.3, P4.3, R9.2
Sum-: IC1.6, P1.1, P2.1, P3.1, P4.1, R10.1, R11.2
