mzuelch/CATs-Eurosynth/Modules/HAGIWO/Ringfolder/Electronics/Main/HAGIWO Ring Modulator Main.kicad_pcb

## KiCad design Modules/HAGIWO/Ringfolder/Electronics/Main/HAGIWO Ring Modulator Main.kicad_pcb (2022-09-25)

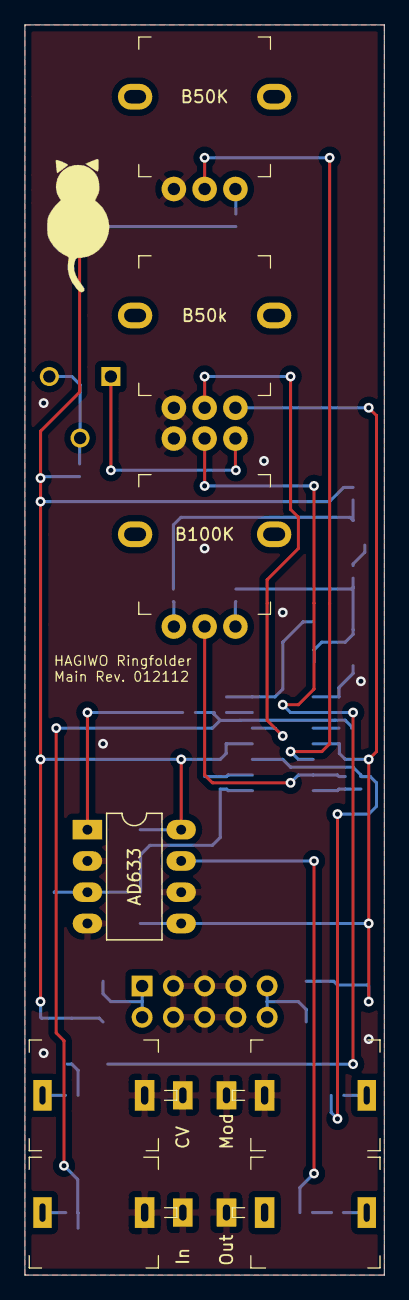
[picture p140: board HAGIWO Ring Modulator Main.kicad_pcb from above]

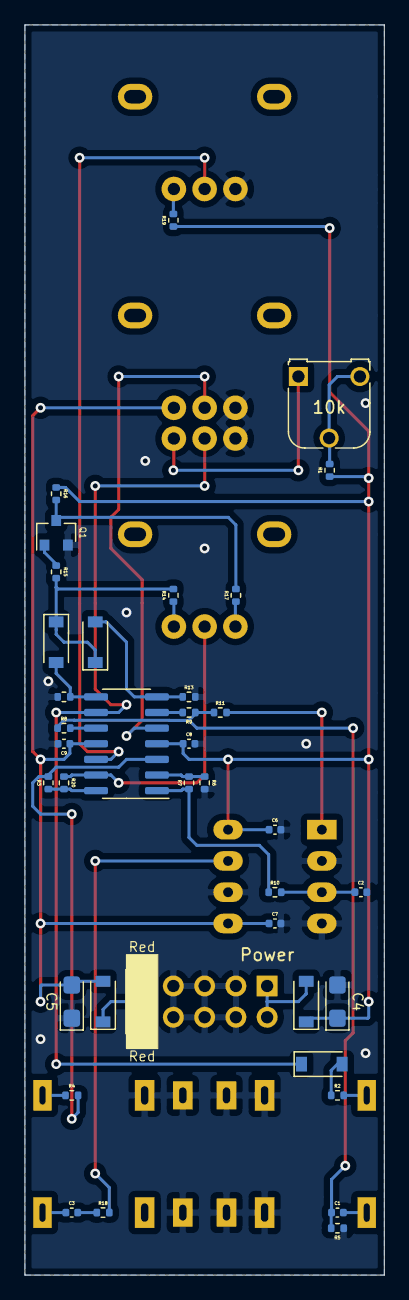
[picture p141: board HAGIWO Ring Modulator Main.kicad_pcb from below]

Board: 2 copper layers, 29.2 x 101.6 mm, 46 parts (38 on the bottom side), 35 nets.

Parts:
C1, C3: 1µ; C_0402_1005Metric
C2: 3n3; C_0402_1005Metric
C4, C5: 10µ/25V; CP_EIA-3216-18_Kemet-A
C6, C7, C8, C9: 100n; C_0402_1005Metric
D1, D2, D3: 1N4148; D_SOD-123
D4, D5: 1N5817; D_SOD-123
J1: CV; Jack_3.5mm_QingPu_WQP-PJ301M-12
J2: In; Jack_3.5mm_QingPu_WQP-PJ301M-12
J3: Mod; Jack_3.5mm_QingPu_WQP-PJ301M-12
J4: Out; Jack_3.5mm_QingPu_WQP-PJ301M-12
J5: Power; Power_2x5_Vertical
P1: B50k; Potentiometer_AlpsAlpine_RK09L1240
P2: B100K; Potentiometer_AlpsAlpine_RK09L1140
P3: B50K; Potentiometer_AlpsAlpine_RK09L1140
Q1: MMBT3904; SOT-23
R1, R2, R7, R10, R15: 10k; R_0402_1005Metric
R3, R4, R6, R8, R9, R11: 33k; R_0402_1005Metric
R5, R12, R13, R16, R20: 100k; R_0402_1005Metric
R14, R17, R19: 47k; R_0402_1005Metric
R18: 4k7; R_0402_1005Metric
T1: 10k; Potentiometer_Runtron_RM-065_Vertical
U1: AD633; DIP-8_W7.62mm_LongPads
U2: TL074; SOIC-14_3.9x8.7mm_P1.27mm

Connections:
+12V: C4.1, C6.2, C8.2, D4.1, R1.2, R16.2, R19.2, U1.8, U2.4
-12V: C5.2, C7.1, C9.1, D5.2, P1.CW1, U1.5, U2.11
Fold_In: R3.2, R20.1, U2.14
GND: C2.1, C4.2, C5.1, C6.1, C7.2, C8.1, C9.2, J1.S, J1.TN, J2.S, J2.TN, J3.S, J3.TN, J4.S, J5.GND, P1.CCW1, P1.CCW2, P3.CCW, Q1.2, R5.1, R6.1, R12.1, R13.1, U1.2, U1.4, U1.6
unnamed: C1.1, R5.2, R8.2, R9.2, R11.2
unnamed: C1.2, J2.T
unnamed: C2.2, R10.1, U1.3
unnamed: C3.1, J4.T
unnamed: C3.2, R18.1
unnamed: D1.1, P1.W2, U2.9
unnamed: D1.2, R2.1
unnamed: D2.1, D3.1, R14.2, R15.2
unnamed: D2.2, R12.2, U2.8
unnamed: D3.2, R13.2, U2.7
unnamed: D4.2, J5.+12V
unnamed: D5.1, J5.-12V
unnamed: J1.T, R2.2
unnamed: J3.T, R4.2
unnamed: P1.CW2, T1.1
unnamed: P1.W1, U2.5
unnamed: P2.CCW, R17.1
unnamed: P2.CW, R14.1
unnamed: P2.W, R20.2, U2.13
unnamed: P3.CW, R19.1
unnamed: P3.W, U2.12
unnamed: Q1.1, R15.1
unnamed: Q1.3, R16.1, R17.2
unnamed: R1.1, T1.2, T1.3
unnamed: R3.1, R4.1, U2.3
unnamed: R6.2, R7.2, U2.2
unnamed: R8.1, U2.10
unnamed: R9.1, U2.6
unnamed: R7.1, R10.2, U2.1
unnamed: R11.1, U1.1
unnamed: R18.2, U1.7
