mzuelch/CATs-Eurosynth/Modules/Slim Line/Precision Adder/Electronics/Main/Slim Precision Adder Main.kicad_pcb

## KiCad design Modules/Slim Line/Precision Adder/Electronics/Main/Slim Precision Adder Main.kicad_pcb (2022-09-25)

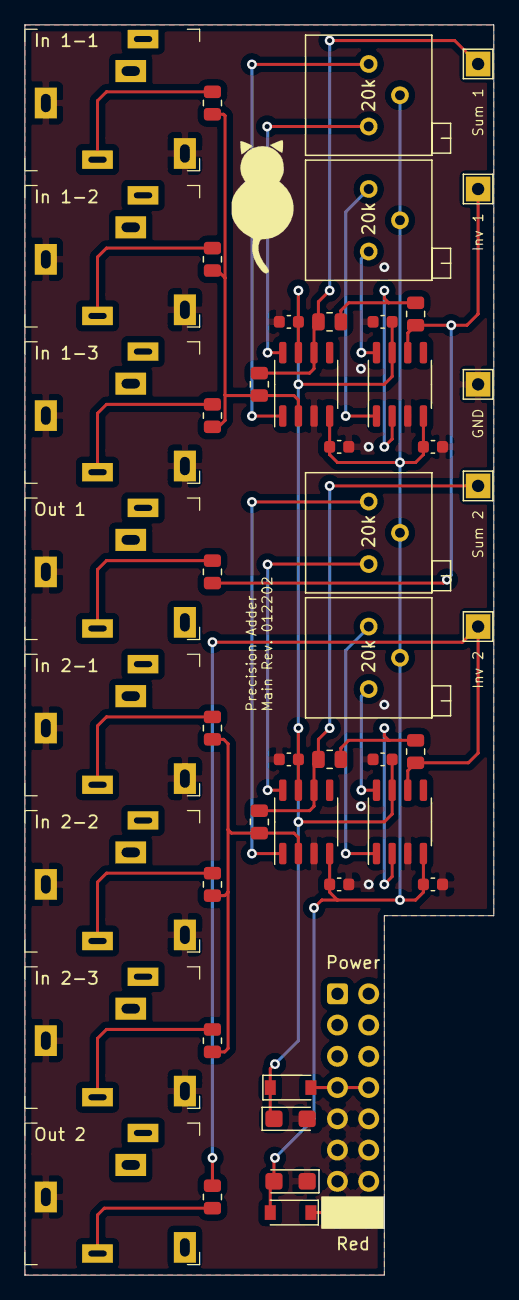
[picture p142: board Slim Precision Adder Main.kicad_pcb from above]

Board: 2 copper layers, 38.1 x 101.6 mm, 48 parts (0 on the bottom side), 29 nets.

Parts:
C1, C6: 10u; CP_EIA-3216-18_Kemet-A
C2, C3, C4, C5, C7, C8, C9, C10: 100n; C_0603_1608Metric
D1, D2: B5819W SL; D_SOD-123
J1: In 1-1; Jack_3.5mm_QingPu_WQP-PJ324M
J2: Out 1; Jack_3.5mm_QingPu_WQP-PJ324M
J3: In 1-2; Jack_3.5mm_QingPu_WQP-PJ324M
J4: In 1-3; Jack_3.5mm_QingPu_WQP-PJ324M
J5: In 2-1; Jack_3.5mm_QingPu_WQP-PJ324M
J6: Out 2; Jack_3.5mm_QingPu_WQP-PJ324M
J7: In 2-2; Jack_3.5mm_QingPu_WQP-PJ324M
J8: In 2-3; Jack_3.5mm_QingPu_WQP-PJ324M
J9: Power; Power_2x8_Horizontal
R1, R2, R3, R5, R6, R7, R8, R9, R10, R12, R13, R14: 100k ±0.05%; R_0805_2012Metric
R4, R11: 240; R_0805_2012Metric
RV1, RV2, RV3, RV4: 20k; Potentiometer_Bourns_3299P_Horizontal
TP1: Inv 1; TestPoint_THTPad_2.0x2.0mm_Drill1.0mm
TP2: Sum 1; TestPoint_THTPad_2.0x2.0mm_Drill1.0mm
TP3: GND; TestPoint_THTPad_2.0x2.0mm_Drill1.0mm
TP4: Inv 2; TestPoint_THTPad_2.0x2.0mm_Drill1.0mm
TP5: Sum 2; TestPoint_THTPad_2.0x2.0mm_Drill1.0mm
U1, U2, U3, U4: OP07CDR; SO-8_3.9x4.9mm_P1.27mm

Connections:
+12V: C1.1, C2.1, C3.1, C4.1, C5.1, D1.1, U1.7, U2.7, U3.7, U4.7
-12V: C6.2, C7.2, C8.2, C9.2, C10.2, D2.2, RV1.2, RV2.2, RV3.2, RV4.2, U1.4, U2.4, U3.4, U4.4
GND: C1.2, C2.2, C3.2, C4.2, C5.2, C6.1, C7.1, C8.1, C9.1, C10.1, J1.S, J1.TN, J2.S, J3.S, J3.TN, J4.S, J4.TN, J5.S, J5.TN, J6.S, J7.S, J7.TN, J8.S, J8.TN, J9.GND, TP3.1, U1.3, U2.3, U3.3, U4.3
unnamed: D1.2, J9.+12V
unnamed: D2.1, J9.-12V
unnamed: J1.T, R3.2
unnamed: J2.T, R4.1
unnamed: J3.T, R6.2
unnamed: J4.T, R7.2
unnamed: J5.T, R10.2
unnamed: J6.T, R11.1
unnamed: J7.T, R13.2
unnamed: J8.T, R14.2
unnamed: R1.1, R4.2, TP1.1, U1.6
unnamed: R1.2, R5.1, U1.2
unnamed: R2.1, R5.2, TP2.1, U2.6
unnamed: R2.2, R3.1, R6.1, R7.1, U2.2
unnamed: R9.2, R10.1, R13.1, R14.1, U4.2
unnamed: R8.1, R11.2, TP4.1, U3.6
unnamed: R8.2, R12.1, U3.2
unnamed: R9.1, R12.2, TP5.1, U4.6
unnamed: RV1.1, U1.8
unnamed: RV1.3, U1.1
unnamed: RV2.1, U2.8
unnamed: RV2.3, U2.1
unnamed: RV3.1, U3.8
unnamed: RV3.3, U3.1
unnamed: RV4.1, U4.8
unnamed: RV4.3, U4.1
