mzuelch/CATs-Eurosynth/Modules/HAGIWO/4Ch Sample Player/Electronics/Main/HAGIWO 4Ch Sampler.kicad_pcb

## KiCad design Modules/HAGIWO/4Ch Sample Player/Electronics/Main/HAGIWO 4Ch Sampler.kicad_pcb (2022-09-25)

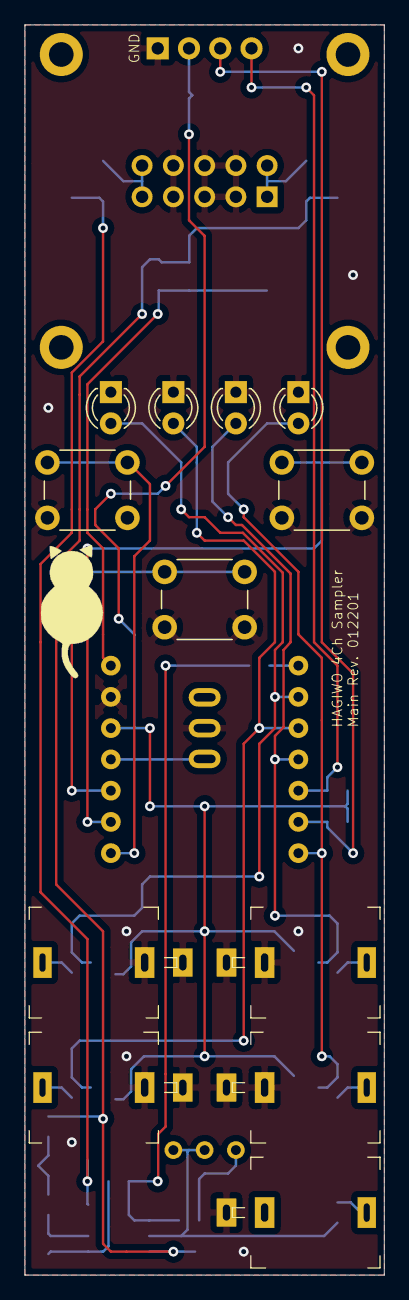
[picture p143: board HAGIWO 4Ch Sampler.kicad_pcb from above]

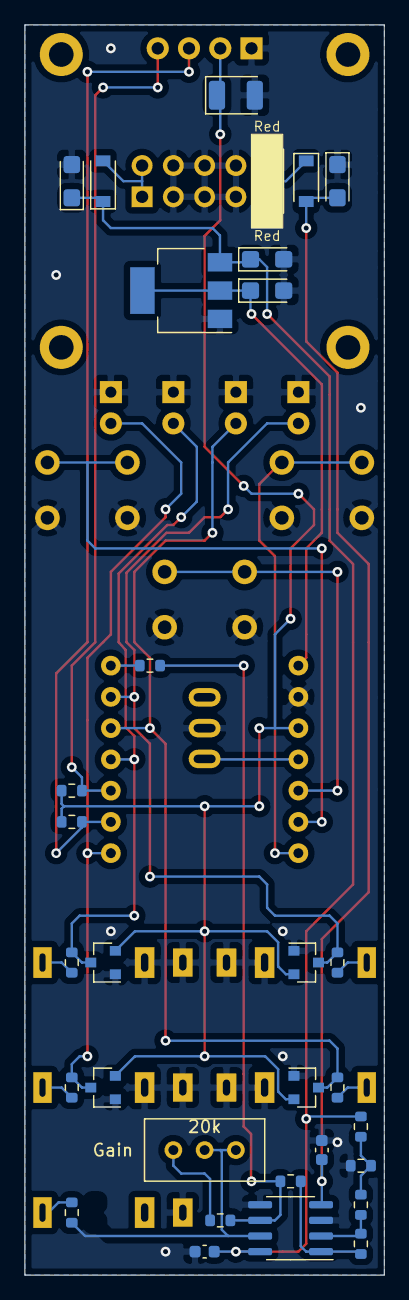
[picture p144: board HAGIWO 4Ch Sampler.kicad_pcb from below]

Board: 2 copper layers, 29.2 x 101.6 mm, 46 parts (32 on the bottom side), 29 nets.

Parts:
C1: 100uF/6.3V; CP_EIA-3528-21_Kemet-B
C3, C4, C5, C7: 10uF/16V; CP_EIA-3216-18_Kemet-A
C6, C8: 100n; C_0603_1608Metric
D1, D2, D5, D6: BAV99; SOT-23
D3: Ch 1; LED_D3.0mm
D4: Ch 3; LED_D3.0mm
D7: Ch 2; LED_D3.0mm
D8: Ch 4; LED_D3.0mm
D9, D10: B5819W SL; D_SOD-123
DISP1: MC096xx; 0.96inch_OLED_MC096GX
J1: Ch. 1 In; Jack_3.5mm_QingPu_WQP-PJ301M-12
J2: Ch. 3 In; Jack_3.5mm_QingPu_WQP-PJ301M-12
J3: Ch. 2 In; Jack_3.5mm_QingPu_WQP-PJ301M-12
J4: Ch. 4 In; Jack_3.5mm_QingPu_WQP-PJ301M-12
J5: Out; Jack_3.5mm_QingPu_WQP-PJ301M-12
J6: Power; Power_2x5_Vertical
R1, R2: 3k3; R_0603_1608Metric
R3, R4, R7, R8: 33k; R_0603_1608Metric
R5: 7k5; R_0603_1608Metric
R6, R9, R10, R13: 10k; R_0603_1608Metric
R11: 27k; R_0603_1608Metric
R12: 1k5; R_0603_1608Metric
R14: 1k; R_0603_1608Metric
SW1: Left; SW_PUSH_6mm
SW2: Right; SW_PUSH_6mm
SW3: Down; SW_PUSH_6mm
SW4: Mode; SMTS-1xx-Solder
T1: 20k; Potentiometer_Bourns_3296W_Vertical
U1: TL072CDT; SOIC-8_3.9x4.9mm_P1.27mm
U2: SeeeduinoXIAOPin; Seeeduino XIAO Pin
U3: AMS1117-5.0; SOT-223-3_TabPin2

Connections:
+3V3: C1.1, D1.2, D2.2, D5.2, D6.2, DISP1.VCC, R1.2, R2.2, U2.12
+5V: C5.1, U2.14, U3.2
+12V: C3.1, C4.1, C6.2, D9.1, R5.2, U1.8, U3.3
-12V: C7.2, C8.1, D10.2, U1.4
A7: SW1.1, U2.8
A8: SW2.1, U2.9
A9: SW3.1, U2.10
D1: D1.3, D3.2, R3.1, U2.2
D2: D5.3, D7.2, R7.1, U2.3
D3: D2.3, D4.2, R4.1, U2.4
D4: D6.3, D8.2, R8.1, U2.7
D10: SW4.2, U2.11
DAC: R13.2, U2.1
GND: C1.2, C3.2, C4.2, C5.2, C6.1, C7.1, C8.2, D1.1, D2.1, D3.1, D4.1, D5.1, D6.1, D7.1, D8.1, DISP1.GND, J1.S, J1.TN, J2.S, J2.TN, J3.S, J3.TN, J4.S, J4.TN, J5.S, J6.GND, R12.1, SW1.2, SW2.2, SW3.2, SW4.1, U1.3, U1.5, U2.13, U3.1
unnamed: D9.2, J6.+12V
unnamed: D10.1, J6.-12V
unnamed: J1.T, R3.2
unnamed: J2.T, R4.2
unnamed: J3.T, R7.2
unnamed: J4.T, R8.2
unnamed: J5.T, R14.1
unnamed: R6.2, R9.1, U1.2
unnamed: R10.1, R11.2, R13.1, U1.6
unnamed: R6.1, R10.2, U1.1
unnamed: R11.1, T1.1
unnamed: R5.1, R9.2, R12.2
unnamed: R14.2, T1.2, T1.3, U1.7
SCL: DISP1.SCL, R2.1, U2.6
SDA: DISP1.SDA, R1.1, U2.5
