mzuelch/CATs-Eurosynth/Modules/MFOS/Noise Cornucopia/Electronics/Main 2/MFOS Noise Cornucopia Main 2.kicad_pcb

## KiCad design Modules/MFOS/Noise Cornucopia/Electronics/Main 2/MFOS Noise Cornucopia Main 2.kicad_pcb (2022-09-25)

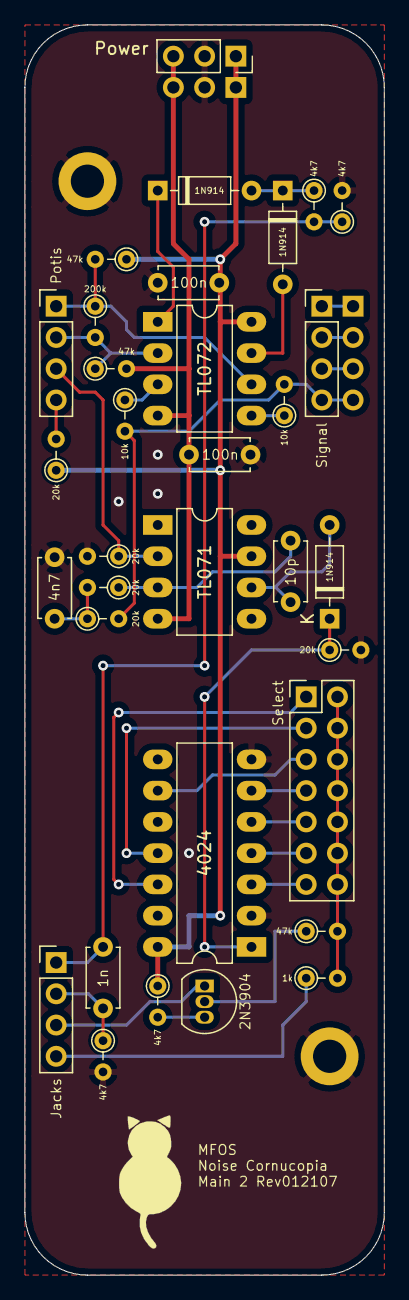
[picture p145: board MFOS Noise Cornucopia Main 2.kicad_pcb from above]

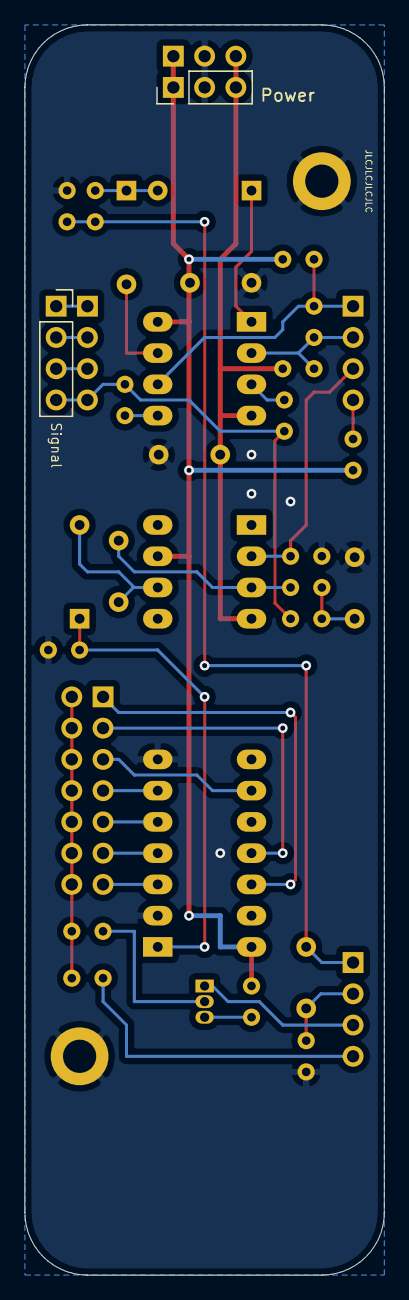
[picture p146: board MFOS Noise Cornucopia Main 2.kicad_pcb from below]

Board: 2 copper layers, 29.2 x 101.6 mm, 37 parts (2 on the bottom side), 34 nets.

Parts:
C8, C13: 100n; C_Disc_D4.7mm_W2.5mm_P5.00mm
C15: 1n; C_Disc_D4.7mm_W2.5mm_P5.00mm
C16: 10p; C_Disc_D4.7mm_W2.5mm_P5.00mm
C17: 4n7; C_Disc_D4.7mm_W2.5mm_P5.00mm
D1, D2, D3: 1N914; D_DO-35_SOD27_P7.62mm_Horizontal
H1, H2: MountingHole_Pad; MountingHole_2.7mm_M2.5_DIN965_Pad
J1: Select; PinHeader_2x07_P2.54mm_Vertical
J2: Power; PinSocket_1x03_P2.54mm_Vertical
J3: Signal; PinSocket_1x04_P2.54mm_Vertical
J4: Signal; PinHeader_1x04_P2.54mm_Vertical
J5: Power; PinHeader_1x03_P2.54mm_Vertical
J6: Potis; PinHeader_1x04_P2.54mm_Vertical
J7: Jacks; PinHeader_1x04_P2.54mm_Vertical
Q2: 2N3904; TO-92_Inline
R13, R22, R30: 47k; R_Axial_DIN0204_L3.6mm_D1.6mm_P2.54mm_Vertical
R14, R20: 10k; R_Axial_DIN0204_L3.6mm_D1.6mm_P2.54mm_Vertical
R15, R21, R23, R24: 4k7; R_Axial_DIN0204_L3.6mm_D1.6mm_P2.54mm_Vertical
R19: 200k; R_Axial_DIN0204_L3.6mm_D1.6mm_P2.54mm_Vertical
R25, R26, R27, R29, R31: 20k; R_Axial_DIN0204_L3.6mm_D1.6mm_P2.54mm_Vertical
R32: 1k; R_Axial_DIN0204_L3.6mm_D1.6mm_P2.54mm_Vertical
U3: TL072; DIP-8_W7.62mm_LongPads
U4: TL071; DIP-8_W7.62mm_LongPads
U5: 4024; DIP-14_W7.62mm_LongPads

Connections:
+12V: C8.2, J2.1, J5.1, R13.1, R24.1, R25.1, U3.8, U4.7, U5.14
-12V: C13.1, J2.3, J5.3, R22.2, U3.4, U4.4
GHP: C15.2, J7.2, R23.1
GND: C8.1, C13.2, C17.2, H1.1, H2.1, J2.2, J5.2, R21.2, R23.2, R29.2, R31.2, U5.2, U5.7
GNS: C15.1, J7.1, R15.2, R21.1
GRNS1: J6.1, R13.2, R19.1, U3.6
GRNS2: J6.2, R19.2, R22.1, U3.2
GTF1: J6.3, R31.1, U4.2
GTF2: J6.4, R25.2
LEDA: J7.3, Q2.1
NOISE_INT: J3.4, J4.4, R14.2, R20.2, R26.2
unnamed: C16.1, R27.1, U4.3
unnamed: C16.2, D3.2, U4.6
unnamed: C17.1, R26.1, R27.2
unnamed: D1.1, D2.2, R15.1
unnamed: D1.2, U3.7
unnamed: D2.1, U3.1
unnamed: D3.1, R29.1, U5.1
unnamed: J1.1, U5.12
unnamed: J1.3, U5.11
unnamed: J1.5, U5.9
unnamed: J1.7, U5.6
unnamed: J1.9, U5.5
unnamed: J1.2, J1.4, J1.6, J1.8, J1.10, J1.12, J1.14, R30.2, R32.2
unnamed: J1.11, U5.4
unnamed: J1.13, U5.3
unnamed: J3.1, J4.1
unnamed: J3.2, J4.2
unnamed: J3.3, J4.3
unnamed: Q2.2, R30.1
unnamed: Q2.3, R24.2
unnamed: R14.1, U3.5
unnamed: R20.1, U3.3
RNGT: J7.4, R32.1
