mzuelch/CATs-Eurosynth/Modules/Slim Line/Buffered Multiple/Electronics/Main/Buffered Multiple Main.kicad_pcb

## KiCad design Modules/Slim Line/Buffered Multiple/Electronics/Main/Buffered Multiple Main.kicad_pcb (2022-09-25)

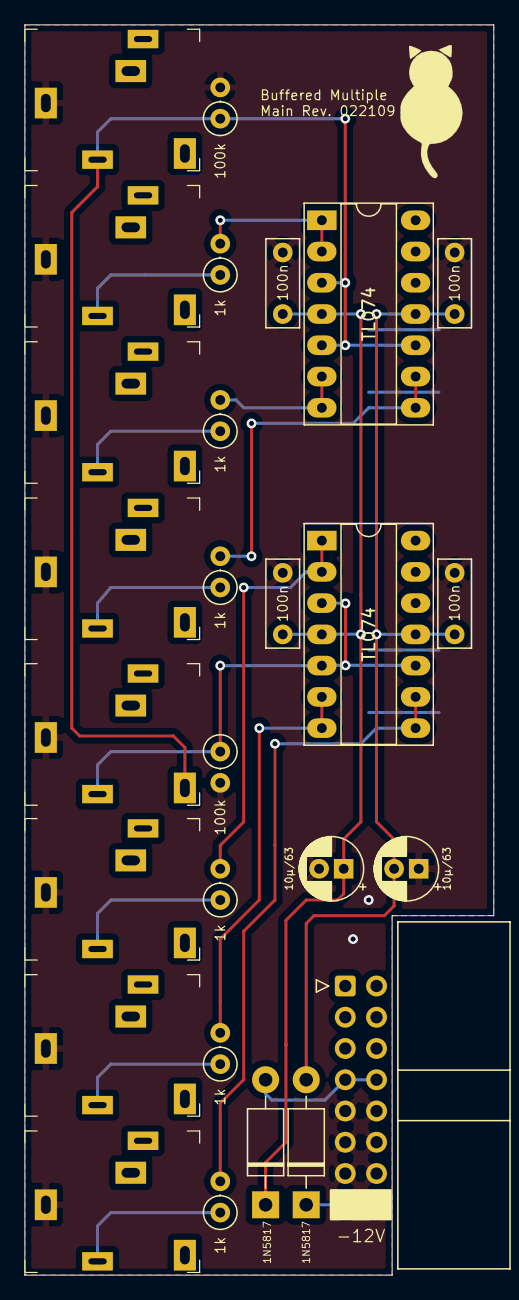
[picture p147: board Buffered Multiple Main.kicad_pcb from above]

Board: 2 copper layers, 38.1 x 101.6 mm, 27 parts (0 on the bottom side), 19 nets.

Parts:
C1, C2: 10µ/63; CP_Radial_D5.0mm_P2.00mm
C3, C4, C5, C6: 100n; C_Rect_L7.0mm_W2.5mm_P5.00mm
D1, D2: 1N5817; D_DO-41_SOD81_P10.16mm_Horizontal
J1: In 1; Jack_3.5mm_QingPu_WQP-PJ324M
J2: Power; IDC-Header_2x08_P2.54mm_Horizontal
J3: Out 1-1; Jack_3.5mm_QingPu_WQP-PJ324M
J4: Out 1-2; Jack_3.5mm_QingPu_WQP-PJ324M
J5: Out 2-1; Jack_3.5mm_QingPu_WQP-PJ324M
J6: Out 2-2; Jack_3.5mm_QingPu_WQP-PJ324M
J7: In 2; Jack_3.5mm_QingPu_WQP-PJ324M
J8: Out 1-3; Jack_3.5mm_QingPu_WQP-PJ324M
J9: Out 2-3; Jack_3.5mm_QingPu_WQP-PJ324M
R1, R6: 100k; R_Axial_DIN0207_L6.3mm_D2.5mm_P2.54mm_Vertical
R2, R3, R4, R5, R7, R8: 1k; R_Axial_DIN0207_L6.3mm_D2.5mm_P2.54mm_Vertical
U1, U2: TL074; DIP-14_W7.62mm_Socket_LongPads

Connections:
+12V: C1.1, C3.1, C5.1, D1.1, U1.4, U2.4
+12VA: D1.2, J2.7, J2.8
-12V: C2.2, C4.2, C6.2, D2.2, U1.11, U2.11
-12VA: D2.1, J2.15, J2.16
GND: C1.2, C2.1, C3.2, C4.1, C5.2, C6.1, J1.S, J2.9, J2.10, J2.11, J2.12, J2.13, J2.14, J3.S, J4.S, J5.S, J6.S, J7.S, J8.S, J9.S, R1.2, R6.2
unnamed: J1.T, J7.TN, R1.1, U1.3, U1.5, U1.10
unnamed: J3.T, R2.1
unnamed: J4.T, R3.1
unnamed: J5.T, R4.1
unnamed: J6.T, R5.1
unnamed: J7.T, R6.1, U2.3, U2.5, U2.10
unnamed: J8.T, R7.1
unnamed: J9.T, R8.1
unnamed: R2.2, U1.1, U1.2
unnamed: R3.2, U1.6, U1.7
unnamed: R4.2, U2.1, U2.2
unnamed: R5.2, U2.6, U2.7
unnamed: R7.2, U1.8, U1.9
unnamed: R8.2, U2.8, U2.9
