mzuelch/CATs-Eurosynth/Modules/HAGIWO/Arduino VCO/Electronics/Main/Arduino VCO Main.kicad_pcb

## KiCad design Modules/HAGIWO/Arduino VCO/Electronics/Main/Arduino VCO Main.kicad_pcb (2022-09-25)

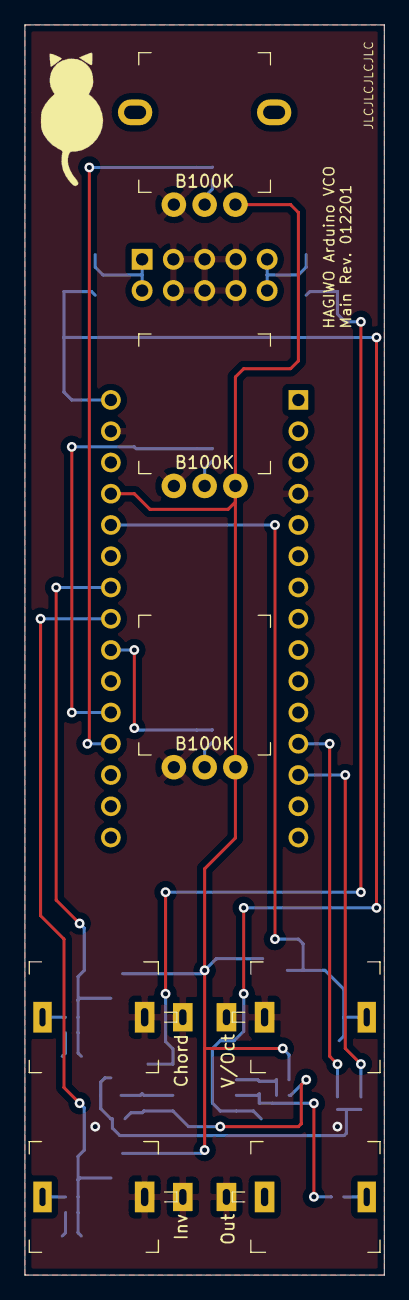
[picture p148: board Arduino VCO Main.kicad_pcb from above]

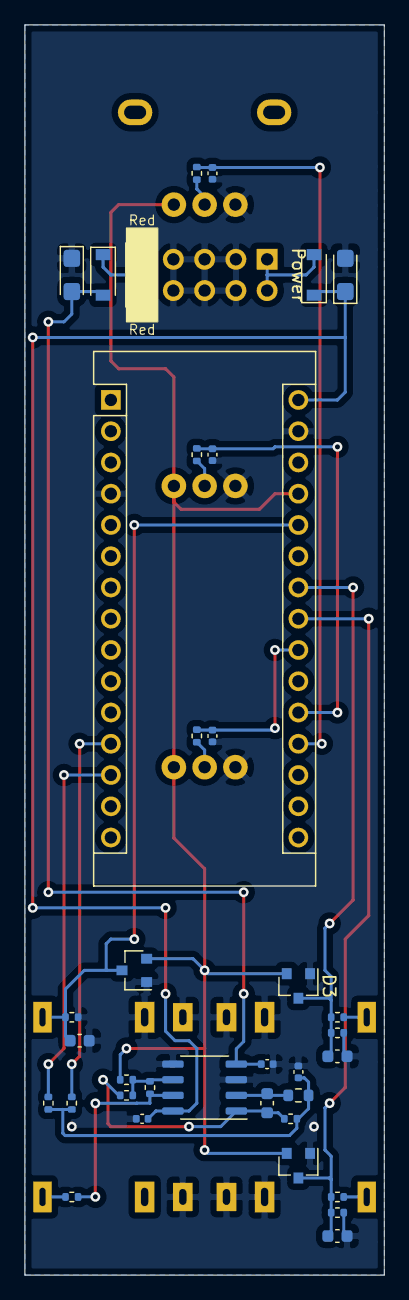
[picture p149: board Arduino VCO Main.kicad_pcb from below]

Board: 2 copper layers, 29.2 x 101.6 mm, 43 parts (36 on the bottom side), 25 nets.

Parts:
A1: Arduino_Nano_v3.x; Arduino_Nano
C1, C11: 10µ; CP_EIA-3216-18_Kemet-A
C2, C3, C4: 10n; C_0402_1005Metric
C5, C7, C9: 68n; C_0603_1608Metric
C6: 3.3n; C_0603_1608Metric
C8: 22n; C_0402_1005Metric
C10, C12: 100n; C_0402_1005Metric
D1, D6: B5819W SL; D_SOD-123
D2, D3, D4: BAV99; SOT-23
J1: Power; Power_2x5_Vertical
J2: V/Oct; Jack_3.5mm_QingPu_WQP-PJ301M-12
J3: Inv; Jack_3.5mm_QingPu_WQP-PJ301M-12
J4: Out; Jack_3.5mm_QingPu_WQP-PJ301M-12
J5: Chord; Jack_3.5mm_QingPu_WQP-PJ301M-12
P1: B100K; Potentiometer_AlpsAlpine_RK09L1140
P2, P3: B100K; Potentiometer_AlpsAlpine_RK09L1140_oS
R1, R2, R3, R9, R12, R15: 1k; R_0402_1005Metric
R4, R8, R10, R11, R14, R16: 100k; R_0402_1005Metric
R5: 499k; R_0402_1005Metric
R6: 3k9; R_0402_1005Metric
R7: 7k5; R_0402_1005Metric
R13: 2k7; R_0603_1608Metric
U1: TL072CDT; SO-8_3.9x4.9mm_P1.27mm

Connections:
+5V: A1.27, D2.2, D3.2, D4.2, P1.CW, P2.CW, P3.CW, R16.2
+12V: A1.30, C1.1, C10.1, D1.1, U1.8
-12V: C11.2, C12.2, D6.2, U1.4
A0: A1.19, C2.1, R1.1
A1: A1.20, C3.1, R2.1
A3: A1.22, C4.1, R3.1
A4: A1.23, C7.1, D2.3, R8.1, R9.2
A5: A1.24, C9.1, D3.3, R11.1, R12.2
A7: A1.26, C5.1, D4.3, J2.T, R4.1
D9: A1.12, R6.2
D10: A1.13, R5.2
GND: A1.4, A1.29, C1.2, C2.2, C3.2, C4.2, C5.2, C7.2, C8.2, C9.2, C10.2, C11.1, C12.1, D2.1, D3.1, D4.1, J1.GND, J2.S, J2.TN, J3.S, J3.TN, J4.S, J5.S, J5.TN, P1.CCW, P2.CCW, P3.CCW, R4.2, R8.2, R11.2, U1.3, U1.5
unnamed: C6.1, R7.2, R14.2, U1.1
unnamed: C6.2, R13.1, U1.2
unnamed: C8.1, R5.1, R6.1, R7.1, R13.2
unnamed: D1.2, J1.+12V
unnamed: D6.1, J1.-12V
unnamed: J3.T, R9.1
unnamed: J4.T, R15.1
unnamed: J5.T, R12.1
unnamed: P1.W, R1.2
unnamed: P2.W, R2.2
unnamed: P3.W, R3.2
unnamed: R10.1, R15.2, U1.7
unnamed: R10.2, R14.1, R16.1, U1.6
