mzuelch/CATs-Eurosynth/Modules/Standard Line/Abakus/Electronics/Control/Abakus Control.kicad_pcb

## KiCad design Modules/Standard Line/Abakus/Electronics/Control/Abakus Control.kicad_pcb (2022-09-25)

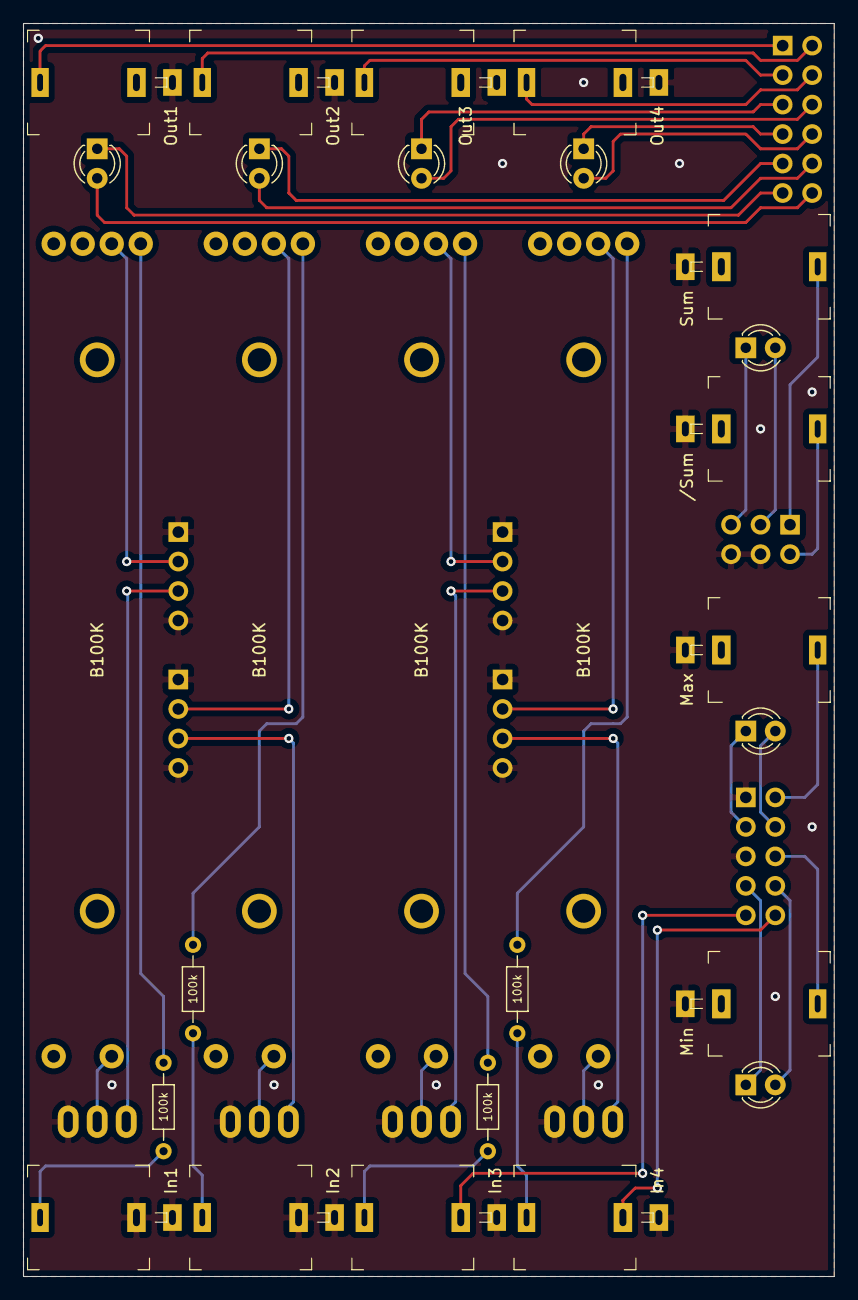
[picture p150: board Abakus Control.kicad_pcb from above]

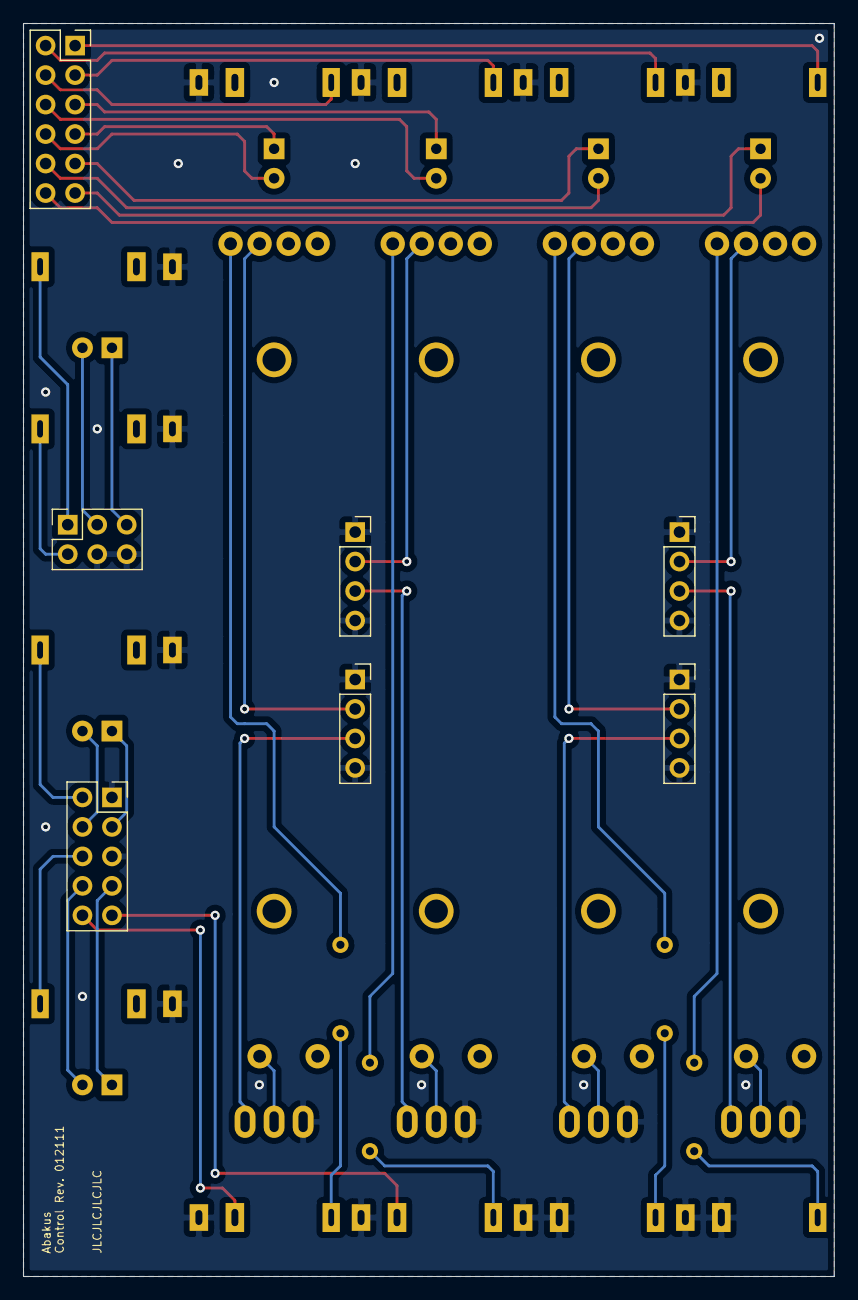
[picture p151: board Abakus Control.kicad_pcb from below]

Board: 2 copper layers, 69.8 x 108.0 mm, 38 parts (7 on the bottom side), 45 nets.

Parts:
D1: Out1; LED_D3.0mm
D2: Out2; LED_D3.0mm
D3: Out3; LED_D3.0mm
D4: Out4; LED_D3.0mm
D5: Min; LED_D3.0mm
D6: Sum; LED_D3.0mm
D7: Max; LED_D3.0mm
J1: In1; Jack_3.5mm_QingPu_WQP-PJ301M-12
J2: In2; Jack_3.5mm_QingPu_WQP-PJ301M-12
J3: In3; Jack_3.5mm_QingPu_WQP-PJ301M-12
J4: In4; Jack_3.5mm_QingPu_WQP-PJ301M-12
J5: Out1; Jack_3.5mm_QingPu_WQP-PJ301M-12
J6: Out2; Jack_3.5mm_QingPu_WQP-PJ301M-12
J7: Out3; Jack_3.5mm_QingPu_WQP-PJ301M-12
J8: Out4; Jack_3.5mm_QingPu_WQP-PJ301M-12
J9: /Sum; Jack_3.5mm_QingPu_WQP-PJ301M-12
J10: Sum; Jack_3.5mm_QingPu_WQP-PJ301M-12
J11: Max; Jack_3.5mm_QingPu_WQP-PJ301M-12
J12: Min; Jack_3.5mm_QingPu_WQP-PJ301M-12
J13: Out; PinSocket_2x06_P2.54mm_Vertical
J14: In1; PinSocket_1x04_P2.54mm_Vertical
J15: In2; PinSocket_1x04_P2.54mm_Vertical
J16: In3; PinSocket_1x04_P2.54mm_Vertical
J17: In4; PinSocket_1x04_P2.54mm_Vertical
J18: Sum; PinSocket_2x03_P2.54mm_Vertical
J19: MinMax; PinSocket_2x05_P2.54mm_Vertical
P1, P2, P3, P4: B100K; Potentiometer_AlpsAlpine_RS6011YA9A07
R1, R2, R3, R4: 100k; R_Axial_DIN0204_L3.6mm_D1.6mm_P7.62mm_Horizontal
SW1: Att/AV1; SMTS-102-2xxx
SW2: Att/AV2; SMTS-102-2xxx
SW3: Att/AV3; SMTS-102-2xxx
SW4: Att/AV4; SMTS-102-2xxx

Connections:
+5V: J3.TN, J19.9
+10V: J4.TN, J19.10
+In1: J14.2, P1.CW
+In2: J15.2, P2.CW
+In3: J16.2, P3.CW
+In4: J17.2, P4.CW
-In1: J14.3, SW1.1
-In2: J15.3, SW2.1
-In3: J16.3, SW3.1
-In4: J17.3, SW4.1
GND: J1.S, J1.TN, J2.S, J2.TN, J3.S, J4.S, J5.S, J6.S, J7.S, J8.S, J9.S, J10.S, J11.S, J12.S, J14.1, J14.4, J15.1, J15.4, J16.1, J16.4, J17.1, J17.4, J18.4, J18.6, J19.1, J19.5, SW1.3, SW2.3, SW3.3, SW4.3
Inv_Sum: J9.T, J18.2
LED_Max_1: D7.1, J19.3
LED_Max_2: D7.2, J19.4
LED_Min_1: D5.1, J19.7
LED_Min_2: D5.2, J19.8
LED_Out_1_1: D1.1, J13.11
LED_Out_1_2: D1.2, J13.12
LED_Out_2_1: D2.1, J13.9
LED_Out_2_2: D2.2, J13.10
LED_Out_3_1: D3.1, J13.5
LED_Out_3_2: D3.2, J13.6
LED_Out_4_1: D4.1, J13.7
LED_Out_4_2: D4.2, J13.8
LED_Sum_1: D6.1, J18.5
LED_Sum_2: D6.2, J18.3
Max: J11.T, J19.2
Min: J12.T, J19.6
unnamed: J1.T, R1.2
unnamed: J2.T, R2.2
unnamed: J3.T, R3.2
unnamed: J4.T, R4.2
unnamed: P1.CCW, SW1.2
unnamed: P1.W, R1.1
unnamed: P2.CCW, SW2.2
unnamed: P2.W, R2.1
unnamed: P3.CCW, SW3.2
unnamed: P3.W, R3.1
unnamed: P4.CCW, SW4.2
unnamed: P4.W, R4.1
Out1: J5.T, J13.1
Out2: J6.T, J13.2
Out3: J7.T, J13.3
Out4: J8.T, J13.4
Sum: J10.T, J18.1
