mzuelch/CATs-Eurosynth/Modules/Slim Line/VCA/Electronics/Main/Slimline VCA Main.kicad_pcb

## KiCad design Modules/Slim Line/VCA/Electronics/Main/Slimline VCA Main.kicad_pcb (2022-09-25)

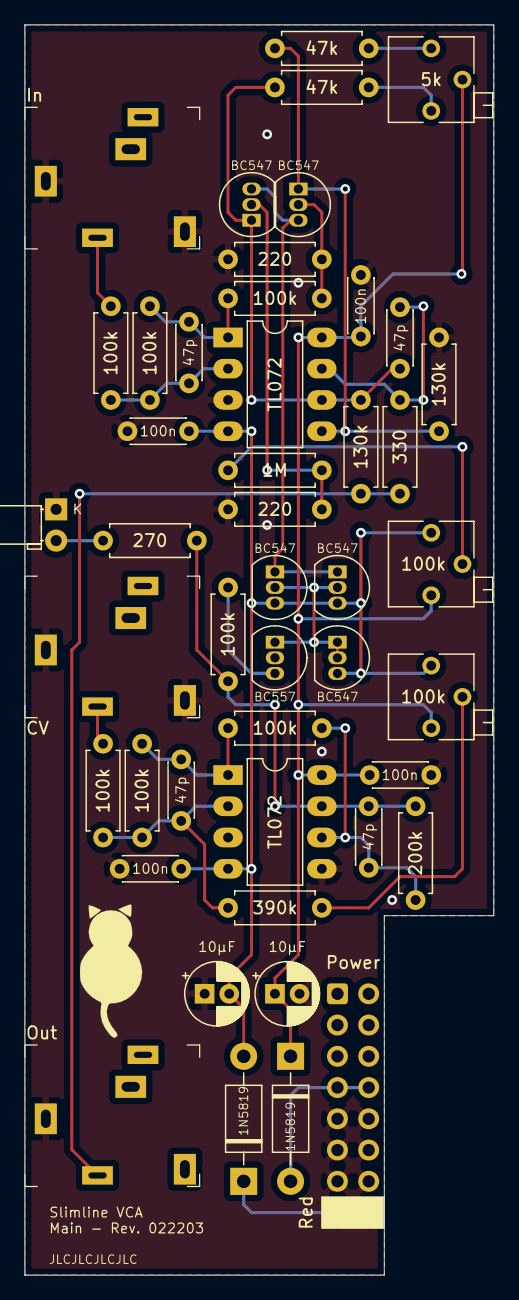
[picture p152: board Slimline VCA Main.kicad_pcb from above]

Board: 2 copper layers, 38.1 x 101.6 mm, 46 parts (0 on the bottom side), 27 nets.

Parts:
C1, C2, C3, C4: 47p; C_Disc_D4.3mm_W1.9mm_P5.00mm
C5, C6: 10µF; CP_Radial_D5.0mm_P2.00mm
C7, C8, C9, C10: 100n; C_Disc_D4.3mm_W1.9mm_P5.00mm
D1, D2: 1N5819; D_DO-41_SOD81_P10.16mm_Horizontal
D3: LED; LED_D3.0mm_Horizontal_O1.27mm_Z2.0mm
J1: CV; Jack_3.5mm_QingPu_WQP-PJ324M
J2: In; Jack_3.5mm_QingPu_WQP-PJ324M
J3: Out; Jack_3.5mm_QingPu_WQP-PJ324M
J4: Power; Power_2x8_Horizontal
Q1: BC557; TO-92_Inline
Q2, Q3, Q4, Q5, Q6: BC547; TO-92_Inline
R1: 390k; R_Axial_DIN0207_L6.3mm_D2.5mm_P7.62mm_Horizontal
R2, R3, R4, R6, R7, R8, R9: 100k; R_Axial_DIN0207_L6.3mm_D2.5mm_P7.62mm_Horizontal
R5: 200k; R_Axial_DIN0207_L6.3mm_D2.5mm_P7.62mm_Horizontal
R10, R13: 220; R_Axial_DIN0207_L6.3mm_D2.5mm_P7.62mm_Horizontal
R11, R12: 47k; R_Axial_DIN0207_L6.3mm_D2.5mm_P7.62mm_Horizontal
R14: 1M; R_Axial_DIN0207_L6.3mm_D2.5mm_P7.62mm_Horizontal
R15, R16: 130k; R_Axial_DIN0207_L6.3mm_D2.5mm_P7.62mm_Horizontal
R17: 330; R_Axial_DIN0207_L6.3mm_D2.5mm_P7.62mm_Horizontal
R18: 270; R_Axial_DIN0207_L6.3mm_D2.5mm_P7.62mm_Horizontal
RV1, RV3: 100k; Potentiometer_Bourns_3266P_Horizontal
RV2: 5k; Potentiometer_Bourns_3266P_Horizontal
U1, U2: TL072; DIP-8_W7.62mm_LongPads

Connections:
+12V: C5.1, C7.2, C9.2, D1.1, RV1.1, RV2.2, RV3.1, U1.8, U2.8
-12V: C6.2, C8.1, C10.1, D2.2, Q2.3, Q4.3, Q5.3, RV1.3, RV3.3, U1.4, U2.4
GND: C5.2, C6.1, C7.1, C8.2, C9.1, C10.2, D3.1, J1.S, J1.TN, J2.S, J2.TN, J3.S, J4.GND, Q1.2, R10.2, R13.2, R15.2, U1.3, U2.3, U2.5
unnamed: C1.1, R3.1, R4.2, U2.1
unnamed: C1.2, R1.1, R2.1, R3.2, U2.2
unnamed: C2.1, R5.1, R6.2, R18.2, U2.7
unnamed: C2.2, R4.1, R5.2, U2.6
unnamed: C3.1, R8.1, R9.2, U1.1
unnamed: C3.2, R7.1, R8.2, U1.2
unnamed: C4.1, R17.2, U1.7
unnamed: C4.2, Q6.1, R12.2, R16.2, U1.6
unnamed: D1.2, J4.+12V
unnamed: D2.1, J4.-12V
unnamed: D3.2, R18.1
unnamed: J1.T, R2.2
unnamed: J2.T, R7.2
unnamed: J3.T, R16.1, R17.1
unnamed: Q1.1, Q2.1, Q2.2, Q4.2, Q5.2
unnamed: Q1.3, R6.1
unnamed: Q3.1, R11.2, R15.1, U1.5
unnamed: Q3.2, R9.1, R10.1
unnamed: Q3.3, Q4.1, Q5.1, Q6.3
unnamed: Q6.2, R13.1, R14.2
unnamed: R1.2, RV1.2
unnamed: R11.1, RV2.3
unnamed: R12.1, RV2.1
unnamed: R14.1, RV3.2
