mzuelch/CATs-Eurosynth/Modules/MFOS/Noise Cornucopia/Electronics/Control/MFOS Noise Cornucopia Control.kicad_pcb

## KiCad design Modules/MFOS/Noise Cornucopia/Electronics/Control/MFOS Noise Cornucopia Control.kicad_pcb (2022-09-25)

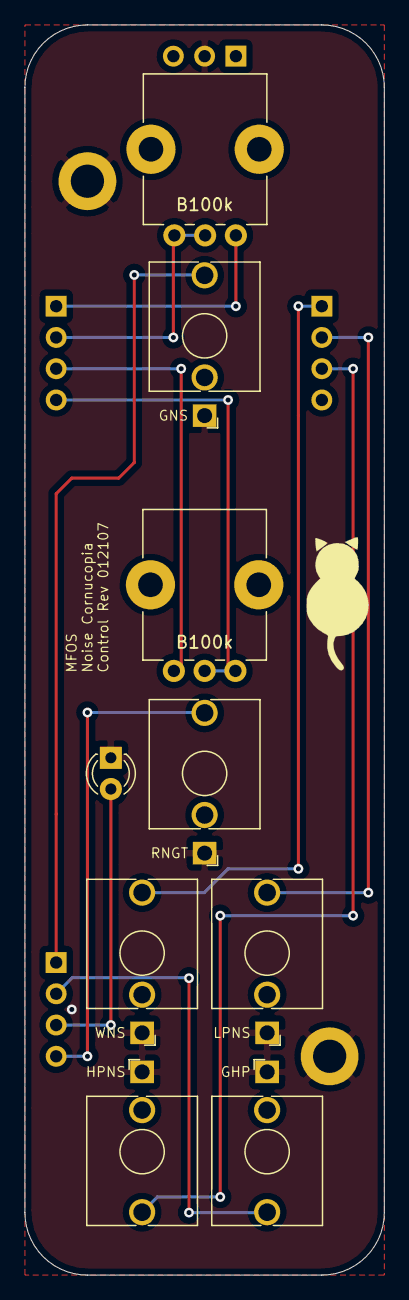
[picture p153: board MFOS Noise Cornucopia Control.kicad_pcb from above]

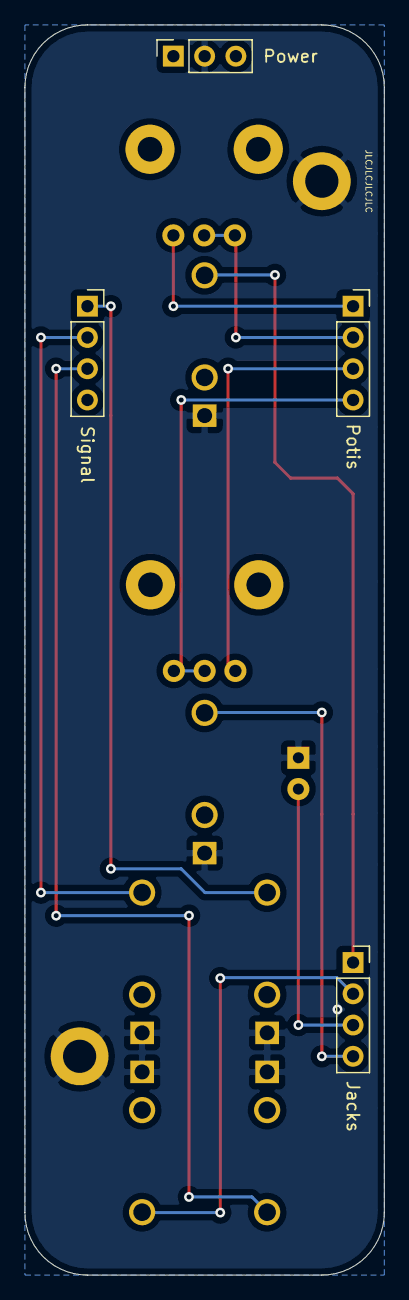
[picture p154: board MFOS Noise Cornucopia Control.kicad_pcb from below]

Board: 2 copper layers, 29.2 x 101.6 mm, 15 parts (4 on the bottom side), 12 nets.

Parts:
D1: LED; LED_D3.0mm
H1, H2: MountingHole_Pad; MountingHole_2.7mm_M2.5_DIN965_Pad
J1: WNS; Jack_3.5mm_QingPu_WQP-PJ398SM_Vertical_CircularHoles
J2: Power; PinSocket_1x03_P2.54mm_Vertical
J3: Signal; PinSocket_1x04_P2.54mm_Vertical
J4: LPNS; Jack_3.5mm_QingPu_WQP-PJ398SM_Vertical_CircularHoles
J5: HPNS; Jack_3.5mm_QingPu_WQP-PJ398SM_Vertical_CircularHoles
J6: Potis; PinSocket_1x04_P2.54mm_Vertical
J7: Jacks; PinSocket_1x04_P2.54mm_Vertical
J8: GNS; Jack_3.5mm_QingPu_WQP-PJ398SM_Vertical_CircularHoles
J9: GHP; Jack_3.5mm_QingPu_WQP-PJ398SM_Vertical_CircularHoles
J10: RNGT; Jack_3.5mm_QingPu_WQP-PJ398SM_Vertical_CircularHoles
R18, R28: B100k; Potentiometer_Alps_RK09K_Single_Vertical

Connections:
GHP: J7.2, J9.T
GND: D1.1, H1.1, H2.1, J1.S, J2.2, J4.S, J5.S, J8.S, J9.S, J10.S
GNS: J7.1, J8.T
GRNS1: J6.1, R18.1
GRNS2: J6.2, R18.2, R18.3
GTF1: J6.3, R28.3
GTF2: J6.4, R28.1, R28.2
HPNS: J3.3, J5.T
LEDA: D1.2, J7.3
LPNS: J3.2, J4.T
RNGT: J7.4, J10.T
WNS: J1.T, J3.1
