mzuelch/CATs-Eurosynth/Modules/MFOS/Dual VCA #2/Electronics/Control/Dual VCA #2 Control.kicad_pcb

## KiCad design Modules/MFOS/Dual VCA #2/Electronics/Control/Dual VCA #2 Control.kicad_pcb (2022-09-25)

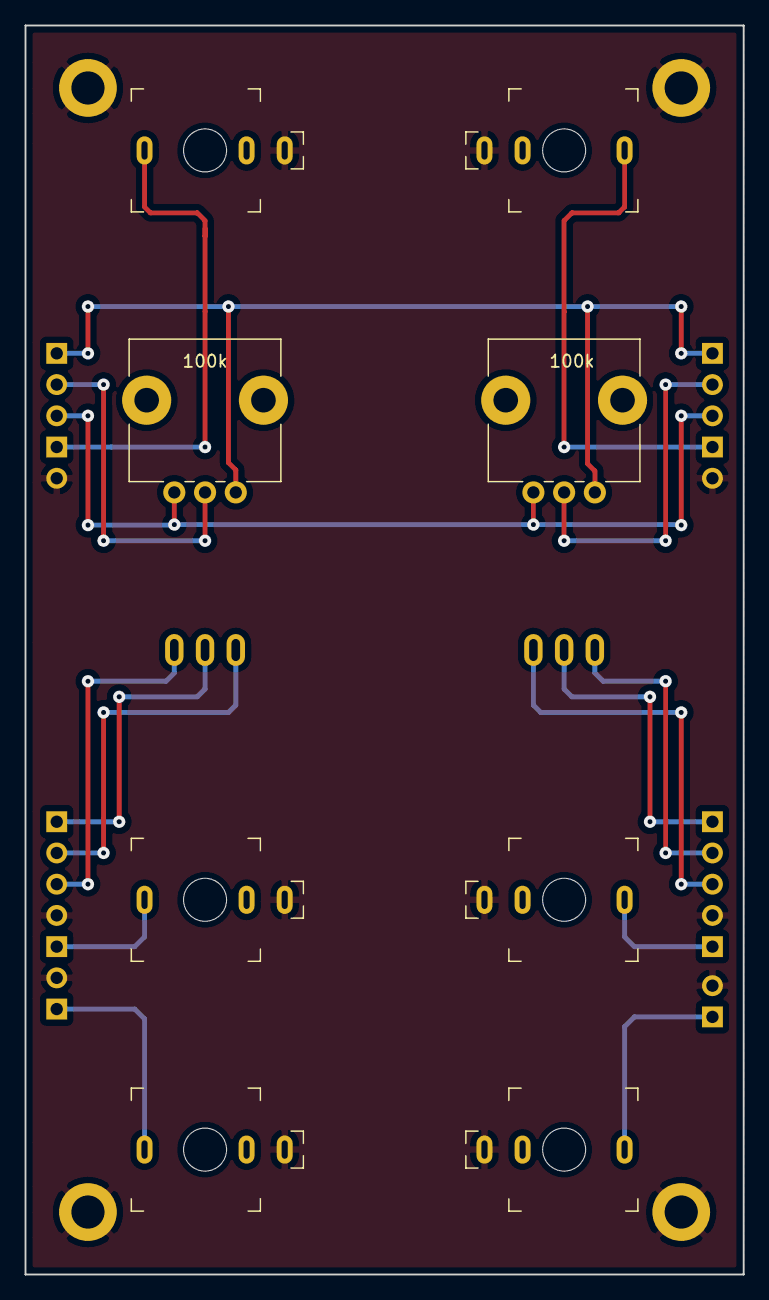
[picture p155: board Dual VCA #2 Control.kicad_pcb from above]

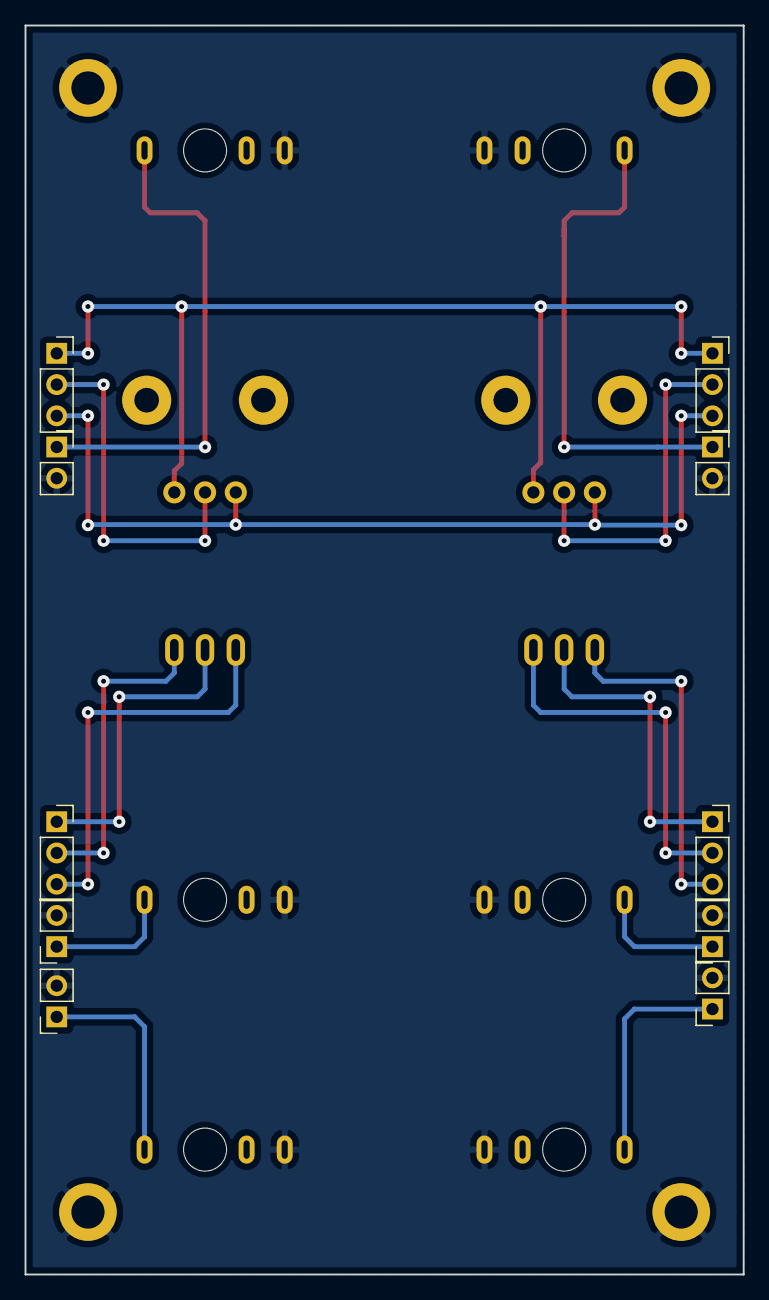
[picture p156: board Dual VCA #2 Control.kicad_pcb from below]

Board: 2 copper layers, 58.4 x 101.6 mm, 24 parts (10 on the bottom side), 17 nets.

Parts:
H1, H2, H3, H4: MH; MountingHole_2.7mm_M2.5_DIN965_Pad
J1: CV In #1; PJ-301-M-12
J2: Sig In #1; PJ-301-M-12
J3: Sig Out #1; PJ-301-M-12
J4: CV In #2; PJ-301-M-12
J5: Sig In #2; PJ-301-M-12
J6: Sig Out #2; PJ-301-M-12
J7: Sig Out #1; PinSocket_1x02_P2.54mm_Vertical
J8: Pot #1; PinSocket_1x03_P2.54mm_Vertical
J9: CV In #1; PinSocket_1x02_P2.54mm_Vertical
J10: Sig In #1; PinSocket_1x02_P2.54mm_Vertical
J11: SW #1; PinSocket_1x03_P2.54mm_Vertical
J12: Sig Out #2; PinSocket_1x02_P2.54mm_Vertical
J13: Pot #2; PinSocket_1x03_P2.54mm_Vertical
J14: CV In #2; PinSocket_1x02_P2.54mm_Vertical
J15: Sig In #2; PinSocket_1x02_P2.54mm_Vertical
J16: SW #2; PinSocket_1x03_P2.54mm_Vertical
R1, R21: 100k; Potentiometer_Alps_RK09L_Single_Vertical
SW1: Log/Lin #1; SMTS-1xx-Solder
SW2: Log/Lin #2; SMTS-1xx-Solder

Connections:
+12V: J8.1, J13.1, R1.1, R21.1
-12V: J8.3, J13.3, R1.3, R21.3
GND: H1.1, H2.1, H3.1, H4.1, J1.S, J2.S, J3.S, J4.S, J5.S, J6.S, J7.2, J9.2, J10.2, J12.2, J14.2, J15.2
unnamed: J1.T, J9.1
unnamed: J3.T, J7.1
unnamed: J8.2, R1.2
unnamed: J2.T, J10.1
unnamed: J11.1, SW1.1
unnamed: J11.2, SW1.2
unnamed: J11.3, SW1.3
unnamed: J6.T, J12.1
unnamed: J13.2, R21.2
unnamed: J4.T, J14.1
unnamed: J5.T, J15.1
unnamed: J16.1, SW2.1
unnamed: J16.2, SW2.2
unnamed: J16.3, SW2.3
