mzuelch/CATs-Eurosynth/Modules/MFOS/Eight Stage Phase Shifter/Electronics/Control/MFOS Eight Stage Phase Shifter - Control.kicad_pcb

## KiCad design Modules/MFOS/Eight Stage Phase Shifter/Electronics/Control/MFOS Eight Stage Phase Shifter - Control.kicad_pcb (2022-09-18)

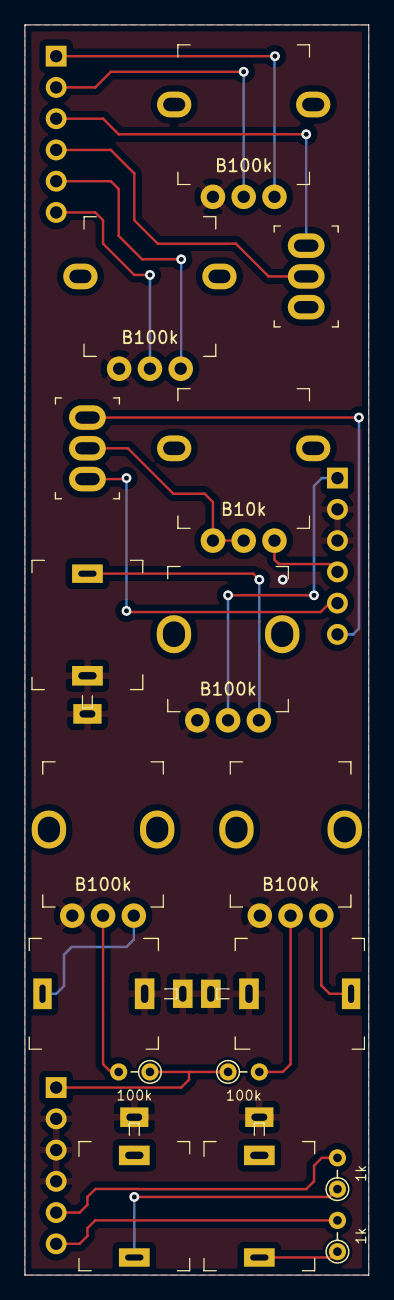
[picture p157: board MFOS Eight Stage Phase Shifter - Control.kicad_pcb from above]

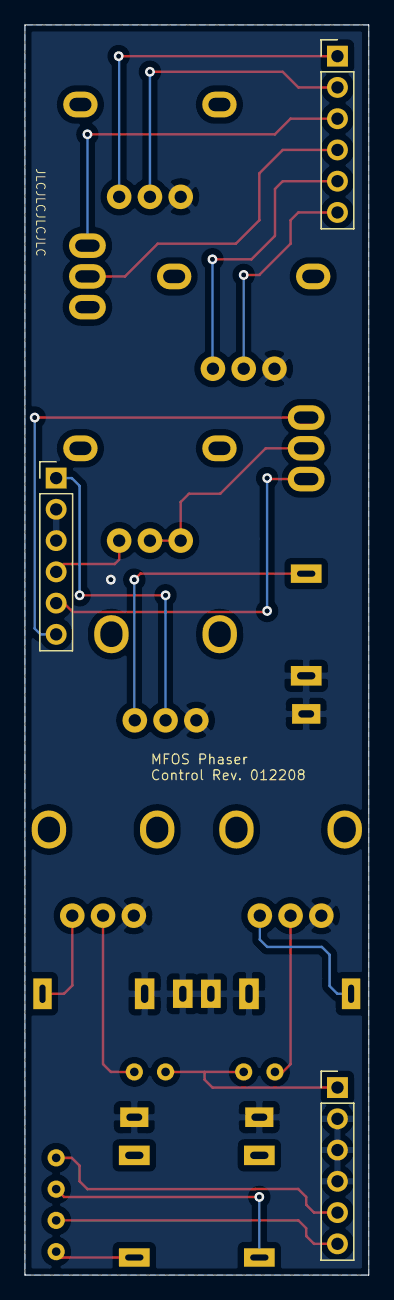
[picture p158: board MFOS Eight Stage Phase Shifter - Control.kicad_pcb from below]

Board: 2 copper layers, 27.9 x 101.6 mm, 20 parts (3 on the bottom side), 22 nets.

Parts:
J1: LFO; PinHeader_1x06_P2.54mm_Vertical
J2: CV_OUT; PinHeader_1x06_P2.54mm_Vertical
J3: In; PinHeader_1x06_P2.54mm_Vertical
J4: CV1; Jack_3.5mm_QingPu_WQP-PJ301M-12
J5: CV2; Jack_3.5mm_QingPu_WQP-PJ301M-12
J6: In; Jack_3.5mm_QingPu_WQP-PJ301M-12
J7: Out1; Jack_3.5mm_QingPu_WQP-PJ301M-12
J8: Out2; Jack_3.5mm_QingPu_WQP-PJ301M-12
P1, P2, P3: B100k; Potentiometer_AlpsAlpine_RK09K1130
P4, P6: B100k; Potentiometer_AlpsAlpine_RK09L1140
P5: B10k; Potentiometer_AlpsAlpine_RK09L1140
R1, R2: 1k; R_Axial_DIN0204_L3.6mm_D1.6mm_P2.54mm_Vertical
R3, R4: 100k; R_Axial_DIN0204_L3.6mm_D1.6mm_P2.54mm_Vertical
SW1: Stages; Switches_SMTS-10x
SW2: Mode; Switches_SMTS-10x

Connections:
CV: J2.1, R3.1, R4.1
Depth_CW: J1.5, P6.CW
Depth_W: J1.6, P6.W
FB: J3.4, P5.CW
GND: J2.2, J2.3, J2.4, J3.2, J3.3, J4.S, J4.TN, J5.S, J5.TN, J6.S, J6.TN, J7.S, J8.S, P1.CCW, P2.CCW, P3.CCW, P4.CCW, P6.CCW
In: J3.1, P3.W
Mode_In: J1.3, SW2.1
Mode_Out: J1.4, SW2.2
unnamed: J4.T, P1.CW
unnamed: J5.T, P2.CW
unnamed: J6.T, P3.CW
unnamed: J7.T, R1.1
unnamed: J8.T, R2.1
unnamed: P1.W, R3.2
unnamed: P2.W, R4.2
unnamed: P5.CCW, P5.W, SW1.2
OUT4: J3.5, SW1.1
OUT8: J3.6, SW1.3
Out1: J2.5, R1.2
Out2: J2.6, R2.2
Rate_CW: J1.1, P4.CW
Rate_W: J1.2, P4.W
