mzuelch/CATs-Eurosynth/Modules/Standard Line/Classic ADSR/Electronics/Main/Classic ADSR Main.kicad_pcb

## KiCad design Modules/Standard Line/Classic ADSR/Electronics/Main/Classic ADSR Main.kicad_pcb (2022-06-25)

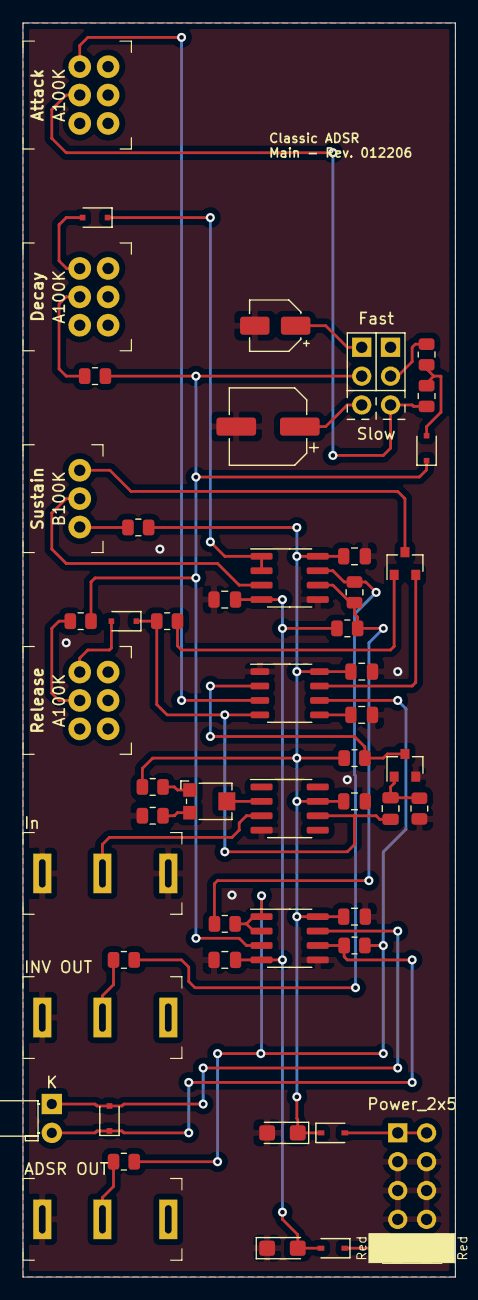
[picture p159: board Classic ADSR Main.kicad_pcb from above]

Board: 2 copper layers, 38.1 x 110.5 mm, 52 parts (0 on the bottom side), 37 nets.

Parts:
C1, C2, C4, C5, C6, C10: 100n; C_0805_2012Metric
C3, C7: 10n; C_0805_2012Metric
C8: 100µ; CP_Elec_6.3x5.4
C9: 10µ; CP_Elec_4x5.4
C11, C12: 10µF; CP_EIA-3216-18_Kemet-A
D1, D2: 1N5819WS; D_SOD-323
D3, D4, D5, D6: 1N4148WS; D_SOD-323F
D7: LED; LED_D3.0mm_Horizontal_O1.27mm_Z6.0mm
J1: In; Jack_3.5mm_QingPu_WQP-PJ323M
J2: Power_2x5; Power_2x5_Vertical
J3: ADSR OUT; Jack_3.5mm_QingPu_WQP-PJ323M
J4: INV OUT; Jack_3.5mm_QingPu_WQP-PJ323M
JP1, JP2: SLOW/FAST; PinHeader_1x03_P2.54mm_Vertical
P1: B100K; Potentiometer_AlpsAlpine_RK0971110
P2, P3, P4: A100K; Potentiometer_AlpsAlpine_RK09712200_Solo
Q1: MMBT3904; SOT-23
Q2: 2N7002; SOT-23
R1: 27k; R_0805_2012Metric
R2: 10k; R_0805_2012Metric
R3, R4: 22k; R_0805_2012Metric
R5: 1M; R_0805_2012Metric
R6: 4.7k; R_0805_2012Metric
R7, R10: 100; R_0805_2012Metric
R8: 680; R_0805_2012Metric
R9: 120; R_0805_2012Metric
R11: 120k; R_0805_2012Metric
R12, R15: 100k; R_0805_2012Metric
R13, R16: 1k; R_0805_2012Metric
R14: 2.4k; R_0805_2012Metric
T1: 20k; Potentiometer_Bourns_TC33X_Vertical
U1: OP07; SOIC-8_3.9x4.9mm_P1.27mm
U2, U3: TL072; SOIC-8_3.9x4.9mm_P1.27mm
U4: ICM7555xB; SOP-8_3.9x4.9mm_P1.27mm

Connections:
+12V: C1.2, C4.2, C6.2, C10.2, C11.1, D1.1, R1.1, R4.1, R6.1, U1.7, U2.8, U3.8, U4.8
-12V: C2.1, C5.1, C12.2, D2.2, R11.2, U2.4, U3.4
GND: C1.1, C2.2, C4.1, C5.2, C6.1, C7.1, C8.2, C9.2, C10.1, C11.2, C12.1, J1.S, J1.TN, J2.GND, J3.S, J4.S, Q1.2, R2.2, R3.2, U1.4, U2.5, U3.5, U4.1
unnamed: C3.1, Q1.1, R3.1
unnamed: C3.2, D4.1, R5.2, U1.6, U4.4
unnamed: C7.2, U4.5
unnamed: C8.1, JP2.3
unnamed: C9.1, JP2.1
unnamed: D1.2, J2.+12V
unnamed: D2.1, J2.-12V
unnamed: D3.1, U2.1, U2.2
unnamed: D3.2, P3.CCW
unnamed: D4.2, P4.CCW
unnamed: D5.1, JP2.2, R7.1, R10.1, U3.3
unnamed: D5.2, R8.1, R9.1
unnamed: D6.1, D7.2, R14.1, U3.6
unnamed: D6.2, D7.1, U3.7
unnamed: J1.T, U1.3
unnamed: J3.T, R13.1
unnamed: J4.T, R16.1
unnamed: JP1.2, R9.2
unnamed: JP1.3, P2.W, R8.2
unnamed: P1.CCW, Q2.3
unnamed: P1.CW, R6.2
unnamed: P1.W, U2.3
unnamed: P2.CCW, U4.3
unnamed: P3.W, R7.2
unnamed: P4.W, R10.2
unnamed: Q1.3, R4.2, U4.2
unnamed: Q2.1, R5.1
unnamed: Q2.2, U4.7
unnamed: R1.2, T1.1
unnamed: R2.1, T1.3
unnamed: R11.1, R12.2, R15.1, U2.6
unnamed: R12.1, R13.2, R14.2, U3.1, U3.2, U4.6
unnamed: R15.2, R16.2, U2.7
unnamed: T1.2, U1.2
