mzuelch/CATs-Eurosynth/Modules/Standard Line/Manual Gate/Electronics/Control/Manual Gate Control.kicad_pcb

## KiCad design Modules/Standard Line/Manual Gate/Electronics/Control/Manual Gate Control.kicad_pcb (2022-06-14)

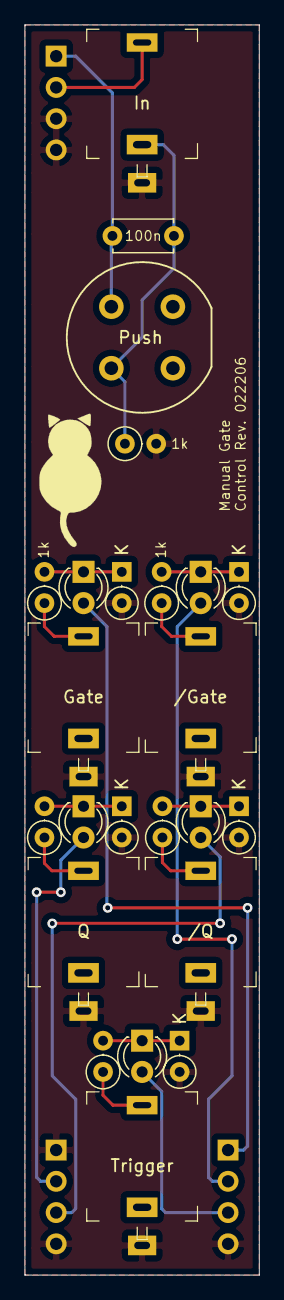
[picture p160: board Manual Gate Control.kicad_pcb from above]

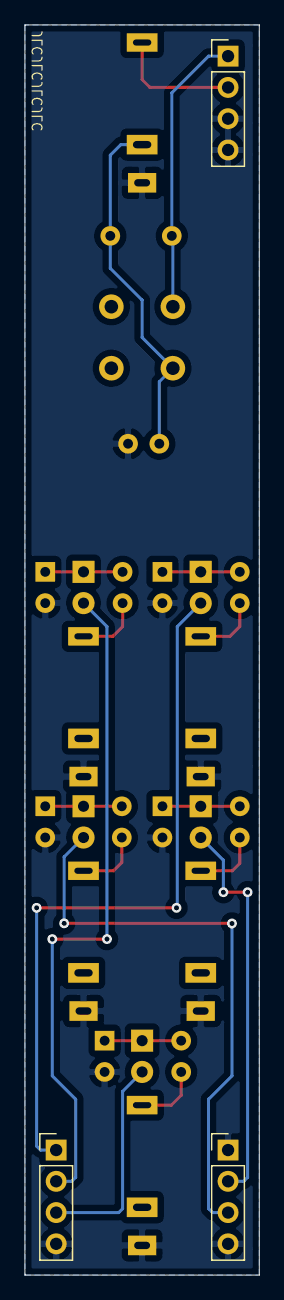
[picture p161: board Manual Gate Control.kicad_pcb from below]

Board: 2 copper layers, 19.1 x 101.6 mm, 27 parts (3 on the bottom side), 19 nets.

Parts:
C1: 100n; C_Disc_D4.7mm_W2.5mm_P5.00mm
D1, D2, D5, D7, D8: 1N4733A; D_DO-35_SOD27_P2.54mm_Vertical_KathodeUp
D3, D4, D6, D10, D11: LED; LED_D3.0mm
J1: Q; Jack_3.5mm_QingPu_WQP-PJ301M-12
J2: Trigger; Jack_3.5mm_QingPu_WQP-PJ301M-12
J4: /Q; Jack_3.5mm_QingPu_WQP-PJ301M-12
J5: Gate; Jack_3.5mm_QingPu_WQP-PJ301M-12
J6: /Gate; Jack_3.5mm_QingPu_WQP-PJ301M-12
J7: In; Jack_3.5mm_QingPu_WQP-PJ301M-12
J8: In; PinHeader_1x04_P2.54mm_Vertical
J9: Q_Qq; PinHeader_1x04_P2.54mm_Vertical
J10: Gate; PinHeader_1x04_P2.54mm_Vertical
R1, R13, R15, R26, R34, R38: 1k; R_Axial_DIN0207_L6.3mm_D2.5mm_P2.54mm_Vertical
SW1: Push; Push_E-Switch_KS01Q01

Connections:
+12V: C1.1, J8.1, SW1.2
GND: D1.2, D2.2, D5.2, D7.2, D8.2, J1.S, J2.S, J4.S, J5.S, J6.S, J7.S, J8.3, J8.4, J9.1, J9.4, J10.4, R1.2
Gate_Pin: D10.2, J10.1
Gateq_Pin: D11.2, J10.2
In_Pin: J7.T, J8.2
unnamed: C1.2, J7.TN, R1.1, SW1.1
unnamed: D1.1, D11.1, R38.2
unnamed: D2.1, D3.1, R13.2
unnamed: D4.1, D8.1, R15.2
unnamed: D5.1, D6.1, R26.2
unnamed: D7.1, D10.1, R34.2
unnamed: J1.T, R13.1
unnamed: J2.T, R15.1
unnamed: J4.T, R26.1
unnamed: J5.T, R34.1
unnamed: J6.T, R38.1
Q_Pin: D3.2, J9.2
Qq_Pin: D6.2, J9.3
Trigger_Pin: D4.2, J10.3
