mzuelch/CATs-Eurosynth/Modules/Standard Line/Manual Gate/Electronics/Main/Manual Gate Main.kicad_pcb

## KiCad design Modules/Standard Line/Manual Gate/Electronics/Main/Manual Gate Main.kicad_pcb (2022-06-14)

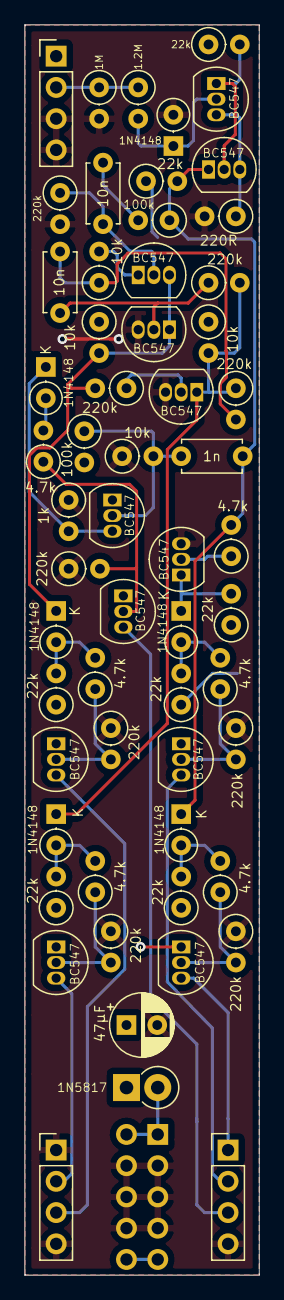
[picture p162: board Manual Gate Main.kicad_pcb from above]

Board: 2 copper layers, 19.1 x 101.6 mm, 59 parts (1 on the bottom side), 35 nets.

Parts:
C2: 1n; C_Disc_D4.7mm_W2.5mm_P5.00mm
C3, C4: 10n; C_Disc_D4.7mm_W2.5mm_P5.00mm
C5: 47µF; CP_Radial_D5.0mm_P2.50mm
D1, D2, D5, D8, D9, D12: 1N4148; D_DO-35_SOD27_P2.54mm_Vertical_KathodeUp
D7: 1N5817; D_DO-41_SOD81_P2.54mm_Vertical_KathodeUp
J3: Power; Power_2x5_Vertical
J8: In; PinHeader_1x04_P2.54mm_Vertical
J9: Q_Qq; PinHeader_1x04_P2.54mm_Vertical
J10: Gate; PinHeader_1x04_P2.54mm_Vertical
Q1, Q2, Q3, Q4, Q5, Q6, Q7, Q8, Q9, Q10, Q11, Q12: BC547; TO-92_Inline
R1, R3: 100k; R_Axial_DIN0207_L6.3mm_D2.5mm_P2.54mm_Vertical
R2, R16, R18, R23: 10k; R_Axial_DIN0207_L6.3mm_D2.5mm_P2.54mm_Vertical
R4: 1k; R_Axial_DIN0207_L6.3mm_D2.5mm_P2.54mm_Vertical
R5, R19, R27, R31, R33, R41, R43: 22k; R_Axial_DIN0207_L6.3mm_D2.5mm_P2.54mm_Vertical
R6, R10, R21, R28, R29, R35: 4.7k; R_Axial_DIN0207_L6.3mm_D2.5mm_P2.54mm_Vertical
R8, R9, R11, R17, R20, R22, R25, R30, R36: 220k; R_Axial_DIN0207_L6.3mm_D2.5mm_P2.54mm_Vertical
R39: 1M; R_Axial_DIN0207_L6.3mm_D2.5mm_P2.54mm_Vertical
R40: 1.2M; R_Axial_DIN0207_L6.3mm_D2.5mm_P2.54mm_Vertical
R42: 220R; R_Axial_DIN0207_L6.3mm_D2.5mm_P2.54mm_Vertical

Connections:
+12V: C5.1, D7.1, J8.1, Q1.1, Q3.1, Q4.1, Q7.1, Q9.1, Q10.1, R1.2, R5.1, R16.1, R19.1, R23.1, R27.1, R31.1, R33.1, R41.1, R43.1
+12VA: D7.2, J3.+12V
GND: C5.2, D12.2, J3.GND, J8.3, J8.4, J9.1, J9.4, J10.4, Q5.3, Q6.3, Q8.3, R2.1, R4.1, R8.2, R9.1, R11.1, R22.1, R30.1, R36.1, R39.2, R42.2
Gate_Pin: J10.1, Q9.3
Gateq_Pin: J10.2, Q10.3
In_Pin: J8.2, R39.1, R40.1
unnamed: C2.1, Q1.2, R1.1, R2.2
unnamed: C3.1, Q2.2, R8.1
unnamed: C3.2, R3.2
unnamed: C4.1, R18.1, R25.2
unnamed: C4.2, Q5.2, R20.1
unnamed: D1.2, R5.2, R6.2
unnamed: D2.1, Q1.3, R4.2
unnamed: D2.2, R10.2
unnamed: D5.2, R19.2, R21.2
unnamed: D8.2, R27.2, R29.2
unnamed: D9.1, Q8.1, R31.2
unnamed: D9.2, R33.2, R35.2
unnamed: D12.1, Q11.2, R40.2
unnamed: Q2.1, R18.2
unnamed: Q3.2, R6.1, R9.2
unnamed: Q4.2, R10.1, R11.2
unnamed: Q6.2, R17.1
unnamed: Q7.2, R21.1, R22.2
unnamed: Q8.2, R28.1
unnamed: Q9.2, R29.1, R30.2
unnamed: Q10.2, R35.1, R36.2
unnamed: Q11.1, Q12.2, R41.2
unnamed: Q11.3, Q12.3, R42.1
Ping: C2.2, D8.1, Q12.1, R3.1, R28.2, R43.2
Q: D1.1, Q6.1, R20.2, R23.2, R25.1
Q_Pin: J9.2, Q3.3
Qq_Pin: J9.3, Q7.3
Qquer: D5.1, Q2.3, Q5.1, R16.2, R17.2
Trigger_Pin: J10.3, Q4.3
