mzuelch/CATs-Eurosynth/Modules/Standard Line/Vactrol VCF/Electronics/Main/Vactrol VCF - Main.kicad_pcb

## KiCad design Modules/Standard Line/Vactrol VCF/Electronics/Main/Vactrol VCF - Main.kicad_pcb (2022-05-20)

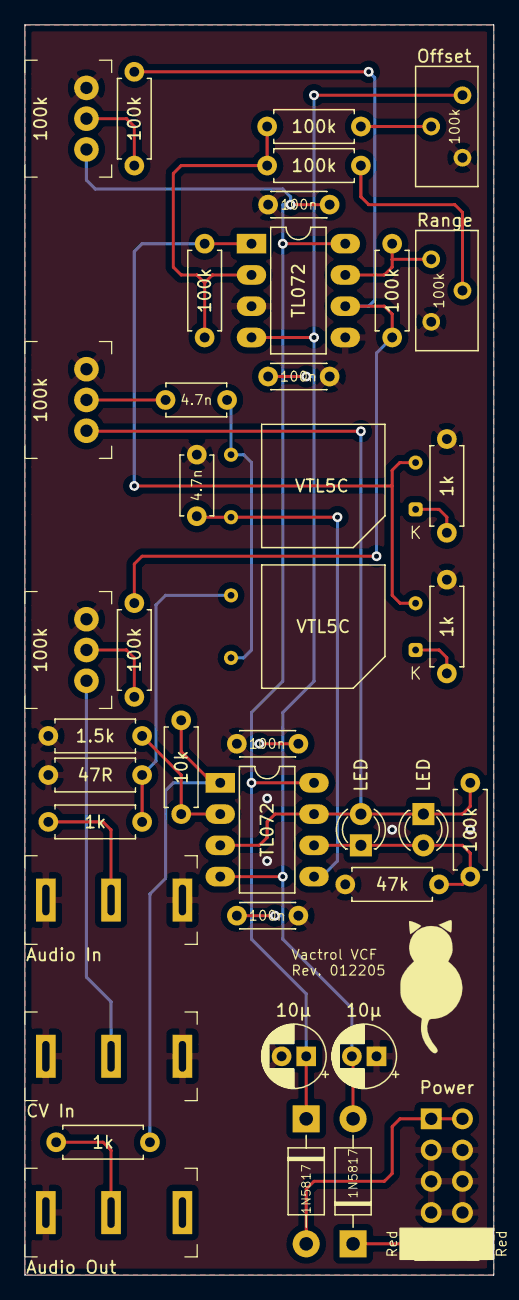
[picture p163: board Vactrol VCF - Main.kicad_pcb from above]

Board: 2 copper layers, 38.1 x 101.6 mm, 40 parts (0 on the bottom side), 26 nets.

Parts:
C1, C2: 4.7n; C_Disc_D4.7mm_W2.5mm_P5.00mm
C3, C4: 10µ; CP_Radial_D5.0mm_P2.00mm
C5, C6, C7, C8: 100n; C_Disc_D4.3mm_W1.9mm_P5.00mm
D1, D2: LED; LED_D3.0mm
D3, D4: 1N5817; D_DO-41_SOD81_P10.16mm_Horizontal
J1: Audio In; Jack_3.5mm_QingPu_WQP-PJ323M
J2: Audio Out; Jack_3.5mm_QingPu_WQP-PJ323M
J3: Power; Power_2x5_Vertical
J4: CV In; Jack_3.5mm_QingPu_WQP-PJ323M
P1, P2, P3: 100k; Potentiometer_AlpsAlpine_RK0971110
R1, R3, R4, R12: 1k; R_Axial_DIN0207_L6.3mm_D2.5mm_P7.62mm_Horizontal
R2: 47R; R_Axial_DIN0207_L6.3mm_D2.5mm_P7.62mm_Horizontal
R5: 47k; R_Axial_DIN0207_L6.3mm_D2.5mm_P7.62mm_Horizontal
R6, R7, R8, R9, R13, R14, R15: 100k; R_Axial_DIN0207_L6.3mm_D2.5mm_P7.62mm_Horizontal
R10: 1.5k; R_Axial_DIN0207_L6.3mm_D2.5mm_P7.62mm_Horizontal
R11: 10k; R_Axial_DIN0207_L6.3mm_D2.5mm_P7.62mm_Horizontal
RV1, RV2: 100k; Potentiometer_Bourns_3296Y_Vertical
U1, U2: VTL5C; PerkinElmer_VTL5C
U3, U4: TL072; DIP-8_W7.62mm_LongPads

Connections:
+12V: C3.1, C5.1, C7.1, D3.1, P2.CW, U3.8, U4.8
-12V: C4.2, C6.2, C8.2, D4.2, RV1.3, U3.4, U4.4
GND: C2.1, C3.2, C4.1, C5.2, C6.1, C7.2, C8.1, J1.S, J1.TN, J2.S, J3.GND, J4.S, J4.TN, P1.CCW, P2.CCW, P3.CCW, R2.2, R3.1, R4.1, R5.1, R10.1, RV1.1, RV2.3, U3.3, U3.5
unnamed: C1.1, P1.W
unnamed: C1.2, U1.3, U2.4
unnamed: C2.2, U2.3, U4.5
unnamed: D1.1, D2.2, R5.2, R7.2, U4.6
unnamed: D1.2, D2.1, P1.CW, R7.1, U4.3, U4.7
unnamed: D3.2, J3.+12V
unnamed: D4.1, J3.-12V
unnamed: J1.T, R1.2
unnamed: J2.T, R12.1
unnamed: J4.T, P3.CW
unnamed: P2.W, R14.1
unnamed: P3.W, R15.1
unnamed: R1.1, R2.1, U1.4
unnamed: R3.2, U1.1
unnamed: R4.2, U2.1
unnamed: R6.1, R8.2, R9.2, U3.2
unnamed: R6.2, U1.2, U2.2, U3.1
unnamed: R8.1, RV1.2
unnamed: R9.1, RV2.2
unnamed: R10.2, R11.2, U4.2
unnamed: R11.1, R12.2, U4.1
unnamed: R13.1, R14.2, R15.2, U3.6
unnamed: R13.2, RV2.1, U3.7
