mzuelch/CATs-Eurosynth/Modules/Standard Line/Envelope Follower/Electronics/Main/Envelope Follower Main.kicad_pcb

## KiCad design Modules/Standard Line/Envelope Follower/Electronics/Main/Envelope Follower Main.kicad_pcb (2022-03-27)

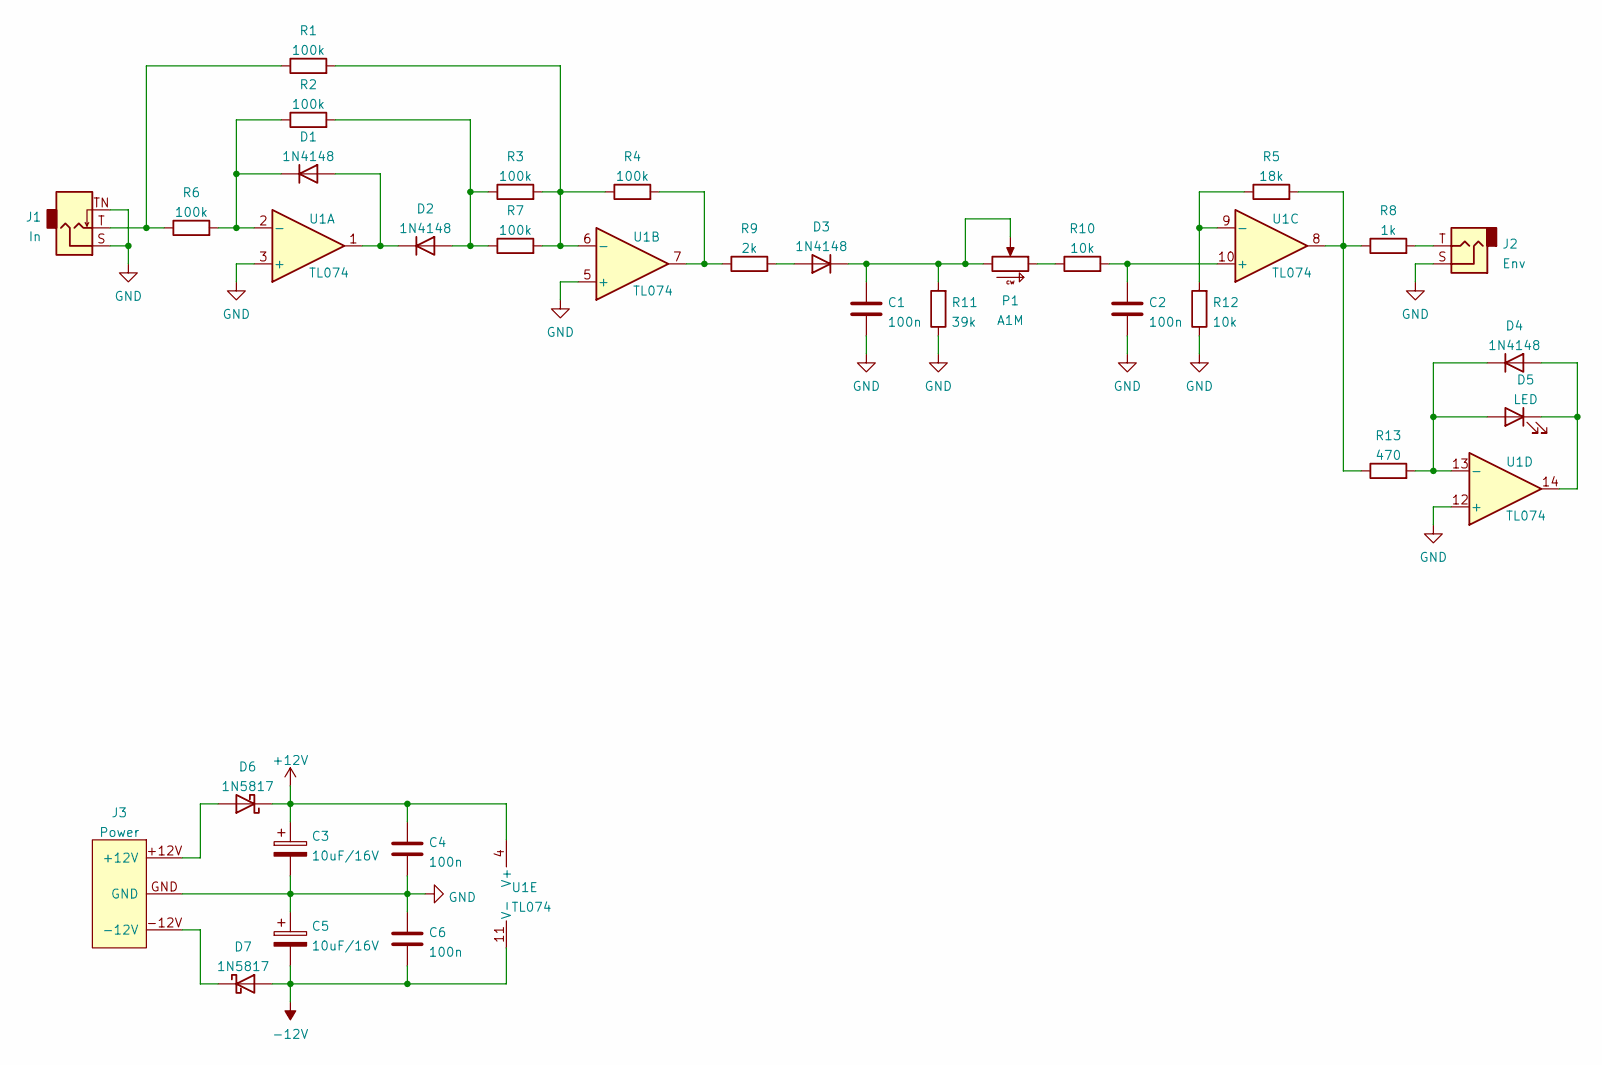
[picture p164: schematic Envelope Follower Main.kicad_sch]

Parts:
C1, C2, C4, C6: 100n; C_Disc_D4.7mm_W2.5mm_P5.00mm
C3, C5: 10uF/16V; CP_Radial_D5.0mm_P2.00mm
D1, D2, D3, D4: 1N4148; D_DO-35_SOD27_P7.62mm_Horizontal
D5: LED; LED_D3.0mm_Horizontal_O1.27mm_Z10.0mm
D6, D7: 1N5817; D_DO-41_SOD81_P10.16mm_Horizontal
J1: In; Jack_3.5mm_QingPu_WQP-PJ323M
J2: Env; Jack_3.5mm_QingPu_WQP-PJ323M
J3: Power; Power_2x5_Vertical
P1: A1M; Potentiometer_AlpsAlpine_RK0971110
R1, R2, R3, R4, R6, R7: 100k; R_Axial_DIN0207_L6.3mm_D2.5mm_P7.62mm_Horizontal
R5: 18k; R_Axial_DIN0207_L6.3mm_D2.5mm_P7.62mm_Horizontal
R8: 1k; R_Axial_DIN0207_L6.3mm_D2.5mm_P7.62mm_Horizontal
R9: 2k; R_Axial_DIN0207_L6.3mm_D2.5mm_P7.62mm_Horizontal
R10, R12: 10k; R_Axial_DIN0207_L6.3mm_D2.5mm_P7.62mm_Horizontal
R11: 39k; R_Axial_DIN0207_L6.3mm_D2.5mm_P7.62mm_Horizontal
R13: 470; R_Axial_DIN0207_L6.3mm_D2.5mm_P7.62mm_Horizontal
U1: TL074; DIP-14_W7.62mm_LongPads

Connections:
+12V: C3.1, C4.1, D6.1 (K), U1.4 (V+)
-12V: C5.2, C6.2, D7.2 (A), U1.11 (V-)
GND: C1.2, C2.2, C3.2, C4.2, C5.1, C6.1, J1.S, J1.TN, J2.S, J3.GND, R11.1, R12.1, U1.3 (+), U1.5 (+), U1.12 (+)
unnamed: C1.1, D3.1 (K), P1.CCW, P1.W, R11.2
unnamed: C2.1, R10.2, U1.10 (+)
unnamed: D1.1 (K), R2.1, R6.2, U1.2 (-)
unnamed: D1.2 (A), D2.1 (K), U1.1
unnamed: D2.2 (A), R2.2, R3.1, R7.1
unnamed: D3.2 (A), R9.2
unnamed: D4.1 (K), D5.2 (A), R13.2, U1.13 (-)
unnamed: D4.2 (A), D5.1 (K), U1.14
unnamed: D6.2 (A), J3.+12V
unnamed: D7.1 (K), J3.-12V
unnamed: J1.T, R1.1, R6.1
unnamed: J2.T, R8.2
unnamed: P1.CW, R10.1
unnamed: R1.2, R3.2, R4.1, R7.2, U1.6 (-)
unnamed: R4.2, R9.1, U1.7
unnamed: R5.1, R12.2, U1.9 (-)
unnamed: R5.2, R8.1, R13.1, U1.8

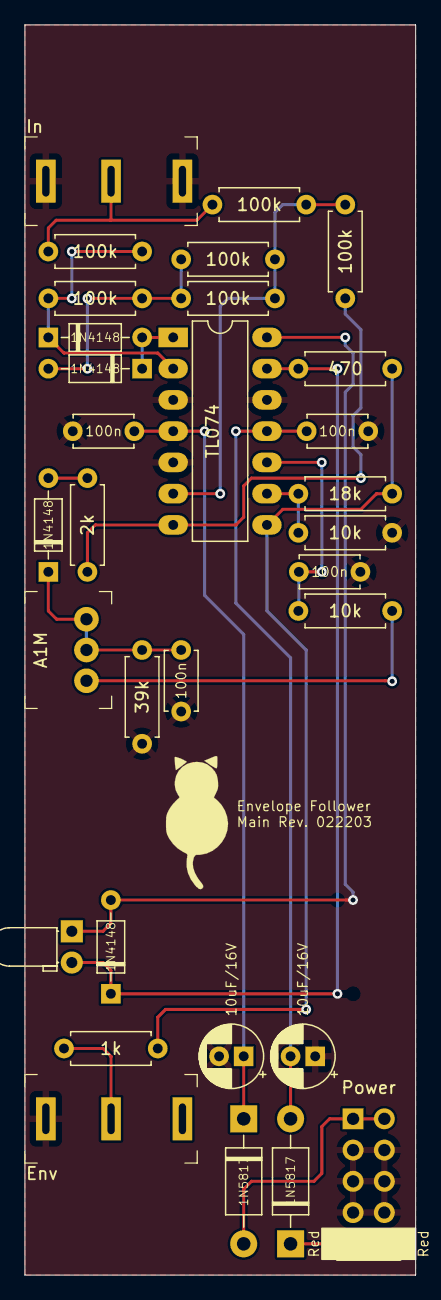
[picture p165: board Envelope Follower Main.kicad_pcb from above]

Board: 2 copper layers, 31.8 x 101.6 mm, 31 parts (0 on the bottom side), 20 nets.
