mzuelch/CATs-Eurosynth/Modules/HAGIWO/VCF Diode Ladder Filter/Electronics/Main/VCF Diode Ladder Filter.kicad_pcb

## KiCad design Modules/HAGIWO/VCF Diode Ladder Filter/Electronics/Main/VCF Diode Ladder Filter.kicad_pcb (2022-03-19)

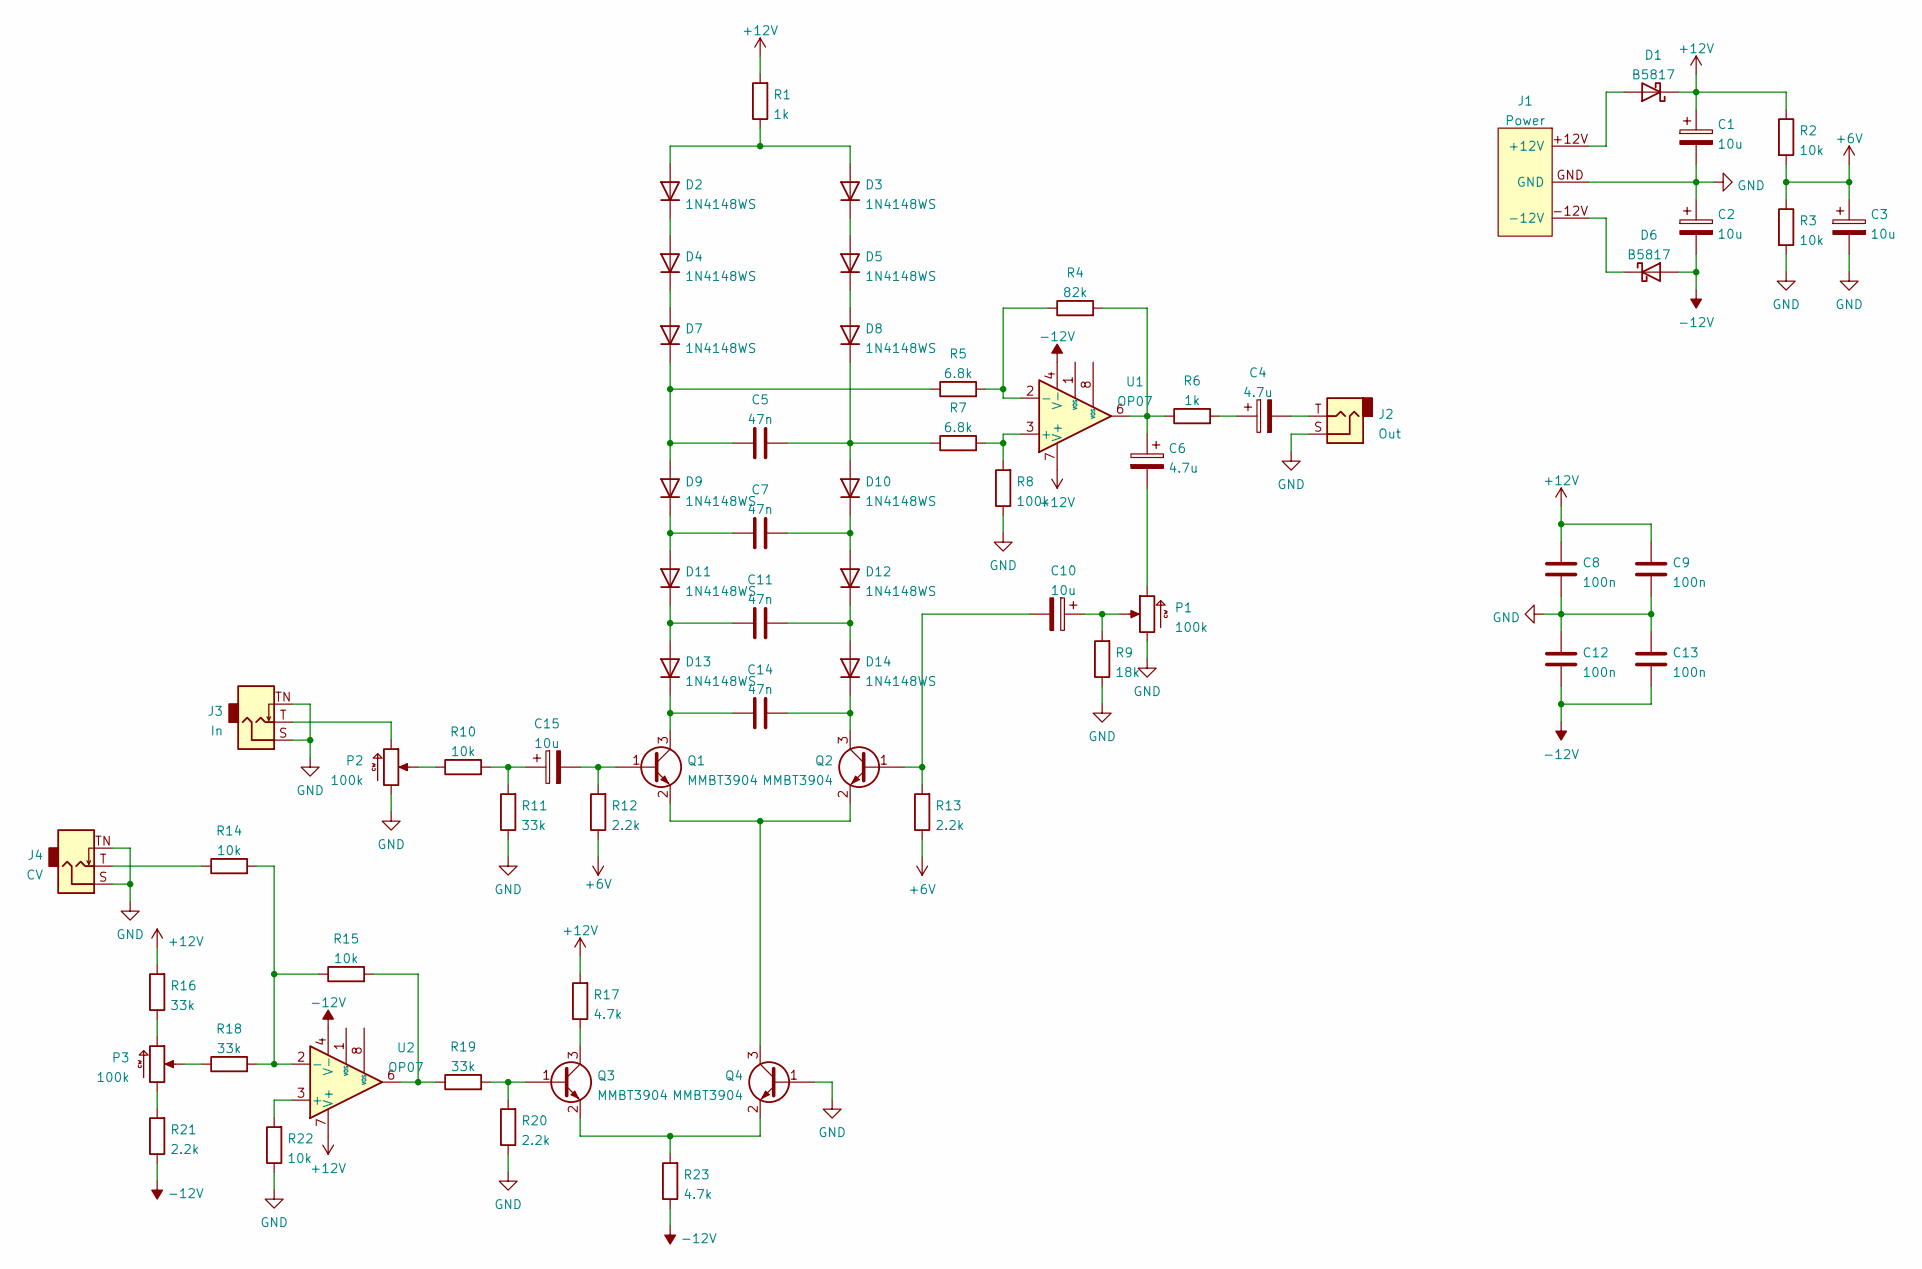
[picture p166: schematic VCF Diode Ladder Filter.kicad_sch]

Parts:
C1, C2, C3, C10, C15: 10u; CP_Elec_4x5.4; LCSC C72485
C4, C6: 4.7u; CP_Elec_6.3x5.4; LCSC C90266
C5, C7, C11, C14: 47n; C_1206_3216Metric; LCSC C21812
C8, C9, C12, C13: 100n; C_0402_1005Metric; LCSC C307331
D1, D6: B5817; D_SOD-323; LCSC C122854
D2, D3, D4, D5, D7, D8, D9, D10, D11, D12, D13, D14: 1N4148WS; D_SOD-323; LCSC C2128
J1: Power; Power_2x5_Vertical
J2: Out; Jack_3.5mm_QingPu_WQP-PJ301M-12
J3: In; Jack_3.5mm_QingPu_WQP-PJ301M-12
J4: CV; Jack_3.5mm_QingPu_WQP-PJ301M-12
P1, P3: 100k; Potentiometer_AlpsAlpine_RK09L1140
P2: 100k; Potentiometer_AlpsAlpine_RK09K1130
Q1, Q2, Q3, Q4: MMBT3904; SOT-23; LCSC C20526
R1, R6: 1k; R_0402_1005Metric; LCSC C25905
R2, R3, R10, R14, R15, R22: 10k; R_0402_1005Metric; LCSC C25744
R4: 82k; R_0402_1005Metric; LCSC C4142
R5, R7: 6.8k; R_0402_1005Metric; LCSC C25917
R8: 100k; R_0402_1005Metric; LCSC C25741
R9: 18k; R_0402_1005Metric; LCSC C25762
R11, R16, R18, R19: 33k; R_0402_1005Metric; LCSC C25779
R12, R13, R20, R21: 2.2k; R_0402_1005Metric; LCSC C25879
R17, R23: 4.7k; R_0402_1005Metric; LCSC C25900
U1, U2: OP07; SOIC-8_3.9x4.9mm_P1.27mm; LCSC C7433

Connections:
+6V: C3.1, R2.2, R3.1, R12.1, R13.1
+12V: C1.1, C8.1, C9.1, D1.1 (K), R1.2, R2.1, R16.2, R17.2, U1.7 (V+), U2.7 (V+)
-12V: C2.2, C12.2, C13.2, D6.2 (A), R21.1, R23.1, U1.4 (V-), U2.4 (V-)
GND: C1.2, C2.1, C3.2, C8.2, C9.2, C12.1, C13.1, J1.GND, J2.S, J3.S, J3.TN, J4.S, J4.TN, P1.CCW, P2.CCW, Q4.1 (B), R3.2, R8.1, R9.1, R11.1, R20.1, R22.1
unnamed: C4.1, R6.2
unnamed: C4.2, J2.T
unnamed: C5.1, D7.1 (K), D9.2 (A), R5.1
unnamed: C5.2, D8.1 (K), D10.2 (A), R7.1
unnamed: C6.1, R4.2, R6.1, U1.6
unnamed: C6.2, P1.CW
unnamed: C7.1, D9.1 (K), D11.2 (A)
unnamed: C7.2, D10.1 (K), D12.2 (A)
unnamed: C10.1, P1.W, R9.2
unnamed: C10.2, Q2.1 (B), R13.2
unnamed: C11.1, D11.1 (K), D13.2 (A)
unnamed: C11.2, D12.1 (K), D14.2 (A)
unnamed: C14.1, D13.1 (K), Q1.3 (C)
unnamed: C14.2, D14.1 (K), Q2.3 (C)
unnamed: C15.1, R10.2, R11.2
unnamed: C15.2, Q1.1 (B), R12.2
unnamed: D1.2 (A), J1.+12V
unnamed: D2.1 (K), D4.2 (A)
unnamed: D2.2 (A), D3.2 (A), R1.1
unnamed: D3.1 (K), D5.2 (A)
unnamed: D4.1 (K), D7.2 (A)
unnamed: D5.1 (K), D8.2 (A)
unnamed: D6.1 (K), J1.-12V
unnamed: J3.T, P2.CW
unnamed: J4.T, R14.1
unnamed: P2.W, R10.1
unnamed: P3.CCW, R21.2
unnamed: P3.CW, R16.1
unnamed: P3.W, R18.1
unnamed: Q1.2 (E), Q2.2 (E), Q4.3 (C)
unnamed: Q3.1 (B), R19.2, R20.2
unnamed: Q3.2 (E), Q4.2 (E), R23.2
unnamed: Q3.3 (C), R17.1
unnamed: R4.1, R5.2, U1.2 (-)
unnamed: R7.2, R8.2, U1.3 (+)
unnamed: R14.2, R15.1, R18.2, U2.2 (-)
unnamed: R15.2, R19.1, U2.6
unnamed: R22.2, U2.3 (+)

Board: 2 copper layers, 65 parts (59 on the bottom side), 42 nets, no tracks yet.
