mzuelch/CATs-Eurosynth/Modules/Standard Line/Atari Punk Console/Electronics/Main/APC Eurorack Main.sch

## KiCad design Modules/Standard Line/Atari Punk Console/Electronics/Main/APC Eurorack Main.sch (2021-06-12)

Schematic: APC Eurorack Main.sch

Parts:
C1: 10nF; C_Rect_L7.0mm_W2.0mm_P5.00mm
C2, C4: 100nF; C_Rect_L7.0mm_W2.0mm_P5.00mm
C3, C5: 10uF/50V; CP_Radial_D5.0mm_P2.00mm
D1, D2, D3: 1N5817; D_DO-41_SOD81_P10.16mm_Horizontal
IC1: L78L05_TO92; TO-92_Inline
IC2: LM556; DIP-14_W7.62mm_Socket_LongPads
J1: Power; IDC-Header_2x08_P2.54mm_Vertical
J4: Out; PJ-323
J5: CV2; PJ-323
J6: CV1; PJ-323
R1, R7, R8, R9: 1k; R_Axial_DIN0207_L6.3mm_D2.5mm_P7.62mm_Horizontal
R2: 1R0; R_Axial_DIN0207_L6.3mm_D2.5mm_P7.62mm_Horizontal
R3: 100k; R_Axial_DIN0207_L6.3mm_D2.5mm_P7.62mm_Horizontal
R4: 2k; R_Axial_DIN0207_L6.3mm_D2.5mm_P7.62mm_Horizontal
R10, R11: 500kB; Potentiometer_Alps_RK097_Single_Horizontal
