mzuelch/CATs-Eurosynth/Modules/Standard Line/Baby8 Sequencer/Electronics/Main/Baby 8.sch

## KiCad design Modules/Standard Line/Baby8 Sequencer/Electronics/Main/Baby 8.sch (2021-06-12)

Schematic: Baby 8.sch

Parts:
C1, C2, C3, C4, C5, C6, C7: 100nF; C_Rect_L7.0mm_W2.0mm_P5.00mm
C8, C9: 10µF/50V; CP_Radial_D5.0mm_P2.50mm
D1, D2, D3, D4, D5, D6, D7, D8: 1N4148; D_DO-35_SOD27_P2.54mm_Vertical_KathodeUp
D9, D10, D11, D12, D13, D14, D15, D16: LED; LED_D3.0mm
J1: Power; IDC-Header_2x08_P2.54mm_Vertical
J2: CV Out; PJ-301-M-12
J3: CLK In; PJ-301-M-12
J4: Reset; PJ-301-M-12
J5: Gate 1; PJ-301-M-12
J6: Gate 2; PJ-301-M-12
J7: Gate 3; PJ-301-M-12
J8: Gate 4; PJ-301-M-12
J9: Gate 5; PJ-301-M-12
J10: Gate 6; PJ-301-M-12
J11: Gate 7; PJ-301-M-12
J12: Gate 8; PJ-301-M-12
R1, R2: 100k; R_Axial_DIN0207_L6.3mm_D2.5mm_P7.62mm_Horizontal
R3, R4, R5, R6, R7, R8, R9, R10: 120R; R_Axial_DIN0207_L6.3mm_D2.5mm_P2.54mm_Vertical
RV1, RV2, RV3, RV4, RV5, RV6, RV7, RV8: 500kB; Potentiometer_Alpha_RD901F-40-00D_Single_Vertical
SW1: Hold; SMTS-1xx-Solder
SW2: Hold; SW_PUSH_6mm_H13mm
SW3: Step; SW_PUSH_6mm_H13mm
U1: 4093; DIP-14_W7.62mm_Socket_LongPads
U2: 4030; DIP-14_W7.62mm_Socket_LongPads
U3: 4017; DIP-16_W7.62mm_Socket_LongPads
U4: LM7809_TO220; TO-220-3_Vertical
