mzuelch/CATs-Eurosynth/Modules/Standard Line/Clock Divider/Electronics/Control/Clock Divider Control.sch

## KiCad design Modules/Standard Line/Clock Divider/Electronics/Control/Clock Divider Control.sch (2021-06-12)

Schematic: Clock Divider Control.sch

Parts:
D1, D2: 1N4148; D_DO-35_SOD27_P7.62mm_Horizontal
D4, D5, D6, D7, D8, D9: LED; LED_D3.0mm
H1, H2: MountingHole_Pad; MountingHole_2.7mm_M2.5_DIN965_Pad
J1: CLK In; PJ-301-M-12
J2: RESET In; PJ-301-M-12
J3: Input; PinSocket_1x08_P2.54mm_Vertical
J4: CLK/2; PJ-301-M-12
J5: CLK/4; PJ-301-M-12
J6: CLK/8; PJ-301-M-12
J7: CLK/16; PJ-301-M-12
J8: CLK/32; PJ-301-M-12
J9: CLK Out; PJ-301-M-12
J10: Output; PinSocket_1x08_P2.54mm_Vertical
R3, R4: 47k; R_Axial_DIN0207_L6.3mm_D2.5mm_P7.62mm_Horizontal
R17, R19, R21, R23, R25, R28: 1k; R_Axial_DIN0207_L6.3mm_D2.5mm_P7.62mm_Horizontal
R18, R20, R22, R24, R26, R29: 470; R_Axial_DIN0207_L6.3mm_D2.5mm_P7.62mm_Horizontal
