mzuelch/CATs-Eurosynth/Modules/Standard Line/Clock Divider/Electronics/Main/Clock Divider Main.sch

## KiCad design Modules/Standard Line/Clock Divider/Electronics/Main/Clock Divider Main.sch (2021-06-12)

Schematic: Clock Divider Main.sch

Parts:
C1: 1µF; C_Disc_D6.0mm_W2.5mm_P5.00mm
C2: 100nF; C_Disc_D5.0mm_W2.5mm_P5.00mm
C3, C5: 10µF; CP_Radial_D5.0mm_P2.50mm
D3: 1N4148; D_DO-35_SOD27_P7.62mm_Horizontal
H1, H2: MountingHole_Pad; MountingHole_2.7mm_M2.5_DIN965_Pad
J1: Input; PinHeader_1x08_P2.54mm_Vertical
J2: Output; PinHeader_1x08_P2.54mm_Vertical
J3: Power; IDC-Header_2x08_P2.54mm_Vertical
Q1, Q2, Q3, Q4, Q5, Q6, Q7, Q8, Q9, Q10, Q11: BC550; TO-92_Inline
R1, R2, R5, R6, R7, R9: 10k; R_Axial_DIN0207_L6.3mm_D2.5mm_P7.62mm_Horizontal
R8: 47k; R_Axial_DIN0207_L6.3mm_D2.5mm_P7.62mm_Horizontal
R10, R11, R12, R13, R14, R15, R16, R27: 100k; R_Axial_DIN0207_L6.3mm_D2.5mm_P7.62mm_Horizontal
U1: 74HC4024; DIP-14_W7.62mm_LongPads
