mzuelch/CATs-Eurosynth/Modules/Standard Line/Power Module/Electronics/Main/Power Modul Main.sch

## KiCad design Modules/Standard Line/Power Module/Electronics/Main/Power Modul Main.sch (2021-09-05)

Schematic: Power Modul Main.sch

Parts:
D1: +12V; LED_D3.0mm
D2: +5V; LED_D3.0mm
D3: -12V; LED_D3.0mm
H1, H2, H3, H4: MountingHole_Pad; MountingHole_2.7mm
J1, J5, J9: +12V; 03866b.68_6.3mm_FASTON
J2, J6, J10: +5V; 03866b.68_6.3mm_FASTON
J3, J7, J11: GND; 03866b.68_6.3mm_FASTON
J4, J8, J12: -12V; 03866b.68_6.3mm_FASTON
R1, R3: 1k; R_Axial_DIN0207_L6.3mm_D2.5mm_P7.62mm_Horizontal
R2: 200R; R_Axial_DIN0207_L6.3mm_D2.5mm_P7.62mm_Horizontal
