mzuelch/CATs-Eurosynth/Modules/YuSynth/Balanced Modulator/Electronics/Main/YuSynth Dual Balanced Modulator Main.sch

## KiCad design Modules/YuSynth/Balanced Modulator/Electronics/Main/YuSynth Dual Balanced Modulator Main.sch (2022-02-10)

Schematic: YuSynth Dual Balanced Modulator Main.sch

Parts:
C1: 100µF/16V; CP_Radial_D6.3mm_P2.50mm
C2, C3: 10µF/16V; CP_Radial_D5.0mm_P2.50mm
C4, C5: 100n; C_Disc_D4.7mm_W2.5mm_P5.00mm
D1, D2: 1N5817; D_DO-41_SOD81_P10.16mm_Horizontal
J1: Power; Power_2x8_Horizontal
J2: A; Jack_3.5mm_QingPu_WQP-PJ324M
J3: B; Jack_3.5mm_QingPu_WQP-PJ324M
J4: AxB; Jack_3.5mm_QingPu_WQP-PJ324M
R1, R2: 1k5; R_Axial_DIN0207_L6.3mm_D2.5mm_P7.62mm_Horizontal
R3, R4: 180k; R_Axial_DIN0207_L6.3mm_D2.5mm_P7.62mm_Horizontal
R5, R7, R8, R12: 2k7; R_Axial_DIN0207_L6.3mm_D2.5mm_P7.62mm_Horizontal
R6, R10, R14: 6k8; R_Axial_DIN0207_L6.3mm_D2.5mm_P7.62mm_Horizontal
R9, R11: 12k; R_Axial_DIN0207_L6.3mm_D2.5mm_P7.62mm_Horizontal
R13, R15: 1k2; R_Axial_DIN0207_L6.3mm_D2.5mm_P7.62mm_Horizontal
R16, R17, R18, R19: 15k; R_Axial_DIN0207_L6.3mm_D2.5mm_P7.62mm_Horizontal
R20: 10k; R_Axial_DIN0207_L6.3mm_D2.5mm_P7.62mm_Horizontal
R21: 68k; R_Axial_DIN0207_L6.3mm_D2.5mm_P7.62mm_Horizontal
R22: 470R; R_Axial_DIN0207_L6.3mm_D2.5mm_P7.62mm_Horizontal
RV1: 200R; Potentiometer_Runtron_RM-065_Vertical
RV2: 500R; Potentiometer_Runtron_RM-065_Vertical
U1: MC1496; SOIC-14_3.9x8.7mm_P1.27mm
U2: TL072; DIP-8_W7.62mm_LongPads
