mzuelch/CATs-Eurosynth/Modules/YuSynth/Improved Steiner VCF/Electronics/Control/YuSynth Improved Steiner VCF Control.sch

## KiCad design Modules/YuSynth/Improved Steiner VCF/Electronics/Control/YuSynth Improved Steiner VCF Control.sch (2022-02-04)

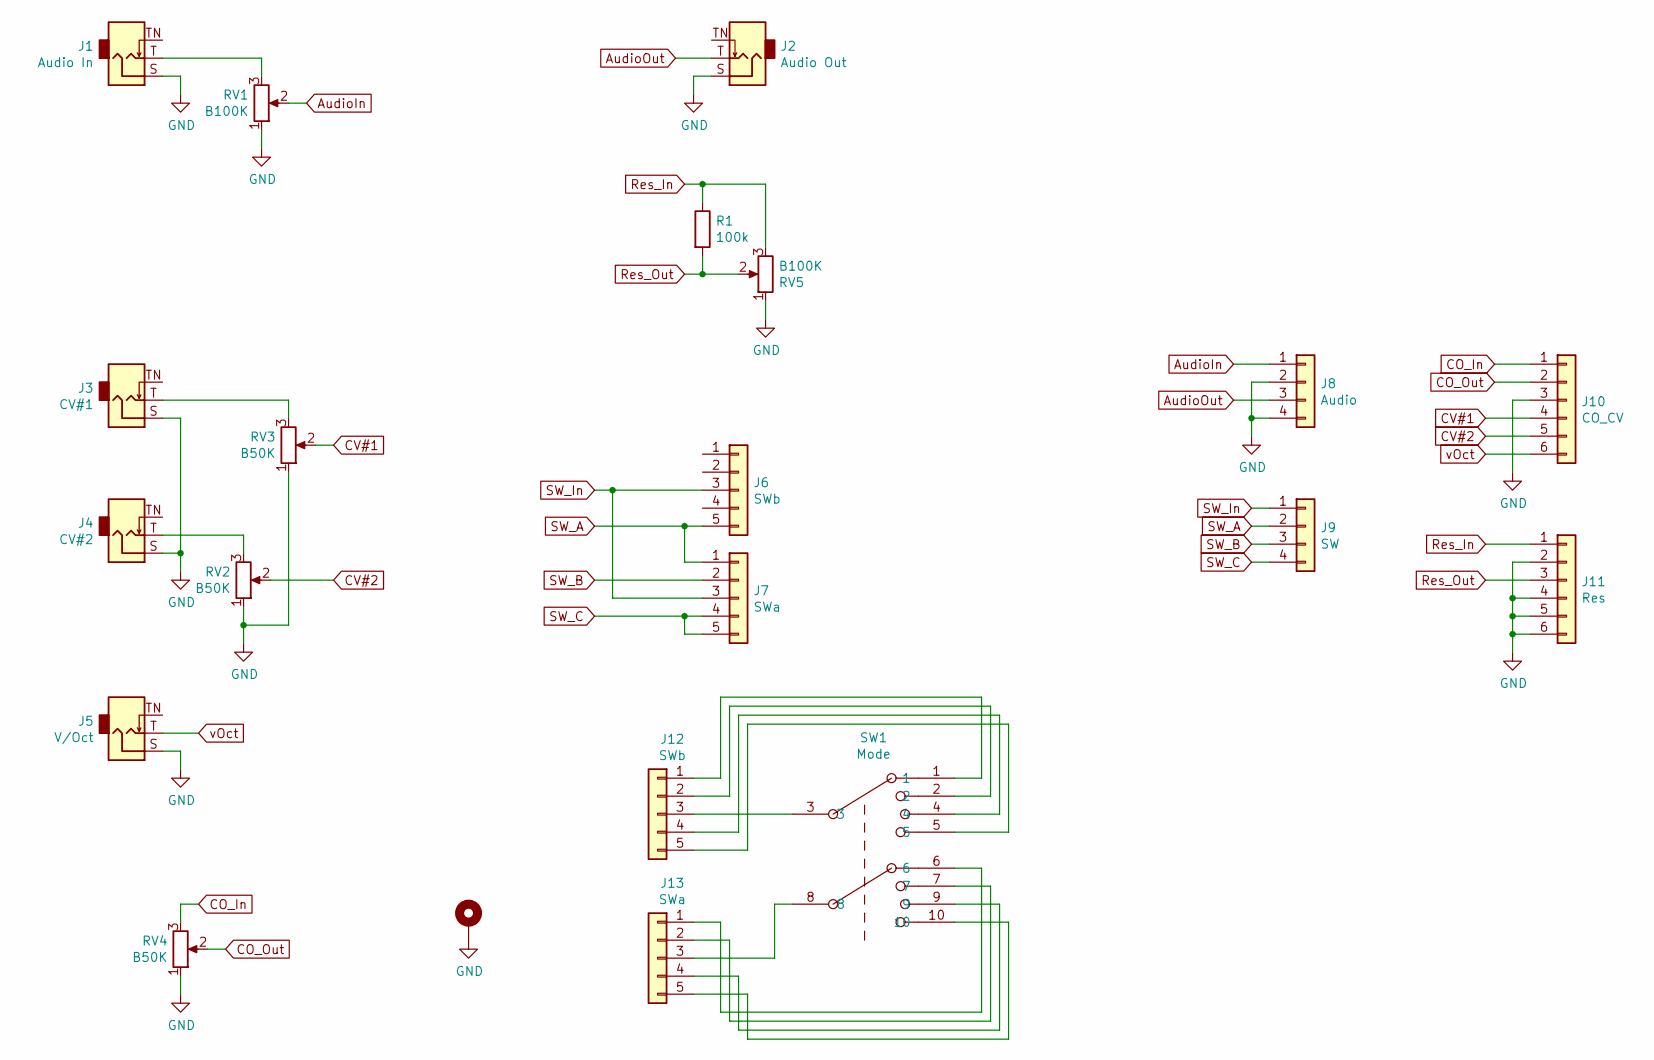
[picture p167: schematic YuSynth Improved Steiner VCF Control.sch]

Parts:
H1: MountingHole_Pad; MountingHole_2.7mm_M2.5_DIN965_Pad
J1: Audio In; Jack_3.5mm_QingPu_WQP-PJ301M-12
J2: Audio Out; Jack_3.5mm_QingPu_WQP-PJ301M-12
J3: CV#1; Jack_3.5mm_QingPu_WQP-PJ301M-12
J4: CV#2; Jack_3.5mm_QingPu_WQP-PJ301M-12
J5: V/Oct; Jack_3.5mm_QingPu_WQP-PJ301M-12
J6, J12: SWb; PinHeader_1x05_P2.54mm_Vertical
J7, J13: SWa; PinHeader_1x05_P2.54mm_Vertical
J8: Audio; PinHeader_1x04_P2.54mm_Vertical
J9: SW; PinHeader_1x04_P2.54mm_Vertical
J10: CO_CV; PinHeader_1x06_P2.54mm_Vertical
J11: Res; PinHeader_1x06_P2.54mm_Vertical
R1: 100k; R_Axial_DIN0207_L6.3mm_D2.5mm_P7.62mm_Horizontal
RV1, RV5: B100K; Potentiometer_AlpsAlpine_RK09K1130
RV2, RV3, RV4: B50K; Potentiometer_AlpsAlpine_RK09K1130
SW1: Mode; SS24E01-G5

Connections:
AudioIn: J8.1, RV1.2
AudioOut: J2.T, J8.3
CO_In: J10.1, RV4.3
CO_Out: J10.2, RV4.2
CV#1: J10.4, RV3.2
CV#2: J10.5, RV2.2
GND: H1.1, J1.S, J2.S, J3.S, J4.S, J5.S, J8.2, J8.4, J10.3, J11.2, J11.4, J11.5, J11.6, RV1.1, RV2.1, RV3.1, RV4.1, RV5.1
unnamed: J1.T, RV1.3
unnamed: J3.T, RV3.3
unnamed: J4.T, RV2.3
unnamed: J12.1, SW1.1
unnamed: J12.2, SW1.2
unnamed: J12.3, SW1.3
unnamed: J12.4, SW1.4
unnamed: J12.5, SW1.5
unnamed: J13.1, SW1.6
unnamed: J13.2, SW1.7
unnamed: J13.3, SW1.8
unnamed: J13.4, SW1.9
unnamed: J13.5, SW1.10
Res_In: J11.1, R1.1, RV5.3
Res_Out: J11.3, R1.2, RV5.2
SW_A: J6.5, J7.1, J9.2
SW_B: J7.2, J9.3
SW_C: J7.4, J7.5, J9.4
SW_In: J6.3, J7.3, J9.1
vOct: J5.T, J10.6
