mzuelch/CATs-Eurosynth/Modules/YuSynth/Improved Steiner VCF/Electronics/Main/YuSynth Improved Steiner VCF Main.sch

## KiCad design Modules/YuSynth/Improved Steiner VCF/Electronics/Main/YuSynth Improved Steiner VCF Main.sch (2021-06-17)

Schematic: YuSynth Improved Steiner VCF Main.sch

Parts:
C1, C11, C12, C13: 10uF; C_0805_2012Metric; JLCPCB C15850
C2, C3: 2.2uF; C_0805_2012Metric; JLCPCB C49217
C4, C6, C8: 1.5n; C_0603_1608Metric; JLCPCB C1595
C5, C7, C10: 47µF; CP_Radial_D5.0mm_P2.50mm
C9: 680n; C_Disc_D4.7mm_W2.5mm_P5.00mm
C14, C15, C16, C17: 100n; C_0805_2012Metric; JLCPCB C49678
D1, D2, D3, D4, D5, D6, D7, D8, D9, D10: 1N4148WS; D_SOD-323; JLCPCB C2128
D11, D12: B5819W; D_SOD-123; JLCPCB C8598
H1: MountingHole_Pad; MountingHole_2.7mm_M2.5_DIN965_Pad
J1: Power; PinHeader_2x05_P2.54mm_Vertical
J8: Audio; PinHeader_1x04_P2.54mm_Vertical
J9: SW; PinHeader_1x04_P2.54mm_Vertical
J10: CO_CV; PinHeader_1x06_P2.54mm_Vertical
J11: Res; PinHeader_1x06_P2.54mm_Vertical
Q1: BC847BDW1; SOT-363_SC-70-6; JLCPCB C82368
R1, R2, R24: 10k; R_0805_2012Metric; JLCPCB C17414
R3, R6, R21: 47k; R_0805_2012Metric; JLCPCB C17713
R4, R5, R8, R25, R27: 220k; R_0805_2012Metric; JLCPCB C17556
R7: 150k; R_0805_2012Metric; JLCPCB C17470
R9, R10: 180k; R_0805_2012Metric; JLCPCB C17501
R11, R18: 1.8k; R_0805_2012Metric; JLCPCB C17398
R12: 220R; R_0805_2012Metric; JLCPCB C17557
R13: 390; R_0805_2012Metric; JLCPCB C17655
R14, R15, R23, R28: 1k; R_0805_2012Metric; JLCPCB C17513
R16, R22: 3.9k; R_0805_2012Metric; JLCPCB C17614
R17: 82R; R_0805_2012Metric; JLCPCB C17841
R19: 2.2M; R_0805_2012Metric; JLCPCB C26113
R20: 22k; R_0805_2012Metric; JLCPCB C17560
R26: 1M; R_0805_2012Metric; JLCPCB C17514
RV1: 2k; Potentiometer_Bourns_3006P_Horizontal
RV2: 1k; Potentiometer_Bourns_3006P_Horizontal
U1, U2: TL072; SO-8_3.9x4.9mm_P1.27mm; JLCPCB C6961
