mzuelch/CATs-Eurosynth/Modules/HAGIWO/Arduino VCO/Firmware/Originals/HAGIWO_Additive_VCO/HAGIWO_Additive_VCO.ino

#include <MozziGuts.h>
#include <Oscil.h> // oscillator template
#include <RollingAverage.h>
#include <tables/sin2048_int8.h> // sine table for oscillator

Oscil <SIN2048_NUM_CELLS, AUDIO_RATE> aSin1(SIN2048_DATA);
Oscil <SIN2048_NUM_CELLS, AUDIO_RATE> aSin2(SIN2048_DATA);
Oscil <SIN2048_NUM_CELLS, AUDIO_RATE> aSin3(SIN2048_DATA);
Oscil <SIN2048_NUM_CELLS, AUDIO_RATE> aSin4(SIN2048_DATA);
Oscil <SIN2048_NUM_CELLS, AUDIO_RATE> aSin5(SIN2048_DATA);
Oscil <SIN2048_NUM_CELLS, AUDIO_RATE> aSin6(SIN2048_DATA);
Oscil <SIN2048_NUM_CELLS, AUDIO_RATE> aSin7(SIN2048_DATA);
Oscil <SIN2048_NUM_CELLS, AUDIO_RATE> aSin8(SIN2048_DATA);

#define CONTROL_RATE 32 // Hz, powers of 2 are most reliable

int freq1 = 110;//base freq of OSC1
int freq1_old = 110;
int voct = 1000;//external V/OCT LSB
int voct_old = 1000;
int freqv1 = 440;// freq1 apply voct
int harm_knob = 0;//AD wave knob
int harm_knob_old = 0;//AD wave knob
byte gain = 127;

const static float voctpow[1024] PROGMEM = {
 0,  0.004882, 0.009765, 0.014648, 0.019531, 0.024414, 0.029296, 0.034179, 0.039062, 0.043945, 0.048828, 0.05371,  0.058593, 0.063476, 0.068359, 0.073242, 0.078125, 0.083007, 0.08789,  0.092773, 0.097656, 0.102539, 0.107421, 0.112304, 0.117187, 0.12207,  0.126953, 0.131835, 0.136718, 0.141601, 0.146484, 0.151367, 0.15625,  0.161132, 0.166015, 0.170898, 0.175781, 0.180664, 0.185546, 0.190429, 0.195312, 0.200195, 0.205078, 0.20996,  0.214843, 0.219726, 0.224609, 0.229492, 0.234375, 0.239257, 0.24414,  0.249023, 0.253906, 0.258789, 0.263671, 0.268554, 0.273437, 0.27832,  0.283203, 0.288085, 0.292968, 0.297851, 0.302734, 0.307617, 0.3125, 0.317382, 0.322265, 0.327148, 0.332031, 0.336914, 0.341796, 0.346679, 0.351562, 0.356445, 0.361328, 0.36621,  0.371093, 0.375976, 0.380859, 0.385742, 0.390625, 0.395507, 0.40039,  0.405273, 0.410156, 0.415039, 0.419921, 0.424804, 0.429687, 0.43457,  0.439453, 0.444335, 0.449218, 0.454101, 0.458984, 0.463867, 0.46875,  0.473632, 0.478515, 0.483398, 0.488281, 0.493164, 0.498046, 0.502929, 0.507812, 0.512695, 0.517578, 0.52246,  0.527343, 0.532226, 0.537109, 0.541992, 0.546875, 0.551757, 0.55664,  0.561523, 0.566406, 0.571289, 0.576171, 0.581054, 0.585937, 0.59082,  0.595703, 0.600585, 0.605468, 0.610351, 0.615234, 0.620117, 0.625,  0.629882, 0.634765, 0.639648, 0.644531, 0.649414, 0.654296, 0.659179, 0.664062, 0.668945, 0.673828, 0.67871,  0.683593, 0.688476, 0.693359, 0.698242, 0.703125, 0.708007, 0.71289,  0.717773, 0.722656, 0.727539, 0.732421,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
{ 2,  2,  2,  2,  3,  3,  3,  4,  4,  4,  4,  4,  4,  5,  5,  6,  6,  6,  7,  7,  8,  8,  8,  8,  8,  10, 10, 10, 12, 12, 14, 14, 14, 15, 15, 15, 15, 16, 16, 16, 16, 16, 16, 16, 16, 16, 16, 16, 16, 16, 16, 16, 16, 16, 16, 16, 16, 16, 16, 16, 16, 16, 15, 15, 15, 15, 14, 14, 14, 12, 12, 12, 10, 10, 8,  8,  8,  8,  8,  7,  7,  6,  6,  6,  5,  5,  4,  4,  4,  4,  4,  4,  3,  3,  3,  2,  2,  2,  2,  2,  2,  2,  2,  2,  2,  2,  2,  2,  2,  2,  2,  2,  2,  2,  2,  2,  2,  2,  2,  2,  2,  2,  2,  2,  3,  3,  3,  4,  4,  4,  4,  4,  4,  5,  5,  6,  6,  6,  7,  7,  8,  8,  8,  8,  8,  10, 10, 10, 12, 12, 14, 14, 14, 15, 15, 15, 15, 16, 16, 16, 16, 16, 16, 16, 16, 16, 16, 16, 16, 16, 16, 16, 16, 16, 16, 16, 16, 16, 16, 16, 16, 16, 16, 15, 15, 15, 14, 14, 14, 12, 12, 12, 10, 10, 8,  8,  8,  8,  8,  7,  7,  6,  6,  6,  5,  5,  4,  4,  4,  4,  4,  4,  3,  3,  3,  2,  2,  2,  2,  2,  2,  2,  2,  2,  2,  2,  2,  2,  2,  2,  2,  2,  2,  2,  2,  2,  2,  2,  2,  2,  2,  2,  2,  2,  3,  3,  3,  3,  4,  4,  4,  4,  4,  5,  5,  6 }
};

RollingAverage <unsigned int, 4> aRollingAverage;

void setup()
{
 startMozzi(CONTROL_RATE); // :)
}
void updateControl() {
 //harmonics
 harm_knob = (mozziAnalogRead(3) / 4) + (mozziAnalogRead(5) / 4);
 harm_knob = constrain(harm_knob, 0, 255);

 //harmonics_gain
 gain = (mozziAnalogRead(1) / 4) + (mozziAnalogRead(4) / 4);
 gain = constrain(gain, 0, 255);

 //OSC frequency knob
 freq1 = mozziAnalogRead(0) / 8 ;

 //frequency setting
 voct = mozziAnalogRead(7) ;
 if ((voct != voct_old) || (freq1 != freq1_old) || (harm_knob != harm_knob_old))
 {
   freqv1 = freq1 * pow(2, (pgm_read_float(&(voctpow[voct])))); // V/oct apply
  
   aSin1.setFreq(freqv1); // set the frequency
   aSin2.setFreq(freqv1 * (pgm_read_byte(&(harm_table[0][harm_knob])))); 
   aSin3.setFreq(freqv1 * (pgm_read_byte(&(harm_table[1][harm_knob])))); 
   aSin4.setFreq(freqv1 * (pgm_read_byte(&(harm_table[2][harm_knob])))); 
   aSin5.setFreq(freqv1 * (pgm_read_byte(&(harm_table[3][harm_knob])))); 
   aSin6.setFreq(freqv1 * (pgm_read_byte(&(harm_table[4][harm_knob])))); 
   aSin7.setFreq(freqv1 * (pgm_read_byte(&(harm_table[5][harm_knob])))); 
   aSin8.setFreq(freqv1 * (pgm_read_byte(&(harm_table[6][harm_knob]))));
   voct_old=voct; 
   freq1_old=freq1;
   harm_knob_old=harm_knob;
 }
}
int updateAudio() {
 return MonoOutput::from8Bit(aRollingAverage.next(aSin1.next() * (pgm_read_byte(&(gain_table[0][gain]))) / 1024 + aSin2.next() * (pgm_read_byte(&(gain_table[1][gain]))) / 1024 + aSin3.next() * (pgm_read_byte(&(gain_table[2][gain]))) / 1024 + aSin4.next() * (pgm_read_byte(&(gain_table[3][gain]))) / 1024 + aSin5.next() * (pgm_read_byte(&(gain_table[4][gain]))) / 1024 + aSin6.next() * (pgm_read_byte(&(gain_table[5][gain]))) / 1024 + aSin7.next() * (pgm_read_byte(&(gain_table[6][gain]))) / 1024 + aSin8.next() * (pgm_read_byte(&(gain_table[7][gain]))) / 1024));
}
void loop() {
 audioHook(); // required here
}
