mzuelch/CATs-Eurosynth/Modules/HAGIWO/Sync LFO/Firmware/Original/HAGIWO Sync LFO/HAGIWO_Sync_LFO.ino/HAGIWO_Sync_LFO.ino.ino

#include <FlexiTimer2.h>
#include "Periphery.h"
#include <avr/io.h>

unsigned int frq = 60000; // PWM周波数。60kHzあたりまで機能するが、マージンとって50kHzとする。
float duty = 0.5; // duty比率
int count = 0;

byte mode = 1;//
//0=saw1
//1=saw2
//2=sine
//3=tri
//4=squ
//5=random
//6=steady

int set_freq = 1;//
int freq_max = 30;//外部クロック周期(*100usec)
int amp = 1;//change pwm duty
float amp_rate = 1.0;
int phase = 1;
int mod = 0;//self modulation

bool ext_injudge = 0;//0=use internal clock , 1 = use external clock
bool ext_pulse = 0;//0=no external in
bool old_ext_pulse = 0;
long ext_count = 0;
long ext_count_result = 0;
long old_ext_count_result = 0;
long ext_period = 0;
bool reset_count = 0;

//wave table
const static word saw1[1000] PROGMEM = {
 0,  1,  2,  3,  4,  5,  6,  7,  8,  9,  10, 11, 12, 13, 14, 15, 16, 17, 18, 19, 20, 21, 22, 23, 24, 25, 26, 27, 28, 29, 30, 31, 32, 33, 34, 35, 36, 37, 38, 39, 40, 41, 42, 43, 44, 45, 46, 47, 48, 49, 50, 51, 52, 53, 54, 55, 56, 57, 58, 59, 60, 61, 62, 63, 64, 65, 66, 67, 68, 69, 70, 71, 72, 73, 74, 75, 76, 77, 78, 79, 80, 81, 82, 83, 84, 85, 86, 87, 88, 89, 90, 91, 92, 93, 94, 95, 96, 97, 98, 99, 100,  101,  102,  103,  104,  105,  106,  107,  108,  109,  110,  111,  112,  113,  114,  115,  116,  117,  118,  119,  120,  121,  122,  123,  124,  125,  126,  127,  128,  129,  130,  131,  132,  133,  134,  135,  136,  137,  138,  139,  140,  141,  142,  143,  144,  145,  146,  147,  148,  149,  150,  151,  152,  153,  154,  155,  156,  157,  158,  159,  160,  161,  162,  163,  164,  165,  166,  167,  168,  169,  170,  171,  172,  173,  174,  175,  176,  177,  178,  179,  180,  181,  182,  183,  184,  185,  186,  187,  188,  189,  190,  191,  192,  193,  194,  195,  196,  197,  198,  199,  200,  201,  202,  203,  204,  205,  206,  207,  208,  209,  210,  211,  212,  213,  214,  215,  216,  217,  218,  219,  220,  221,  222,  223,  224,  225,  226,  227,  228,  229,  230,  231,  232,  233,  234,  235,  236,  237,  238,  239,  240,  241,  242,  243,  244,  245,  246,  247,  248,  249,  250,  251,  252,  253,  254,  255,  256,  257,  258,  259,  260,  261,  262,  263,  264,  265,  266,  267,  268,  269,  270,  271,  272,  273,  274,  275,  276,  277,  278,  279,  280,  281,  282,  2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
   mode = 0;//saw1
 }
 else if (WF >= 155 && WF < 352) {
   mode = 1;//saw2
 }
 else if (WF >= 352 && WF < 571) {
   mode = 2;//sin
 }
 else if (WF >= 571 && WF < 771) {
   mode = 3;//tri
 }
 else if (WF >= 771 && WF < 939) {
   mode = 4;//squ
 }
 else if (WF >= 939) {
   mode = 5;//random
 }


 //------------phase and internal clock set-------------------------------
 if (ext_injudge == 0) { //use internal clock , phase function off
   phase = 0;
   //    freq_max = 1+(analogRead(1))/5;
   int PH = analogRead(PhaseIn);
   freq_max = 1 + 0.0007 * PH * PH;
 }

 else if (ext_injudge == 1) { //use external clock , phase function on
   int PH = analogRead(PhaseIn);
   phase = map(PH, 0, 1023, 0, 999);
 }


 //------------selc modulation-------------------------------
 int MD = analogRead(ModIn);
 if (MD < 31) {
   mod = 0;//no modulation
 }
 else if (MD >= 31 && MD < 155) {
   mod = 1;//saw1
 }
 else if (MD >= 155 && MD < 352) {
   mod = 2;//saw2
 }
 else if (MD >= 352 && MD < 571) {
   mod = 3;//sin
 }
 else if (MD >= 571 && MD < 771) {
   mod = 4;//tri
 }
 else if (MD >= 771 && MD < 939) {
   mod = 5;//squ
 }
 else if (MD >= 939) {
   mod = 6;//random
 }

 switch (mod) {
   case 0:
     break;

   case 1:
     phase = phase + (pgm_read_word(&(saw1[count])));
     break;

   case 2:
     phase = phase + (pgm_read_word(&(saw2[count])));
     break;

   case 3:
     phase = phase + (pgm_read_word(&(sine[count])));
     break;

   case 4:
     phase = phase + (pgm_read_word(&(tri[count])));
     break;

   case 5:
     phase = phase + (pgm_read_word(&(squ[count])));
     break;

   case 6:
     phase = phase + (pgm_read_word(&(saw1[random(1, 1000)])));
     break;
 }

 //--------------amp set----------------
 amp = analogRead(AmpIn);
 amp = map(amp, 0, 1023, 1, 100);
 amp_rate = (float)amp / 100;


 //------------external in judge-------------------------------
 if ( ext_count > 160000 ) { //no external signal during 8 sec
   ext_injudge = 0;
 }
 else  {
   ext_injudge = 1;
 }


 //----------clock setting-------------

 if (ext_pulse == 1 && old_ext_pulse == 0) {
   old_ext_count_result = ext_count_result;//twice pulse average
   ext_count_result = ext_count;
   ext_period = (old_ext_count_result + ext_count_result) / 1960;
   freq_max = ext_period;
 }

 if ( old_ext_pulse == 0 && ext_pulse == 1  ) { //外部入力が有→無のとき
   ext_count = 0;
   count = 0;

 }
 // モード指定
 TCCR1A = 0b00100001;
 TCCR1B = 0b00100001;//分周比1

 // TOP値指定
 //OCR1A = (unsigned int)(16000000 / frq);

 // Duty比指定
 OCR1B = (unsigned int)(16000000  / frq * duty * amp_rate);

 // for development
 //  Serial.print(ext_injudge);
 //  Serial.print(",");
 //  Serial.print(analogRead(5));
 //  Serial.println("");
}

void timer_count() {

 ext_count ++;
 set_freq ++;
 
 if (set_freq >= freq_max) {
   set_freq = 0;

   count ++;
   if (count + phase >= 1000 && mode != 5) {
     count = count - 1000;
   }

   switch (mode) {
     case 0:
       duty = (float)(pgm_read_word(&(saw1[count + phase]))) / 1000;
       break;

     case 1:
       duty = (float)(pgm_read_word(&(saw2[count + phase]))) / 1000;
       break;

     case 2:
       duty = (float)(pgm_read_word(&(sine[count + phase]))) / 1000;
       break;

     case 3:
       duty = (float)(pgm_read_word(&(tri[count + phase]))) / 1000;
       break;

     case 4:
       duty = (float)(pgm_read_word(&(squ[count + phase]))) / 1000;
       break;
   }

   //random
   if (mode == 5) {
     count ++;
     if (count >= 250) {
       count = 0;
       duty = random(1, 1000);
       duty = duty / 1000;
     }
   }

   //steady
   if (mode == 6) {
     duty = 1;
   }
 }
 //analogWrite(PWMOut, (int)(duty*256));
}
