mzuelch/CATs-Eurosynth/Modules/HAGIWO/Sync LFO/Firmware/HAGIWO_EG_Sync_LFO.ino

#include <avr/io.h>//for fast PWM
#define PWMPin 10
#define TRIGPin 3

// This code is from the dual AD Envelope generator HAGIWO made.
//
// More Info here: https://note.com/solder_state/n/n6fb73eb1d8b8 and here https://www.youtube.com/watch?v=yAes5pS3ZTo
// 
// Pot 0 -> Attack time
// Pot 1 -> Release time
// pot 2 -> Voltage level
// Pot 3 -> curve shape (slow tri to steep exponential)

int atk1, rel1, lev1, con1, out1, count1;
//count -- 0 is not triggerd , 1 is attack duration , 2 is release duration.
bool in1, old_in1;
int i = 0;//CH1 count
int last_out1 = 0; //If retriggered at the release time, the CV voltage will be restarted from the middle of the line, not from zero.
long timer1 = 0;

const static byte curve[16][128] PROGMEM = {
  {0, 4, 7, 10, 14, 17, 21, 24, 27, 31, 34, 37, 40, 43, 46, 49, 52, 55, 58, 61, 64, 67, 70, 73, 76, 78, 81, 84, 87, 89, 92, 95, 97, 100, 102, 105, 107, 110, 112, 115, 117, 119, 122, 124, 126, 128, 131, 133, 135, 137, 140, 142, 144, 146, 148, 150, 152, 154, 156, 158, 160, 162, 164, 166, 168, 169, 171, 173, 175, 177, 178, 180, 182, 184, 185, 187, 189, 190, 192, 194, 195, 197, 198, 200, 202, 203, 205, 206, 208, 209, 210, 212, 213, 215, 216, 217, 219, 220, 221, 223, 224, 225, 227, 228, 229, 230, 232, 233, 234, 235, 237, 238, 239, 240, 241, 242, 243, 245, 246, 247, 248, 249, 250, 251, 252, 253, 254, 255},
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
  {0, 17, 33, 48, 62, 75, 87, 99, 109, 119, 128, 137, 145, 152, 159, 166, 172, 177, 183, 188, 192, 196, 200, 204, 208, 211, 214, 217, 219, 222, 224, 226, 228, 230, 231, 233, 235, 236, 237, 238, 240, 241, 242, 242, 243, 244, 245, 246, 246, 247, 247, 248, 248, 249, 249, 250, 250, 250, 251, 251, 251, 251, 252, 252, 252, 252, 253, 253, 253, 253, 253, 253, 253, 253, 254, 254, 254, 254, 254, 254, 254, 254, 254, 254, 254, 254, 254, 254, 254, 255, 255, 255, 255, 255, 255, 255, 255, 255, 255, 255, 255, 255, 255, 255, 255, 255, 255, 255, 255, 255, 255, 255, 255, 255, 255, 255, 255, 255, 255, 255, 255, 255, 255, 255, 255, 255, 255, 255}
};

void setup()
{
  Serial.begin(9600);
  pinMode(TRIGPin, INPUT) ;//Z button
  pinMode(PWMPin, OUTPUT) ;//accelx
  timer1 = micros();
  TCCR1B &= B11111000;//fast pwm setting
  TCCR1B |= B00000001;//fast pwm setting
  delay(50);
}

void loop()
{
  old_in1 = in1;
  in1 = digitalRead(TRIGPin);// trig input

  if (old_in1 == 0 && in1 == 1) {// if detect trigger
    if (count1 == 2) {
      last_out1 = out1;
    }
    else if (count1 != 2) {
      last_out1 = 0;
    }
    i = 0;//wave table count reset
    count1 = 1;//start attack duration
    atk1 = analogRead(0) * 12; // Pot 0
    rel1 = analogRead(1) * 16; // Pot 1
    lev1 = analogRead(3) / 4; // pot 2
    con1 = analogRead(5) / 64; // Pot3
  }

  else if (count1 == 1 && i > 127) {//attack duration end
    count1 = 2;//start release duration
  }
  else if (count1 == 2 && i > 255) {//release duration end
    count1 = 0;
  }

  //----------------------CV output buffer CH1-------------------------
  if (count1 == 1) {//attack
    if (atk1 <= 32) {//Minimize atk time
      i = 128;
      count1 = 2;
    }
    out1 = (pgm_read_byte(&(curve[con1][i])));//store output voltage value
    if (timer1 + atk1 <= micros()) {
      i++;
      timer1 = micros();
    }
  }

  else if (count1 == 2) {//release
    out1 = 255 - (pgm_read_byte(&(curve[con1][i - 128])));//store output voltage value
    if (timer1 + rel1 <= micros()) {
      i++;
      timer1 = micros();
    }
  }

  //----------------------CV output-------------------------
  PWM_OUT();//CV out
}
void PWM_OUT() {//PWM duty setting
  if (count1 == 1) {
    out1 = map(out1, 0, 255, last_out1, lev1);
  }
  else if (count1 == 2) {
    out1 = map(out1, 0, 255, 0, lev1);
  }
  analogWrite(PWMPin, out1);//PWM output
}
