mzuelch/CATs-Eurosynth/Modules/Slim Line/Sample&Hold SMD/Documentation/20230718_183401.jpg

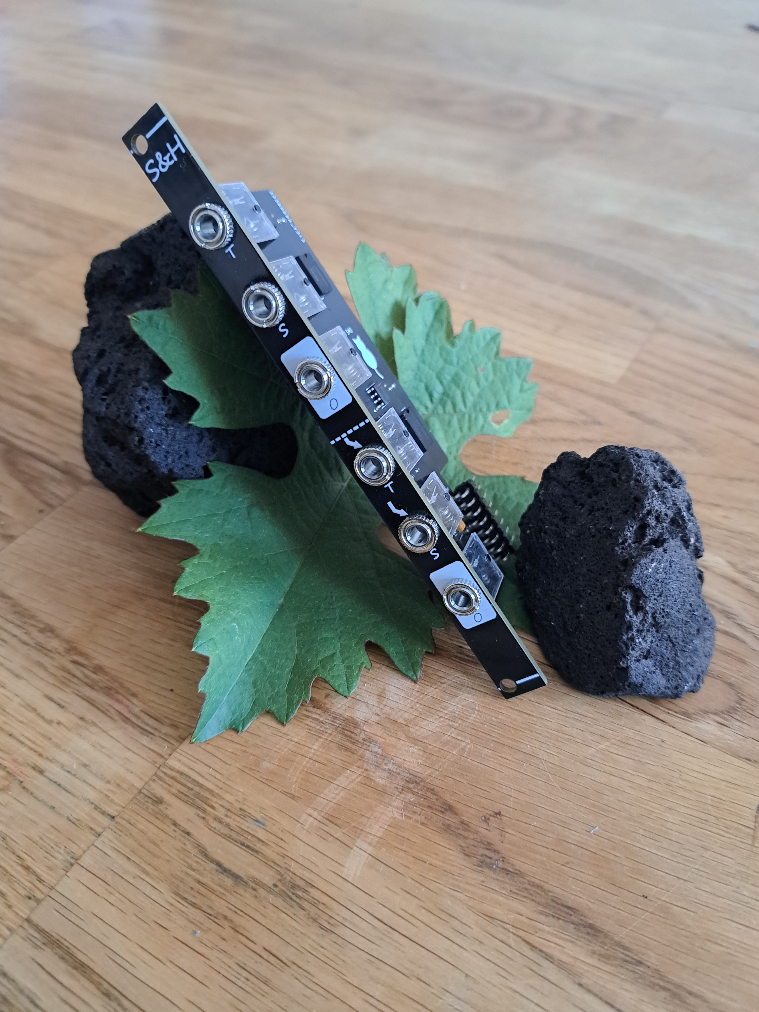
Modules/Slim Line/Sample&Hold SMD/Documentation/20230718_183401.jpg
